ComNets-Bremen/MoleNet/experiments/2026-power-consumption-and-voltage-measurement/data-sources/CNMoleNET-Data - data.csv

date and time (zulu, UTC) | device id | BME 280 |  |  | DS18B20 | TEROS 11/12 |  | TEROS 11/12 | TEROS 12 | Battery | raw data
 |  | humidity (%) | air pressure (hPa) | temp (°C) | temp (°C) | vwc (m^3/m^3) | temp (°C) | perm (raw) | econ (µS/cm) | U (V)
2026-05-27T22:04:44.877791803Z | igc-2025-06-19-otaa | 44.3 | 1,027 | 24.2 | 23.3 | 0.5% | 23.4 | 1806.16 | 0 | 4.8 | {"bme_hum":44.25,"bme_pres":1027.02001953125,"bme_temp":24.15999984741211,"ds_temp":23.3125,"soil_econ":0,"soil_perm":1806.1600341796875,"soil_temp":23.399999618530273,"vr_voltage":4.772337913513184}
2026-05-27T22:05:53.288547001Z | igc-2025-06-19-otaa | 44.7 | 1,027 | 24.2 | 23.3 | 0.5% | 23.5 | 1806.46 | 0 | 4.8 | {"bme_hum":44.720001220703125,"bme_pres":1027.02001953125,"bme_temp":24.15999984741211,"ds_temp":23.3125,"soil_econ":0,"soil_perm":1806.4599609375,"soil_temp":23.5,"vr_voltage":4.771189212799072}
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
