ComNets-Bremen/MoleNet/experiments/2024-LoRa_Gateway_for_WUSN/Field_Experiment/Field_experiment_2020_06_16.ods

jsonData.app_id | jsonData.dev_id | jsonData.hardware_serial | jsonData.port | jsonData.counter | jsonData.payload_raw | jsonData.payload_decoded | jsonData.metadata.time | jsonData.metadata.frequency | jsonData.metadata.modulation | jsonData.metadata.data_rate | jsonData.metadata.coding_rate | jsonData.metadata.downlink_url | gateway.gtw_id | gateway.timestamp | gateway.channel | gateway.rssi | gateway.snr | gateway.latitude | gateway.longitude | gateway.altitude | gateway.gtw_id | gateway.timestamp | gateway.channel | gateway.rssi | gateway.snr | gateway.latitude | gateway.longitude | gateway.altitude | gateway.gtw_id | gateway.timestamp | gateway.channel | gateway.rssi | gateway.snr | gateway.latitude | gateway.longitude | gateway.altitude
test_04_02_19 | pycomarduino | 0058924AB98D5AD4 | 1 | 0 | TW9pbgAAAAAAAAAAAAAAAAAAAAAAAAAAAAAAAAAAAAAAAAAAAAAAAA== | Moin | 2020-06-16T14:53:31.599425092Z | 867,1 | LORA | SF7BW125 | 4/5 | undefined | eui-fcc23dfffe0b696a | 3328727571 | 3 | -118 | -3,5 | undefined | undefined | undefined | eui-b827ebfffef74e1a | 2419173723 | 3 | -87 | 9,8 | undefined | undefined | undefined
test_04_02_19 | pycomarduino | 0058924AB98D5AD4 | 1 | 1 | WzJdIEQyMC8wNS8xOCB0MTI6MDAgVzAwMDAgVDAwMDAgPyAxICAgAA== | [2] D20/05/18 t12:00 W0000 T0000 ? 1 | 2020-06-16T14:54:06.672221982Z | 868,5 | LORA | SF7BW125 | 4/5 | undefined | eui-fcc23dfffe0b696a | 3363804923 | 2 | -111 | -0,5 | undefined | undefined | undefined | eui-b827ebfffef74e1a | 2454251091 | 2 | -81 | 6,8 | undefined | undefined | undefined
test_04_02_19 | pycomarduino | 0058924AB98D5AD4 | 1 | 2 | WzNdIEQyMC8wNS8xOCB0MTI6MDAgVzAwMDAgVDAwMDAgPyAxICAgAA== | [3] D20/05/18 t12:00 W0000 T0000 ? 1 | 2020-06-16T14:55:11.681204958Z | 868,1 | LORA | SF7BW125 | 4/5 | undefined | eui-b827ebfffef74e1a | 2519256003 | 0 | -84 | 9 | undefined | undefined | undefined
test_04_02_19 | pycomarduino | 0058924AB98D5AD4 | 1 | 3 | WzRdIEQyMC8wNS8xOCB0MTI6MDAgVzAwMDAgVDAwMDAgPyAxICAgAA== | [4] D20/05/18 t12:00 W0000 T0000 ? 1 | 2020-06-16T14:56:08.033887854Z | 867,3 | LORA | SF7BW125 | 4/5 | undefined | eui-fcc23dfffe0b696a | 3485164443 | 4 | -113 | -1 | undefined | undefined | undefined | eui-b827ebfffef74e1a | 2575610667 | 4 | -89 | 9,8 | undefined | undefined | undefined
test_04_02_19 | pycomarduino | 0058924AB98D5AD4 | 1 | 4 | WzVdIEQyMC8wNS8xOCB0MTI6MDAgVzAwMDAgVDAwMDAgPyAxICAgAA== | [5] D20/05/18 t12:00 W0000 T0000 ? 1 | 2020-06-16T14:57:21.798522547Z | 868,3 | LORA | SF7BW125 | 4/5 | undefined | eui-b827ebfffef74e1a | 2649370019 | 1 | -84 | 9,5 | undefined | undefined | undefined
test_04_02_19 | pycomarduino | 0058924AB98D5AD4 | 1 | 5 | WzJdIEQyMC8wNS8xOCB0MTI6MDAgVzAwMDAgVDAwMDAgPyAxICAgAA== | [2] D20/05/18 t12:00 W0000 T0000 ? 1 | 2020-06-16T15:14:06.673642956Z | 868,5 | LORA | SF7BW125 | 4/5 | undefined | eui-fcc23dfffe0b696a | 268839363 | 2 | -110 | -5 | undefined | undefined | undefined | eui-b827ebfffef74e1a | 3654253363 | 2 | -79 | 8,2 | undefined | undefined | undefined
test_04_02_19 | pycomarduino | 0058924AB98D5AD4 | 1 | 6 | WzNdIEQyMC8wNS8xOCB0MTI6MDAgVzAwMDAgVDAwMDAgPyAxICAgAA== | [3] D20/05/18 t12:00 W0000 T0000 ? 1 | 2020-06-16T15:15:11.674569835Z | 867,5 | LORA | SF7BW125 | 4/5 | undefined | eui-fcc23dfffe0b696a | 333838172 | 5 | -113 | -2,5 | undefined | undefined | undefined | eui-b827ebfffef74e1a | 3719252204 | 5 | -82 | 8,2 | undefined | undefined | undefined
test_04_02_19 | pycomarduino | 0058924AB98D5AD4 | 1 | 7 | WzRdIEQyMC8wNS8xOCB0MTI6MDAgVzAwMDAgVDAwMDAgPyAxICAgAA== | [4] D20/05/18 t12:00 W0000 T0000 ? 1 | 2020-06-16T15:16:08.037091434Z | 868,1 | LORA | SF7BW125 | 4/5 | undefined | eui-b827ebfffef74e1a | 3775609667 | 0 | -83 | 10,5 | undefined | undefined | undefined
test_04_02_19 | pycomarduino | 0058924AB98D5AD4 | 1 | 8 | WzVdIEQyMC8wNS8xOCB0MTI6MDAgVzAwMDAgVDAwMDAgPyAxICAgAA== | [5] D20/05/18 t12:00 W0000 T0000 ? 1 | 2020-06-16T15:17:21.792934437Z | 868,3 | LORA | SF7BW125 | 4/5 | undefined | eui-b827ebfffef74e1a | 3849370235 | 1 | -79 | 9 | undefined | undefined | undefined
test_04_02_19 | pycomarduino | 0058924AB98D5AD4 | 1 | 9 | WzJdIEQyMC8wNS8xOCB0MTI6MDAgVzAwMDAgVDAwMDAgPyAxICAgAA== | [2] D20/05/18 t12:00 W0000 T0000 ? 1 | 2020-06-16T15:34:06.673976816Z | 867,7 | LORA | SF7BW125 | 4/5 | undefined | eui-b827ebfffef74e1a | 559288812 | 6 | -81 | 9,5 | undefined | undefined | undefined
test_04_02_19 | pycomarduino | 0058924AB98D5AD4 | 1 | 10 | WzNdIEQyMC8wNS8xOCB0MTI6MDAgVzAwMDAgVDAwMDAgPyAxICAgAA== | [3] D20/05/18 t12:00 W0000 T0000 ? 1 | 2020-06-16T15:35:11.670229955Z | 868,5 | LORA | SF7BW125 | 4/5 | undefined | eui-fcc23dfffe0b696a | 1533834427 | 2 | -113 | -0,2 | undefined | undefined | undefined | eui-b827ebfffef74e1a | 624281723 | 2 | -78 | 7,8 | undefined | undefined | undefined
test_04_02_19 | pycomarduino | 0058924AB98D5AD4 | 1 | 11 | WzRdIEQyMC8wNS8xOCB0MTI6MDAgVzAwMDAgVDAwMDAgPyAxICAgAA== | [4] D20/05/18 t12:00 W0000 T0000 ? 1 | 2020-06-16T15:36:08.033661887Z | 868,1 | LORA | SF7BW125 | 4/5 | undefined | eui-fcc23dfffe0b696a | 1590194867 | 0 | -116 | -0,8 | undefined | undefined | undefined | eui-b827ebfffef74e1a | 680642187 | 0 | -80 | 9,2 | undefined | undefined | undefined
test_04_02_19 | pycomarduino | 0058924AB98D5AD4 | 1 | 12 | WzVdIEQyMC8wNS8xOCB0MTI6MDAgVzAwMDAgVDAwMDAgPyAxICAgAA== | [5] D20/05/18 t12:00 W0000 T0000 ? 1 | 2020-06-16T15:37:21.792145476Z | 867,9 | LORA | SF7BW125 | 4/5 | undefined | eui-fcc23dfffe0b696a | 1663957532 | 7 | -114 | -3,8 | undefined | undefined | undefined | eui-b827ebfffef74e1a | 754404892 | 7 | -81 | 8,8 | undefined | undefined | undefined
test_04_02_19 | pycomarduino | 0058924AB98D5AD4 | 1 | 13 | WzJdIEQyMC8wNS8xOCB0MTI6MDAgVzAwMDAgVDAwMDAgPyAxICAgAA== | [2] D20/05/18 t12:00 W0000 T0000 ? 1 | 2020-06-16T15:54:06.68129469Z | 868,3 | LORA | SF7BW125 | 4/5 | undefined | eui-fcc23dfffe0b696a | 2668845763 | 1 | -109 | -2 | undefined | undefined | undefined | eui-b827ebfffef74e1a | 1759293595 | 1 | -78 | 9,2 | undefined | undefined | undefined
test_04_02_19 | pycomarduino | 0058924AB98D5AD4 | 1 | 14 | WzNdIEQyMC8wNS8xOCB0MTI6MDAgVzAwMDAgVDAwMDAgPyAxICAgAA== | [3] D20/05/18 t12:00 W0000 T0000 ? 1 | 2020-06-16T15:55:12.092174171Z | 867,1 | LORA | SF7BW125 | 4/5 | undefined | eui-fcc23dfffe0a9698 | 2735896363 | 3 | -117 | -6,5 | undefined | undefined | undefined | eui-fcc23dfffe0b696a | 2733832667 | 3 | -113 | 0,5 | undefined | undefined | undefined
test_04_02_19 | pycomarduino | 0058924AB98D5AD4 | 1 | 15 | WzRdIEQyMC8wNS8xOCB0MTI6MDAgVzAwMDAgVDAwMDAgPyAxICAgAA== | [4] D20/05/18 t12:00 W0000 T0000 ? 1 | 2020-06-16T15:56:08.032269197Z | 868,5 | LORA | SF7BW125 | 4/5 | undefined | eui-fcc23dfffe0b696a | 2790196011 | 2 | -112 | 2 | undefined | undefined | undefined | eui-b827ebfffef74e1a | 1880643899 | 2 | -81 | 8,2 | undefined | undefined | undefined
test_04_02_19 | pycomarduino | 0058924AB98D5AD4 | 1 | 16 | WzVdIEQyMC8wNS8xOCB0MTI6MDAgVzAwMDAgVDAwMDAgPyAxICAgAA== | [5] D20/05/18 t12:00 W0000 T0000 ? 1 | 2020-06-16T15:57:21.802305841Z | 868,1 | LORA | SF7BW125 | 4/5 | undefined | eui-fcc23dfffe0b696a | 2863960219 | 0 | -114 | 0 | undefined | undefined | undefined | eui-b827ebfffef74e1a | 1954408147 | 0 | -81 | 9,2 | undefined | undefined | undefined
test_04_02_19 | pycomarduino | 0058924AB98D5AD4 | 1 | 17 | WzJdIEQyMC8wNS8xOCB0MTI6MDAgVzAwMDAgVDAwMDAgPyAxICAgAA== | [2] D20/05/18 t12:00 W0000 T0000 ? 1 | 2020-06-16T16:14:06.683690365Z | 867,3 | LORA | SF7BW125 | 4/5 | undefined | eui-fcc23dfffe0a9698 | 3870911195 | 4 | -114 | -7 | undefined | undefined | undefined | eui-fcc23dfffe0b696a | 3868847787 | 4 | -116 | -0,5 | undefined | undefined | undefined | eui-b827ebfffef74e1a | 2959296179 | 4 | -83 | 9,5 | undefined | undefined | undefined
test_04_02_19 | pycomarduino | 0058924AB98D5AD4 | 1 | 18 | WzNdIEQyMC8wNS8xOCB0MTI6MDAgVzAwMDAgVDAwMDAgPyAxICAgAA== | [3] D20/05/18 t12:00 W0000 T0000 ? 1 | 2020-06-16T16:15:11.673342268Z | 868,3 | LORA | SF7BW125 | 4/5 | undefined | eui-b827ebfffef74e1a | 3024277347 | 1 | -81 | 9,2 | undefined | undefined | undefined
test_04_02_19 | pycomarduino | 0058924AB98D5AD4 | 1 | 19 | WzRdIEQyMC8wNS8xOCB0MTI6MDAgVzAwMDAgVDAwMDAgPyAxICAgAA== | [4] D20/05/18 t12:00 W0000 T0000 ? 1 | 2020-06-16T16:16:08.036932471Z | 868,5 | LORA | SF7BW125 | 4/5 | undefined | eui-b827ebfffef74e1a | 3080643547 | 2 | -81 | 8 | undefined | undefined | undefined
test_04_02_19 | pycomarduino | 0058924AB98D5AD4 | 1 | 20 | WzVdIEQyMC8wNS8xOCB0MTI6MDAgVzAwMDAgVDAwMDAgPyAxICAgAA== | [5] D20/05/18 t12:00 W0000 T0000 ? 1 | 2020-06-16T16:17:21.795494424Z | 867,5 | LORA | SF7BW125 | 4/5 | undefined | eui-fcc23dfffe0b696a | 4063960396 | 5 | -110 | 1 | undefined | undefined | undefined | eui-b827ebfffef74e1a | 3154408876 | 5 | -82 | 6,5 | undefined | undefined | undefined
test_04_02_19 | pycomarduino | 0058924AB98D5AD4 | 1 | 21 | WzJdIEQyMC8wNS8xOCB0MTI6MDAgVzAwMDAgVDAwMDAgPyAxICAgAA== | [2] D20/05/18 t12:00 W0000 T0000 ? 1 | 2020-06-16T16:34:06.686978924Z | 868,1 | LORA | SF7BW125 | 4/5 | undefined | eui-fcc23dfffe0b696a | 773884587 | 0 | -115 | -5,2 | undefined | undefined | undefined | eui-b827ebfffef74e1a | 4159300827 | 0 | -81 | 9,2 | undefined | undefined | undefined
test_04_02_19 | pycomarduino | 0058924AB98D5AD4 | 1 | 22 | WzNdIEQyMC8wNS8xOCB0MTI6MDAgVzAwMDAgVDAwMDAgPyAxICAgAA== | [3] D20/05/18 t12:00 W0000 T0000 ? 1 | 2020-06-16T16:35:11.668860894Z | 867,7 | LORA | SF7BW125 | 4/5 | undefined | eui-fcc23dfffe0b696a | 838859828 | 6 | -116 | -4,8 | undefined | undefined | undefined | eui-b827ebfffef74e1a | 4224276100 | 6 | -82 | 9,2 | undefined | undefined | undefined
test_04_02_19 | pycomarduino | 0058924AB98D5AD4 | 1 | 23 | WzRdIEQyMC8wNS8xOCB0MTI6MDAgVzAwMDAgVDAwMDAgPyAxICAgAA== | [4] D20/05/18 t12:00 W0000 T0000 ? 1 | 2020-06-16T16:36:08.064774084Z | 868,3 | LORA | SF7BW125 | 4/5 | undefined | eui-b827ebfffef74e1a | 4280645107 | 1 | -81 | 10,8 | undefined | undefined | undefined
test_04_02_19 | pycomarduino | 0058924AB98D5AD4 | 1 | 24 | WzVdIEQyMC8wNS8xOCB0MTI6MDAgVzAwMDAgVDAwMDAgPyAxICAgAA== | [5] D20/05/18 t12:00 W0000 T0000 ? 1 | 2020-06-16T16:37:21.796384426Z | 868,5 | LORA | SF7BW125 | 4/5 | undefined | eui-fcc23dfffe0b696a | 968995283 | 2 | -111 | 0,8 | undefined | undefined | undefined | eui-b827ebfffef74e1a | 59444323 | 2 | -81 | 7,5 | undefined | undefined | undefined
test_04_02_19 | pycomarduino | 0058924AB98D5AD4 | 1 | 25 | WzJdIEQyMC8wNS8xOCB0MTI6MDAgVzAwMDAgVDAwMDAgPyAxICAgAA== | [2] D20/05/18 t12:00 W0000 T0000 ? 1 | 2020-06-16T16:54:06.693254479Z | 867,9 | LORA | SF7BW125 | 4/5 | undefined | eui-fcc23dfffe0b696a | 1973886556 | 7 | -116 | -1 | undefined | undefined | undefined | eui-b827ebfffef74e1a | 1064336052 | 7 | -84 | 10,8 | undefined | undefined | undefined
test_04_02_19 | pycomarduino | 0058924AB98D5AD4 | 1 | 26 | WzNdIEQyMC8wNS8xOCB0MTI6MDAgVzAwMDAgVDAwMDAgPyAxICAgAA== | [3] D20/05/18 t12:00 W0000 T0000 ? 1 | 2020-06-16T16:55:11.660936483Z | 868,1 | LORA | SF7BW125 | 4/5 | undefined | eui-fcc23dfffe0b696a | 2038855931 | 0 | -116 | -2 | undefined | undefined | undefined | eui-b827ebfffef74e1a | 1129305459 | 0 | -82 | 9 | undefined | undefined | undefined
test_04_02_19 | pycomarduino | 0058924AB98D5AD4 | 1 | 27 | WzRdIEQyMC8wNS8xOCB0MTI6MDAgVzAwMDAgVDAwMDAgPyAxICAgAA== | [4] D20/05/18 t12:00 W0000 T0000 ? 1 | 2020-06-16T16:56:08.03732124Z | 868,3 | LORA | SF7BW125 | 4/5 | undefined | eui-b827ebfffef74e1a | 1185677387 | 1 | -83 | 10,5 | undefined | undefined | undefined
test_04_02_19 | pycomarduino | 0058924AB98D5AD4 | 1 | 28 | WzVdIEQyMC8wNS8xOCB0MTI6MDAgVzAwMDAgVDAwMDAgPyAxICAgAA== | [5] D20/05/18 t12:00 W0000 T0000 ? 1 | 2020-06-16T16:57:21.795728348Z | 867,1 | LORA | SF7BW125 | 4/5 | undefined | eui-fcc23dfffe0a9698 | 2171058003 | 3 | -117 | -6,2 | undefined | undefined | undefined | eui-fcc23dfffe0b696a | 2168995275 | 3 | -117 | 0,2 | undefined | undefined | undefined | eui-b827ebfffef74e1a | 1259444867 | 3 | -89 | 10 | undefined | undefined | undefined
test_04_02_19 | pycomarduino | 0058924AB98D5AD4 | 1 | 29 | WzJdIEQyMC8wNS8xOCB0MTI6MDAgVzAwMDAgVDAwMDAgPyAxICAgAA== | [2] D20/05/18 t12:00 W0000 T0000 ? 1 | 2020-06-16T17:14:06.811791944Z | 868,5 | LORA | SF7BW125 | 4/5 | undefined | eui-fcc23dfffe0b696a | 3173890507 | 2 | -112 | -1 | undefined | undefined | undefined | eui-b827ebfffef74e1a | 2264340579 | 2 | -78 | 7,2 | undefined | undefined | undefined
test_04_02_19 | pycomarduino | 0058924AB98D5AD4 | 1 | 30 | WzNdIEQyMC8wNS8xOCB0MTI6MDAgVzAwMDAgVDAwMDAgPyAxICAgAA== | [3] D20/05/18 t12:00 W0000 T0000 ? 1 | 2020-06-16T17:15:11.66316184Z | 867,3 | LORA | SF7BW125 | 4/5 | undefined | eui-fcc23dfffe0b696a | 3238853939 | 4 | -112 | -0,2 | undefined | undefined | undefined | eui-b827ebfffef74e1a | 2329304043 | 4 | -84 | 8,8 | undefined | undefined | undefined
test_04_02_19 | pycomarduino | 0058924AB98D5AD4 | 1 | 31 | WzRdIEQyMC8wNS8xOCB0MTI6MDAgVzAwMDAgVDAwMDAgPyAxICAgAA== | [4] D20/05/18 t12:00 W0000 T0000 ? 1 | 2020-06-16T17:16:08.035037617Z | 868,1 | LORA | SF7BW125 | 4/5 | undefined | eui-fcc23dfffe0b696a | 3295228675 | 0 | -117 | -2,8 | undefined | undefined | undefined | eui-b827ebfffef74e1a | 2385678795 | 0 | -80 | 9,5 | undefined | undefined | undefined
test_04_02_19 | pycomarduino | 0058924AB98D5AD4 | 1 | 32 | WzVdIEQyMC8wNS8xOCB0MTI6MDAgVzAwMDAgVDAwMDAgPyAxICAgAA== | [5] D20/05/18 t12:00 W0000 T0000 ? 1 | 2020-06-16T17:17:21.858784072Z | 868,3 | LORA | SF7BW125 | 4/5 | undefined | eui-b827ebfffef74e1a | 2459447443 | 1 | -83 | 10,5 | undefined | undefined | undefined
test_04_02_19 | pycomarduino | 0058924AB98D5AD4 | 1 | 33 | WzJdIEQyMC8wNS8xOCB0MTI6MDAgVzAwMDAgVDAwMDAgPyAxICAgAA== | [2] D20/05/18 t12:00 W0000 T0000 ? 1 | 2020-06-16T17:34:06.705127726Z | 867,5 | LORA | SF7BW125 | 4/5 | undefined | eui-fcc23dfffe0b696a | 78925188 | 5 | -113 | -0,8 | undefined | undefined | undefined | eui-b827ebfffef74e1a | 3464343124 | 5 | -83 | 7,5 | undefined | undefined | undefined
test_04_02_19 | pycomarduino | 0058924AB98D5AD4 | 1 | 34 | WzNdIEQyMC8wNS8xOCB0MTI6MDAgVzAwMDAgVDAwMDAgPyAxICAgAA== | [3] D20/05/18 t12:00 W0000 T0000 ? 1 | 2020-06-16T17:35:11.658218556Z | 868,5 | LORA | SF7BW125 | 4/5 | undefined | eui-fcc23dfffe0b696a | 143882587 | 2 | -112 | 0,5 | undefined | undefined | undefined | eui-b827ebfffef74e1a | 3529300563 | 2 | -78 | 6,2 | undefined | undefined | undefined
test_04_02_19 | pycomarduino | 0058924AB98D5AD4 | 1 | 35 | WzRdIEQyMC8wNS8xOCB0MTI6MDAgVzAwMDAgVDAwMDAgPyAxICAgAA== | [4] D20/05/18 t12:00 W0000 T0000 ? 1 | 2020-06-16T17:36:08.030161564Z | 868,1 | LORA | SF7BW125 | 4/5 | undefined | eui-fcc23dfffe0b696a | 200260139 | 0 | -115 | -0,5 | undefined | undefined | undefined | eui-b827ebfffef74e1a | 3585678139 | 0 | -84 | 10,5 | undefined | undefined | undefined
test_04_02_19 | pycomarduino | 0058924AB98D5AD4 | 1 | 36 | WzVdIEQyMC8wNS8xOCB0MTI6MDAgVzAwMDAgVDAwMDAgPyAxICAgAA== | [5] D20/05/18 t12:00 W0000 T0000 ? 1 | 2020-06-16T17:37:21.808602749Z | 867,7 | LORA | SF7BW125 | 4/5 | undefined | eui-fcc23dfffe0b696a | 274029788 | 6 | -116 | -6,2 | undefined | undefined | undefined | eui-b827ebfffef74e1a | 3659447820 | 6 | -83 | 10 | undefined | undefined | undefined
test_04_02_19 | pycomarduino | 0058924AB98D5AD4 | 1 | 37 | WzJdIEQyMC8wNS8xOCB0MTI6MDAgVzAwMDAgVDAwMDAgPyAxICAgAA== | [2] D20/05/18 t12:00 W0000 T0000 ? 1 | 2020-06-16T17:54:06.856794594Z | 868,3 | LORA | SF7BW125 | 4/5 | undefined | eui-b827ebfffef74e1a | 369534723 | 1 | -81 | 9,2 | undefined | undefined | undefined
test_04_02_19 | pycomarduino | 0058924AB98D5AD4 | 1 | 38 | WzNdIEQyMC8wNS8xOCB0MTI6MDAgVzAwMDAgVDAwMDAgPyAxICAgAA== | [3] D20/05/18 t12:00 W0000 T0000 ? 1 | 2020-06-16T17:55:11.65666038Z | 867,9 | LORA | SF7BW125 | 4/5 | undefined | eui-fcc23dfffe0b696a | 1343880468 | 7 | -117 | -2,2 | undefined | undefined | undefined | eui-b827ebfffef74e1a | 434331716 | 7 | -84 | 9,5 | undefined | undefined | undefined
test_04_02_19 | pycomarduino | 0058924AB98D5AD4 | 1 | 39 | WzRdIEQyMC8wNS8xOCB0MTI6MDAgVzAwMDAgVDAwMDAgPyAxICAgAA== | [4] D20/05/18 t12:00 W0000 T0000 ? 1 | 2020-06-16T17:56:08.186396041Z | 868,5 | LORA | SF7BW125 | 4/5 | undefined | eui-fcc23dfffe0b696a | 1400409291 | 2 | -111 | -1,5 | undefined | undefined | undefined | eui-b827ebfffef74e1a | 490860571 | 2 | -81 | 7,2 | undefined | undefined | undefined
test_04_02_19 | pycomarduino | 0058924AB98D5AD4 | 1 | 40 | WzVdIEQyMC8wNS8xOCB0MTI6MDAgVzAwMDAgVDAwMDAgPyAxICAgAA== | [5] D20/05/18 t12:00 W0000 T0000 ? 1 | 2020-06-16T17:57:21.805076581Z | 868,1 | LORA | SF7BW125 | 4/5 | undefined | eui-fcc23dfffe0b696a | 1474031643 | 0 | -117 | -1,8 | undefined | undefined | undefined | eui-b827ebfffef74e1a | 564482955 | 0 | -83 | 10 | undefined | undefined | undefined
test_04_02_19 | pycomarduino | 0058924AB98D5AD4 | 1 | 41 | WzJdIEQyMC8wNS8xOCB0MTI6MDAgVzAwMDAgVDAwMDAgPyAxICAgAA== | [2] D20/05/18 t12:00 W0000 T0000 ? 1 | 2020-06-16T18:14:06.707336104Z | 867,1 | LORA | SF7BW125 | 4/5 | undefined | eui-fcc23dfffe0b696a | 2478931003 | 3 | -113 | 0,5 | undefined | undefined | undefined | eui-b827ebfffef74e1a | 1569382803 | 3 | -88 | 8,8 | undefined | undefined | undefined
test_04_02_19 | pycomarduino | 0058924AB98D5AD4 | 1 | 42 | WzNdIEQyMC8wNS8xOCB0MTI6MDAgVzAwMDAgVDAwMDAgPyAxICAgAA== | [3] D20/05/18 t12:00 W0000 T0000 ? 1 | 2020-06-16T18:15:11.651606129Z | 868,3 | LORA | SF7BW125 | 4/5 | undefined | eui-b827ebfffef74e1a | 1634328195 | 1 | -81 | 10,5 | undefined | undefined | undefined
test_04_02_19 | pycomarduino | 0058924AB98D5AD4 | 1 | 43 | WzRdIEQyMC8wNS8xOCB0MTI6MDAgVzAwMDAgVDAwMDAgPyAxICAgAA== | [4] D20/05/18 t12:00 W0000 T0000 ? 1 | 2020-06-16T18:16:08.030428368Z | 868,5 | LORA | SF7BW125 | 4/5 | undefined | eui-b827ebfffef74e1a | 1690711299 | 2 | -79 | 7,2 | undefined | undefined | undefined
test_04_02_19 | pycomarduino | 0058924AB98D5AD4 | 1 | 44 | WzVdIEQyMC8wNS8xOCB0MTI6MDAgVzAwMDAgVDAwMDAgPyAxICAgAA== | [5] D20/05/18 t12:00 W0000 T0000 ? 1 | 2020-06-16T18:17:21.845341058Z | 867,3 | LORA | SF7BW125 | 4/5 | undefined | eui-fcc23dfffe0b696a | 2674031459 | 4 | -116 | -1,2 | undefined | undefined | undefined
test_04_02_19 | pycomarduino | 0058924AB98D5AD4 | 1 | 45 | WzJdIEQyMC8wNS8xOCB0MTI6MDAgVzAwMDAgVDAwMDAgPyAxICAgAA== | [2] D20/05/18 t12:00 W0000 T0000 ? 1 | 2020-06-16T18:34:06.705918387Z | 868,1 | LORA | SF7BW125 | 4/5 | undefined | eui-fcc23dfffe0b696a | 3678934891 | 0 | -116 | -3,2 | undefined | undefined | undefined | eui-b827ebfffef74e1a | 2769387267 | 0 | -83 | 8,8 | undefined | undefined | undefined
test_04_02_19 | pycomarduino | 0058924AB98D5AD4 | 1 | 46 | WzNdIEQyMC8wNS8xOCB0MTI6MDAgVzAwMDAgVDAwMDAgPyAxICAgAA== | [3] D20/05/18 t12:00 W0000 T0000 ? 1 | 2020-06-16T18:35:11.647147708Z | 867,5 | LORA | SF7BW125 | 4/5 | undefined | eui-fcc23dfffe0b696a | 3743874124 | 5 | -113 | -1 | undefined | undefined | undefined | eui-b827ebfffef74e1a | 2834326524 | 5 | -85 | 7,5 | undefined | undefined | undefined
test_04_02_19 | pycomarduino | 0058924AB98D5AD4 | 1 | 47 | WzRdIEQyMC8wNS8xOCB0MTI6MDAgVzAwMDAgVDAwMDAgPyAxICAgAA== | [4] D20/05/18 t12:00 W0000 T0000 ? 1 | 2020-06-16T18:36:08.03216962Z | 868,3 | LORA | SF7BW125 | 4/5 | undefined | eui-b827ebfffef74e1a | 2890712443 | 1 | -79 | 9,8 | undefined | undefined | undefined
test_04_02_19 | pycomarduino | 0058924AB98D5AD4 | 1 | 48 | WzVdIEQyMC8wNS8xOCB0MTI6MDAgVzAwMDAgVDAwMDAgPyAxICAgAA== | [5] D20/05/18 t12:00 W0000 T0000 ? 1 | 2020-06-16T18:37:21.806620651Z | 868,5 | LORA | SF7BW125 | 4/5 | undefined | eui-fcc23dfffe0b696a | 3874033171 | 2 | -115 | -0,8 | undefined | undefined | undefined | eui-b827ebfffef74e1a | 2964485635 | 2 | -81 | 7,2 | undefined | undefined | undefined
test_04_02_19 | pycomarduino | 0058924AB98D5AD4 | 1 | 49 | WzJdIEQyMC8wNS8xOCB0MTI6MDAgVzAwMDAgVDAwMDAgPyAxICAgAA== | [2] D20/05/18 t12:00 W0000 T0000 ? 1 | 2020-06-16T18:54:06.713331254Z | 867,7 | LORA | SF7BW125 | 4/5 | undefined | eui-fcc23dfffe0b696a | 583969412 | 6 | -115 | -4,2 | undefined | undefined | undefined | eui-b827ebfffef74e1a | 3969389652 | 6 | -83 | 10,5 | undefined | undefined | undefined
test_04_02_19 | pycomarduino | 0058924AB98D5AD4 | 1 | 50 | WzNdIEQyMC8wNS8xOCB0MTI6MDAgVzAwMDAgVDAwMDAgPyAxICAgAA== | [3] D20/05/18 t12:00 W0000 T0000 ? 1 | 2020-06-16T18:55:11.648111888Z | 868,1 | LORA | SF7BW125 | 4/5 | undefined | eui-b827ebfffef74e1a | 4034322795 | 0 | -82 | 9,2 | undefined | undefined | undefined
test_04_02_19 | pycomarduino | 0058924AB98D5AD4 | 1 | 51 | WzRdIEQyMC8wNS8xOCB0MTI6MDAgVzAwMDAgVDAwMDAgPyAxICAgAA== | [4] D20/05/18 t12:00 W0000 T0000 ? 1 | 2020-06-16T18:56:08.035486607Z | 868,3 | LORA | SF7BW125 | 4/5 | undefined | eui-b827ebfffef74e1a | 4090711435 | 1 | -81 | 11 | undefined | undefined | undefined
test_04_02_19 | pycomarduino | 0058924AB98D5AD4 | 1 | 52 | WzVdIEQyMC8wNS8xOCB0MTI6MDAgVzAwMDAgVDAwMDAgPyAxICAgAA== | [5] D20/05/18 t12:00 W0000 T0000 ? 1 | 2020-06-16T18:57:21.807250315Z | 867,9 | LORA | SF7BW125 | 4/5 | undefined | eui-fcc23dfffe0b696a | 779065564 | 7 | -117 | -0,2 | undefined | undefined | undefined | eui-b827ebfffef74e1a | 4164485900 | 7 | -83 | 9,2 | undefined | undefined | undefined
test_04_02_19 | pycomarduino | 0058924AB98D5AD4 | 1 | 53 | WzJdIEQyMC8wNS8xOCB0MTI6MDAgVzAwMDAgVDAwMDAgPyAxICAgAA== | [2] D20/05/18 t12:00 W0000 T0000 ? 1 | 2020-06-16T19:14:06.73096524Z | 868,5 | LORA | SF7BW125 | 4/5 | undefined | eui-b827ebfffef74e1a | 874426843 | 2 | -81 | 8 | undefined | undefined | undefined
test_04_02_19 | pycomarduino | 0058924AB98D5AD4 | 1 | 54 | WzNdIEQyMC8wNS8xOCB0MTI6MDAgVzAwMDAgVDAwMDAgPyAxICAgAA== | [3] D20/05/18 t12:00 W0000 T0000 ? 1 | 2020-06-16T19:15:11.646600965Z | 867,1 | LORA | SF7BW125 | 4/5 | undefined | eui-fcc23dfffe0a9698 | 1850960923 | 3 | -117 | -9 | undefined | undefined | undefined | eui-fcc23dfffe0b696a | 1848900203 | 3 | -113 | -2,8 | undefined | undefined | undefined | eui-b827ebfffef74e1a | 939353747 | 3 | -86 | 10,2 | undefined | undefined | undefined
test_04_02_19 | pycomarduino | 0058924AB98D5AD4 | 1 | 55 | WzRdIEQyMC8wNS8xOCB0MTI6MDAgVzAwMDAgVDAwMDAgPyAxICAgAA== | [4] D20/05/18 t12:00 W0000 T0000 ? 1 | 2020-06-16T19:16:08.037142403Z | 868,1 | LORA | SF7BW125 | 4/5 | undefined | eui-b827ebfffef74e1a | 995745203 | 0 | -81 | 9 | undefined | undefined | undefined
test_04_02_19 | pycomarduino | 0058924AB98D5AD4 | 1 | 56 | WzVdIEQyMC8wNS8xOCB0MTI6MDAgVzAwMDAgVDAwMDAgPyAxICAgAA== | [5] D20/05/18 t12:00 W0000 T0000 ? 1 | 2020-06-16T19:17:21.812371625Z | 868,3 | LORA | SF7BW125 | 4/5 | undefined | eui-fcc23dfffe0b696a | 1979067235 | 1 | -112 | -4 | undefined | undefined | undefined | eui-b827ebfffef74e1a | 1069520843 | 1 | -81 | 9,2 | undefined | undefined | undefined
test_04_02_19 | pycomarduino | 0058924AB98D5AD4 | 1 | 57 | WzJdIEQyMC8wNS8xOCB0MTI6MDAgVzAwMDAgVDAwMDAgPyAxICAgAA== | [2] D20/05/18 t12:00 W0000 T0000 ? 1 | 2020-06-16T19:34:06.721668491Z | 867,3 | LORA | SF7BW125 | 4/5 | undefined | eui-fcc23dfffe0b696a | 2983975147 | 4 | -115 | -5 | undefined | undefined | undefined | eui-b827ebfffef74e1a | 2074429219 | 4 | -84 | 9,8 | undefined | undefined | undefined
test_04_02_19 | pycomarduino | 0058924AB98D5AD4 | 1 | 58 | WzNdIEQyMC8wNS8xOCB0MTI6MDAgVzAwMDAgVDAwMDAgPyAxICAgAA== | [3] D20/05/18 t12:00 W0000 T0000 ? 1 | 2020-06-16T19:35:11.638425649Z | 868,5 | LORA | SF7BW125 | 4/5 | undefined | eui-fcc23dfffe0b696a | 3048895835 | 2 | -112 | -2,8 | undefined | undefined | undefined | eui-b827ebfffef74e1a | 2139349939 | 2 | -79 | 6,8 | undefined | undefined | undefined
test_04_02_19 | pycomarduino | 0058924AB98D5AD4 | 1 | 59 | WzRdIEQyMC8wNS8xOCB0MTI6MDAgVzAwMDAgVDAwMDAgPyAxICAgAA== | [4] D20/05/18 t12:00 W0000 T0000 ? 1 | 2020-06-16T19:36:08.035496285Z | 868,1 | LORA | SF7BW125 | 4/5 | undefined | eui-b827ebfffef74e1a | 2195744275 | 0 | -83 | 9,8 | undefined | undefined | undefined
test_04_02_19 | pycomarduino | 0058924AB98D5AD4 | 1 | 60 | WzVdIEQyMC8wNS8xOCB0MTI6MDAgVzAwMDAgVDAwMDAgPyAxICAgAA== | [5] D20/05/18 t12:00 W0000 T0000 ? 1 | 2020-06-16T19:37:21.811940195Z | 867,5 | LORA | SF7BW125 | 4/5 | undefined | eui-fcc23dfffe0b696a | 3179066860 | 5 | -113 | -3 | undefined | undefined | undefined | eui-b827ebfffef74e1a | 2269521028 | 5 | -83 | 7,8 | undefined | undefined | undefined
test_04_02_19 | pycomarduino | 0058924AB98D5AD4 | 1 | 61 | WzJdIEQyMC8wNS8xOCB0MTI6MDAgVzAwMDAgVDAwMDAgPyAxICAgAA== | [2] D20/05/18 t12:00 W0000 T0000 ? 1 | 2020-06-16T19:54:06.719805023Z | 868,3 | LORA | SF7BW125 | 4/5 | undefined | eui-b827ebfffef74e1a | 3274433683 | 1 | -81 | 9,5 | undefined | undefined | undefined
test_04_02_19 | pycomarduino | 0058924AB98D5AD4 | 1 | 62 | WzNdIEQyMC8wNS8xOCB0MTI6MDAgVzAwMDAgVDAwMDAgPyAxICAgAA== | [3] D20/05/18 t12:00 W0000 T0000 ? 1 | 2020-06-16T19:55:11.636192026Z | 867,7 | LORA | SF7BW125 | 4/5 | undefined | eui-fcc23dfffe0b696a | 4248893444 | 6 | -113 | -4,8 | undefined | undefined | undefined | eui-b827ebfffef74e1a | 3339348116 | 6 | -84 | 9,8 | undefined | undefined | undefined
test_04_02_19 | pycomarduino | 0058924AB98D5AD4 | 1 | 63 | WzRdIEQyMC8wNS8xOCB0MTI6MDAgVzAwMDAgVDAwMDAgPyAxICAgAA== | [4] D20/05/18 t12:00 W0000 T0000 ? 1 | 2020-06-16T19:56:08.035966461Z | 868,5 | LORA | SF7BW125 | 4/5 | undefined | eui-fcc23dfffe0b696a | 10323171 | 2 | -113 | -1,8 | undefined | undefined | undefined | eui-b827ebfffef74e1a | 3395745155 | 2 | -78 | 8 | undefined | undefined | undefined
test_04_02_19 | pycomarduino | 0058924AB98D5AD4 | 1 | 64 | WzVdIEQyMC8wNS8xOCB0MTI6MDAgVzAwMDAgVDAwMDAgPyAxICAgAA== | [5] D20/05/18 t12:00 W0000 T0000 ? 1 | 2020-06-16T19:57:21.816812731Z | 868,1 | LORA | SF7BW125 | 4/5 | undefined | eui-fcc23dfffe0b696a | 84101179 | 0 | -115 | -2,2 | undefined | undefined | undefined | eui-b827ebfffef74e1a | 3469523203 | 0 | -82 | 10,2 | undefined | undefined | undefined
test_04_02_19 | pycomarduino | 0058924AB98D5AD4 | 1 | 65 | WzJdIEQyMC8wNS8xOCB0MTI6MDAgVzAwMDAgVDAwMDAgPyAxICAgAA== | [2] D20/05/18 t12:00 W0000 T0000 ? 1 | 2020-06-16T20:14:06.722455355Z | 867,9 | LORA | SF7BW125 | 4/5 | undefined | eui-fcc23dfffe0b696a | 1089013436 | 7 | -117 | -3,2 | undefined | undefined | undefined | eui-b827ebfffef74e1a | 179468636 | 7 | -84 | 11 | undefined | undefined | undefined
test_04_02_19 | pycomarduino | 0058924AB98D5AD4 | 1 | 66 | WzNdIEQyMC8wNS8xOCB0MTI6MDAgVzAwMDAgVDAwMDAgPyAxICAgAA== | [3] D20/05/18 t12:00 W0000 T0000 ? 1 | 2020-06-16T20:15:11.652432523Z | 868,3 | LORA | SF7BW125 | 4/5 | undefined | eui-b827ebfffef74e1a | 244376931 | 1 | -81 | 9,8 | undefined | undefined | undefined
test_04_02_19 | pycomarduino | 0058924AB98D5AD4 | 1 | 67 | WzRdIEQyMC8wNS8xOCB0MTI6MDAgVzAwMDAgVDAwMDAgPyAxICAgAA== | [4] D20/05/18 t12:00 W0000 T0000 ? 1 | 2020-06-16T20:16:08.029278671Z | 868,5 | LORA | SF7BW125 | 4/5 | undefined | eui-fcc23dfffe0b696a | 1210321363 | 2 | -112 | 0 | undefined | undefined | undefined | eui-b827ebfffef74e1a | 300776627 | 2 | -79 | 7,5 | undefined | undefined | undefined
test_04_02_19 | pycomarduino | 0058924AB98D5AD4 | 1 | 68 | WzVdIEQyMC8wNS8xOCB0MTI6MDAgVzAwMDAgVDAwMDAgPyAxICAgAA== | [5] D20/05/18 t12:00 W0000 T0000 ? 1 | 2020-06-16T20:17:21.806154259Z | 867,1 | LORA | SF7BW125 | 4/5 | undefined | eui-fcc23dfffe0a9698 | 1286160547 | 3 | -116 | -8,2 | undefined | undefined | undefined | eui-fcc23dfffe0b696a | 1284100699 | 3 | -115 | -1 | undefined | undefined | undefined | eui-b827ebfffef74e1a | 374555987 | 3 | -85 | 10 | undefined | undefined | undefined
test_04_02_19 | pycomarduino | 0058924AB98D5AD4 | 1 | 69 | WzJdIEQyMC8wNS8xOCB0MTI6MDAgVzAwMDAgVDAwMDAgPyAxICAgAA== | [2] D20/05/18 t12:00 W0000 T0000 ? 1 | 2020-06-16T20:34:06.73326024Z | 868,1 | LORA | SF7BW125 | 4/5 | undefined | eui-fcc23dfffe0b696a | 2289017235 | 0 | -117 | -2,8 | undefined | undefined | undefined | eui-b827ebfffef74e1a | 1379473003 | 0 | -83 | 9,8 | undefined | undefined | undefined
test_04_02_19 | pycomarduino | 0058924AB98D5AD4 | 1 | 70 | WzNdIEQyMC8wNS8xOCB0MTI6MDAgVzAwMDAgVDAwMDAgPyAxICAgAA== | [3] D20/05/18 t12:00 W0000 T0000 ? 1 | 2020-06-16T20:35:11.632397635Z | 867,3 | LORA | SF7BW125 | 4/5 | undefined | eui-fcc23dfffe0b696a | 2353919235 | 4 | -112 | -1,5 | undefined | undefined | undefined | eui-b827ebfffef74e1a | 1444375035 | 4 | -85 | 10,8 | undefined | undefined | undefined
test_04_02_19 | pycomarduino | 0058924AB98D5AD4 | 1 | 71 | WzRdIEQyMC8wNS8xOCB0MTI6MDAgVzAwMDAgVDAwMDAgPyAxICAgAA== | [4] D20/05/18 t12:00 W0000 T0000 ? 1 | 2020-06-16T20:36:08.040241104Z | 868,3 | LORA | SF7BW125 | 4/5 | undefined | eui-fcc23dfffe0b696a | 2410321715 | 1 | -109 | -3,8 | undefined | undefined | undefined | eui-b827ebfffef74e1a | 1500777539 | 1 | -81 | 9 | undefined | undefined | undefined
test_04_02_19 | pycomarduino | 0058924AB98D5AD4 | 1 | 72 | WzVdIEQyMC8wNS8xOCB0MTI6MDAgVzAwMDAgVDAwMDAgPyAxICAgAA== | [5] D20/05/18 t12:00 W0000 T0000 ? 1 | 2020-06-16T20:37:21.819127054Z | 868,5 | LORA | SF7BW125 | 4/5 | undefined | eui-fcc23dfffe0b696a | 2484102251 | 2 | -113 | -0,5 | undefined | undefined | undefined | eui-b827ebfffef74e1a | 1574558107 | 2 | -81 | 7,8 | undefined | undefined | undefined
test_04_02_19 | pycomarduino | 0058924AB98D5AD4 | 1 | 73 | WzJdIEQyMC8wNS8xOCB0MTI6MDAgVzAwMDAgVDAwMDAgPyAxICAgAA== | [2] D20/05/18 t12:00 W0000 T0000 ? 1 | 2020-06-16T20:54:06.732563215Z | 867,5 | LORA | SF7BW125 | 4/5 | undefined | eui-fcc23dfffe0b696a | 3489019028 | 5 | -111 | -8 | undefined | undefined | undefined | eui-b827ebfffef74e1a | 2579475356 | 5 | -85 | 7,5 | undefined | undefined | undefined
test_04_02_19 | pycomarduino | 0058924AB98D5AD4 | 1 | 74 | WzNdIEQyMC8wNS8xOCB0MTI6MDAgVzAwMDAgVDAwMDAgPyAxICAgAA== | [3] D20/05/18 t12:00 W0000 T0000 ? 1 | 2020-06-16T20:55:11.626774127Z | 868,1 | LORA | SF7BW125 | 4/5 | undefined | eui-fcc23dfffe0b696a | 3553914683 | 0 | -116 | -0,5 | undefined | undefined | undefined | eui-b827ebfffef74e1a | 2644371043 | 0 | -83 | 10,5 | undefined | undefined | undefined
test_04_02_19 | pycomarduino | 0058924AB98D5AD4 | 1 | 75 | WzRdIEQyMC8wNS8xOCB0MTI6MDAgVzAwMDAgVDAwMDAgPyAxICAgAA== | [4] D20/05/18 t12:00 W0000 T0000 ? 1 | 2020-06-16T20:56:08.036184739Z | 868,3 | LORA | SF7BW125 | 4/5 | undefined | eui-b827ebfffef74e1a | 2700776331 | 1 | -83 | 10,8 | undefined | undefined | undefined
test_04_02_19 | pycomarduino | 0058924AB98D5AD4 | 1 | 76 | WzVdIEQyMC8wNS8xOCB0MTI6MDAgVzAwMDAgVDAwMDAgPyAxICAgAA== | [5] D20/05/18 t12:00 W0000 T0000 ? 1 | 2020-06-16T20:57:21.813268035Z | 867,7 | LORA | SF7BW125 | 4/5 | undefined | eui-fcc23dfffe0b696a | 3684101708 | 6 | -116 | -4,2 | undefined | undefined | undefined | eui-b827ebfffef74e1a | 2774558132 | 6 | -81 | 8 | undefined | undefined | undefined
test_04_02_19 | pycomarduino | 0058924AB98D5AD4 | 1 | 77 | WzJdIEQyMC8wNS8xOCB0MTI6MDAgVzAwMDAgVDAwMDAgPyAxICAgAA== | [2] D20/05/18 t12:00 W0000 T0000 ? 1 | 2020-06-16T21:14:06.734615488Z | 868,5 | LORA | SF7BW125 | 4/5 | undefined | eui-fcc23dfffe0b696a | 394055443 | 2 | -113 | -0,2 | undefined | undefined | undefined | eui-b827ebfffef74e1a | 3779479635 | 2 | -81 | 7,8 | undefined | undefined | undefined
test_04_02_19 | pycomarduino | 0058924AB98D5AD4 | 1 | 78 | WzNdIEQyMC8wNS8xOCB0MTI6MDAgVzAwMDAgVDAwMDAgPyAxICAgAA== | [3] D20/05/18 t12:00 W0000 T0000 ? 1 | 2020-06-16T21:15:11.626330959Z | 867,9 | LORA | SF7BW125 | 4/5 | undefined | eui-fcc23dfffe0b696a | 458944828 | 7 | -116 | -1,2 | undefined | undefined | undefined | eui-b827ebfffef74e1a | 3844369052 | 7 | -84 | 9,2 | undefined | undefined | undefined
test_04_02_19 | pycomarduino | 0058924AB98D5AD4 | 1 | 79 | WzRdIEQyMC8wNS8xOCB0MTI6MDAgVzAwMDAgVDAwMDAgPyAxICAgAA== | [4] D20/05/18 t12:00 W0000 T0000 ? 1 | 2020-06-16T21:16:08.039496924Z | 868,1 | LORA | SF7BW125 | 4/5 | undefined | eui-fcc23dfffe0b696a | 515352899 | 0 | -117 | -1 | undefined | undefined | undefined | eui-b827ebfffef74e1a | 3900777147 | 0 | -82 | 10,5 | undefined | undefined | undefined
test_04_02_19 | pycomarduino | 0058924AB98D5AD4 | 1 | 80 | WzVdIEQyMC8wNS8xOCB0MTI6MDAgVzAwMDAgVDAwMDAgPyAxICAgAA== | [5] D20/05/18 t12:00 W0000 T0000 ? 1 | 2020-06-16T21:17:21.813609748Z | 868,3 | LORA | SF7BW125 | 4/5 | undefined | eui-b827ebfffef74e1a | 3974560139 | 1 | -81 | 9,8 | undefined | undefined | undefined
test_04_02_19 | pycomarduino | 0058924AB98D5AD4 | 1 | 81 | WzJdIEQyMC8wNS8xOCB0MTI6MDAgVzAwMDAgVDAwMDAgPyAxICAgAA== | [2] D20/05/18 t12:00 W0000 T0000 ? 1 | 2020-06-16T21:34:06.733804887Z | 867,1 | LORA | SF7BW125 | 4/5 | undefined | eui-fcc23dfffe0b696a | 1594057115 | 3 | -112 | -1 | undefined | undefined | undefined | eui-b827ebfffef74e1a | 684514571 | 3 | -86 | 9,8 | undefined | undefined | undefined
test_04_02_19 | pycomarduino | 0058924AB98D5AD4 | 1 | 82 | WzNdIEQyMC8wNS8xOCB0MTI6MDAgVzAwMDAgVDAwMDAgPyAxICAgAA== | [3] D20/05/18 t12:00 W0000 T0000 ? 1 | 2020-06-16T21:35:11.620924954Z | 868,5 | LORA | SF7BW125 | 4/5 | undefined | eui-fcc23dfffe0b696a | 1658940235 | 2 | -113 | -0,2 | undefined | undefined | undefined | eui-b827ebfffef74e1a | 749397731 | 2 | -78 | 8 | undefined | undefined | undefined
test_04_02_19 | pycomarduino | 0058924AB98D5AD4 | 1 | 83 | WzRdIEQyMC8wNS8xOCB0MTI6MDAgVzAwMDAgVDAwMDAgPyAxICAgAA== | [4] D20/05/18 t12:00 W0000 T0000 ? 1 | 2020-06-16T21:36:08.034187581Z | 868,1 | LORA | SF7BW125 | 4/5 | undefined | eui-fcc23dfffe0b696a | 1715351019 | 0 | -116 | -1,5 | undefined | undefined | undefined | eui-b827ebfffef74e1a | 805808539 | 0 | -84 | 10,5 | undefined | undefined | undefined
test_04_02_19 | pycomarduino | 0058924AB98D5AD4 | 1 | 84 | WzVdIEQyMC8wNS8xOCB0MTI6MDAgVzAwMDAgVDAwMDAgPyAxICAgAA== | [5] D20/05/18 t12:00 W0000 T0000 ? 1 | 2020-06-16T21:37:21.816195152Z | 867,3 | LORA | SF7BW125 | 4/5 | undefined | eui-fcc23dfffe0b696a | 1789135283 | 4 | -116 | -2,2 | undefined | undefined | undefined | eui-b827ebfffef74e1a | 879592835 | 4 | -84 | 9,8 | undefined | undefined | undefined
test_04_02_19 | pycomarduino | 0058924AB98D5AD4 | 1 | 85 | WzJdIEQyMC8wNS8xOCB0MTI6MDAgVzAwMDAgVDAwMDAgPyAxICAgAA== | [2] D20/05/18 t12:00 W0000 T0000 ? 1 | 2020-06-16T21:54:06.742663415Z | 868,3 | LORA | SF7BW125 | 4/5 | undefined | eui-b827ebfffef74e1a | 1884518827 | 1 | -79 | 9,5 | undefined | undefined | undefined
test_04_02_19 | pycomarduino | 0058924AB98D5AD4 | 1 | 86 | WzNdIEQyMC8wNS8xOCB0MTI6MDAgVzAwMDAgVDAwMDAgPyAxICAgAA== | [3] D20/05/18 t12:00 W0000 T0000 ? 1 | 2020-06-16T21:55:11.621438455Z | 867,5 | LORA | SF7BW125 | 4/5 | undefined | eui-fcc23dfffe0b696a | 2858937636 | 5 | -115 | -3 | undefined | undefined | undefined | eui-b827ebfffef74e1a | 1949395692 | 5 | -84 | 8 | undefined | undefined | undefined
test_04_02_19 | pycomarduino | 0058924AB98D5AD4 | 1 | 87 | WzRdIEQyMC8wNS8xOCB0MTI6MDAgVzAwMDAgVDAwMDAgPyAxICAgAA== | [4] D20/05/18 t12:00 W0000 T0000 ? 1 | 2020-06-16T21:56:08.032192457Z | 868,5 | LORA | SF7BW125 | 4/5 | undefined | eui-fcc23dfffe0b696a | 2915351219 | 2 | -113 | -0,5 | undefined | undefined | undefined | eui-b827ebfffef74e1a | 2005809307 | 2 | -79 | 7,5 | undefined | undefined | undefined
test_04_02_19 | pycomarduino | 0058924AB98D5AD4 | 1 | 88 | WzVdIEQyMC8wNS8xOCB0MTI6MDAgVzAwMDAgVDAwMDAgPyAxICAgAA== | [5] D20/05/18 t12:00 W0000 T0000 ? 1 | 2020-06-16T21:57:21.816546013Z | 868,1 | LORA | SF7BW125 | 4/5 | undefined | eui-fcc23dfffe0b696a | 2989136715 | 0 | -117 | -1,8 | undefined | undefined | undefined | eui-b827ebfffef74e1a | 2079594835 | 0 | -83 | 10,5 | undefined | undefined | undefined
test_04_02_19 | pycomarduino | 0058924AB98D5AD4 | 1 | 89 | WzJdIEQyMC8wNS8xOCB0MTI6MDAgVzAwMDAgVDAwMDAgPyAxICAgAA== | [2] D20/05/18 t12:00 W0000 T0000 ? 1 | 2020-06-16T22:14:06.74109892Z | 867,7 | LORA | SF7BW125 | 4/5 | undefined | eui-fcc23dfffe0b696a | 3994062500 | 6 | -115 | -4 | undefined | undefined | undefined | eui-b827ebfffef74e1a | 3084521092 | 6 | -81 | 10,2 | undefined | undefined | undefined
test_04_02_19 | pycomarduino | 0058924AB98D5AD4 | 1 | 90 | WzNdIEQyMC8wNS8xOCB0MTI6MDAgVzAwMDAgVDAwMDAgPyAxICAgAA== | [3] D20/05/18 t12:00 W0000 T0000 ? 1 | 2020-06-16T22:15:11.625047325Z | 868,3 | LORA | SF7BW125 | 4/5 | undefined | eui-b827ebfffef74e1a | 3149391603 | 1 | -81 | 9,5 | undefined | undefined | undefined
test_04_02_19 | pycomarduino | 0058924AB98D5AD4 | 1 | 91 | WzRdIEQyMC8wNS8xOCB0MTI6MDAgVzAwMDAgVDAwMDAgPyAxICAgAA== | [4] D20/05/18 t12:00 W0000 T0000 ? 1 | 2020-06-16T22:16:08.033577439Z | 868,5 | LORA | SF7BW125 | 4/5 | undefined | eui-fcc23dfffe0b696a | 4115349283 | 2 | -113 | -0,2 | undefined | undefined | undefined | eui-b827ebfffef74e1a | 3205807931 | 2 | -81 | 7,2 | undefined | undefined | undefined
test_04_02_19 | pycomarduino | 0058924AB98D5AD4 | 1 | 92 | WzVdIEQyMC8wNS8xOCB0MTI6MDAgVzAwMDAgVDAwMDAgPyAxICAgAA== | [5] D20/05/18 t12:00 W0000 T0000 ? 1 | 2020-06-16T22:17:21.827616506Z | 867,9 | LORA | SF7BW125 | 4/5 | undefined | eui-fcc23dfffe0b696a | 4189136076 | 7 | -116 | -0,5 | undefined | undefined | undefined | eui-b827ebfffef74e1a | 3279594764 | 7 | -83 | 10 | undefined | undefined | undefined
test_04_02_19 | pycomarduino | 0058924AB98D5AD4 | 1 | 93 | WzJdIEQyMC8wNS8xOCB0MTI6MDAgVzAwMDAgVDAwMDAgPyAxICAgAA== | [2] D20/05/18 t12:00 W0000 T0000 ? 1 | 2020-06-16T22:34:06.748323538Z | 868,1 | LORA | SF7BW125 | 4/5 | undefined | eui-fcc23dfffe0b696a | 899098883 | 0 | -116 | 0 | undefined | undefined | undefined | eui-b827ebfffef74e1a | 4284525331 | 0 | -84 | 9,8 | undefined | undefined | undefined
test_04_02_19 | pycomarduino | 0058924AB98D5AD4 | 1 | 94 | WzNdIEQyMC8wNS8xOCB0MTI6MDAgVzAwMDAgVDAwMDAgPyAxICAgAA== | [3] D20/05/18 t12:00 W0000 T0000 ? 1 | 2020-06-16T22:35:11.616285255Z | 867,1 | LORA | SF7BW125 | 4/5 | undefined | eui-fcc23dfffe0b696a | 963963035 | 3 | -115 | -0,5 | undefined | undefined | undefined | eui-b827ebfffef74e1a | 54422219 | 3 | -88 | 9 | undefined | undefined | undefined
test_04_02_19 | pycomarduino | 0058924AB98D5AD4 | 1 | 95 | WzRdIEQyMC8wNS8xOCB0MTI6MDAgVzAwMDAgVDAwMDAgPyAxICAgAA== | [4] D20/05/18 t12:00 W0000 T0000 ? 1 | 2020-06-16T22:36:08.031181326Z | 868,3 | LORA | SF7BW125 | 4/5 | undefined | eui-fcc23dfffe0b696a | 1020382123 | 1 | -112 | -6 | undefined | undefined | undefined | eui-b827ebfffef74e1a | 110841339 | 1 | -81 | 9,5 | undefined | undefined | undefined
test_04_02_19 | pycomarduino | 0058924AB98D5AD4 | 1 | 96 | WzVdIEQyMC8wNS8xOCB0MTI6MDAgVzAwMDAgVDAwMDAgPyAxICAgAA== | [5] D20/05/18 t12:00 W0000 T0000 ? 1 | 2020-06-16T22:37:21.817230969Z | 868,5 | LORA | SF7BW125 | 4/5 | undefined | eui-fcc23dfffe0b696a | 1094170195 | 2 | -113 | -2 | undefined | undefined | undefined | eui-b827ebfffef74e1a | 184629443 | 2 | -79 | 7,2 | undefined | undefined | undefined
test_04_02_19 | pycomarduino | 0058924AB98D5AD4 | 1 | 97 | WzJdIEQyMC8wNS8xOCB0MTI6MDAgVzAwMDAgVDAwMDAgPyAxICAgAA== | [2] D20/05/18 t12:00 W0000 T0000 ? 1 | 2020-06-16T22:54:06.756546206Z | 867,3 | LORA | SF7BW125 | 4/5 | undefined | eui-fcc23dfffe0b696a | 2099100531 | 4 | -112 | -0,8 | undefined | undefined | undefined | eui-b827ebfffef74e1a | 1189560251 | 4 | -84 | 9 | undefined | undefined | undefined
test_04_02_19 | pycomarduino | 0058924AB98D5AD4 | 1 | 98 | WzNdIEQyMC8wNS8xOCB0MTI6MDAgVzAwMDAgVDAwMDAgPyAxICAgAA== | [3] D20/05/18 t12:00 W0000 T0000 ? 1 | 2020-06-16T22:55:11.608860329Z | 868,1 | LORA | SF7BW125 | 4/5 | undefined | eui-fcc23dfffe0b696a | 2163958371 | 0 | -116 | -6,2 | undefined | undefined | undefined | eui-b827ebfffef74e1a | 1254418115 | 0 | -81 | 9,5 | undefined | undefined | undefined
test_04_02_19 | pycomarduino | 0058924AB98D5AD4 | 1 | 99 | WzRdIEQyMC8wNS8xOCB0MTI6MDAgVzAwMDAgVDAwMDAgPyAxICAgAA== | [4] D20/05/18 t12:00 W0000 T0000 ? 1 | 2020-06-16T22:56:08.034853209Z | 868,3 | LORA | SF7BW125 | 4/5 | undefined | eui-b827ebfffef74e1a | 1310839883 | 1 | -81 | 9,8 | undefined | undefined | undefined
test_04_02_19 | pycomarduino | 0058924AB98D5AD4 | 1 | 100 | WzVdIEQyMC8wNS8xOCB0MTI6MDAgVzAwMDAgVDAwMDAgPyAxICAgAA== | [5] D20/05/18 t12:00 W0000 T0000 ? 1 | 2020-06-16T22:57:21.817975693Z | 867,5 | LORA | SF7BW125 | 4/5 | undefined | eui-fcc23dfffe0b696a | 2294169556 | 5 | -114 | -4 | undefined | undefined | undefined | eui-b827ebfffef74e1a | 1384629356 | 5 | -85 | 7,2 | undefined | undefined | undefined
test_04_02_19 | pycomarduino | 0058924AB98D5AD4 | 1 | 101 | WzJdIEQyMC8wNS8xOCB0MTI6MDAgVzAwMDAgVDAwMDAgPyAxICAgAA== | [2] D20/05/18 t12:00 W0000 T0000 ? 1 | 2020-06-16T23:14:06.752865781Z | 868,5 | LORA | SF7BW125 | 4/5 | undefined | eui-fcc23dfffe0b696a | 3299104171 | 2 | -111 | -8,2 | undefined | undefined | undefined | eui-b827ebfffef74e1a | 2389564435 | 2 | -81 | 7,5 | undefined | undefined | undefined
test_04_02_19 | pycomarduino | 0058924AB98D5AD4 | 1 | 102 | WzNdIEQyMC8wNS8xOCB0MTI6MDAgVzAwMDAgVDAwMDAgPyAxICAgAA== | [3] D20/05/18 t12:00 W0000 T0000 ? 1 | 2020-06-16T23:15:11.611315751Z | 867,7 | LORA | SF7BW125 | 4/5 | undefined | eui-b827ebfffef74e1a | 2454415972 | 6 | -84 | 10 | undefined | undefined | undefined
test_04_02_19 | pycomarduino | 0058924AB98D5AD4 | 1 | 103 | WzRdIEQyMC8wNS8xOCB0MTI6MDAgVzAwMDAgVDAwMDAgPyAxICAgAA== | [4] D20/05/18 t12:00 W0000 T0000 ? 1 | 2020-06-16T23:16:08.034663327Z | 868,1 | LORA | SF7BW125 | 4/5 | undefined | eui-b827ebfffef74e1a | 2510840659 | 0 | -81 | 9,2 | undefined | undefined | undefined
test_04_02_19 | pycomarduino | 0058924AB98D5AD4 | 1 | 104 | WzVdIEQyMC8wNS8xOCB0MTI6MDAgVzAwMDAgVDAwMDAgPyAxICAgAA== | [5] D20/05/18 t12:00 W0000 T0000 ? 1 | 2020-06-16T23:17:22.066135398Z | 868,3 | LORA | SF7BW125 | 4/5 | undefined | eui-b827ebfffef74e1a | 2584631267 | 1 | -81 | 11 | undefined | undefined | undefined
test_04_02_19 | pycomarduino | 0058924AB98D5AD4 | 1 | 105 | WzJdIEQyMC8wNS8xOCB0MTI6MDAgVzAwMDAgVDAwMDAgPyAxICAgAA== | [2] D20/05/18 t12:00 W0000 T0000 ? 1 | 2020-06-16T23:34:06.754952448Z | 867,9 | LORA | SF7BW125 | 4/5 | undefined | eui-fcc23dfffe0b696a | 204138460 | 7 | -115 | 0,2 | undefined | undefined | undefined | eui-b827ebfffef74e1a | 3589566580 | 7 | -83 | 9,2 | undefined | undefined | undefined
test_04_02_19 | pycomarduino | 0058924AB98D5AD4 | 1 | 107 | WzRdIEQyMC8wNS8xOCB0MTI6MDAgVzAwMDAgVDAwMDAgPyAxICAgAA== | [4] D20/05/18 t12:00 W0000 T0000 ? 1 | 2020-06-16T23:36:08.036959535Z | 868,1 | LORA | SF7BW125 | 4/5 | undefined | eui-fcc23dfffe0b696a | 325411035 | 0 | -116 | -3,5 | undefined | undefined | undefined | eui-b827ebfffef74e1a | 3710839211 | 0 | -84 | 10,2 | undefined | undefined | undefined
test_04_02_19 | pycomarduino | 0058924AB98D5AD4 | 1 | 108 | WzVdIEQyMC8wNS8xOCB0MTI6MDAgVzAwMDAgVDAwMDAgPyAxICAgAA== | [5] D20/05/18 t12:00 W0000 T0000 ? 1 | 2020-06-16T23:37:21.815969636Z | 867,1 | LORA | SF7BW125 | 4/5 | undefined | eui-fcc23dfffe0a9698 | 401260027 | 3 | -115 | -9 | undefined | undefined | undefined | eui-fcc23dfffe0b696a | 399202891 | 3 | -114 | 0,2 | undefined | undefined | undefined | eui-b827ebfffef74e1a | 3784631099 | 3 | -90 | 10,2 | undefined | undefined | undefined
test_04_02_19 | pycomarduino | 0058924AB98D5AD4 | 1 | 109 | WzJdIEQyMC8wNS8xOCB0MTI6MDAgVzAwMDAgVDAwMDAgPyAxICAgAA== | [2] D20/05/18 t12:00 W0000 T0000 ? 1 | 2020-06-16T23:54:06.781352918Z | 868,3 | LORA | SF7BW125 | 4/5 | undefined | eui-fcc23dfffe0b696a | 1404142107 | 1 | -115 | -3,2 | undefined | undefined | undefined | eui-b827ebfffef74e1a | 494603483 | 1 | -83 | 10,5 | undefined | undefined | undefined
test_04_02_19 | pycomarduino | 0058924AB98D5AD4 | 1 | 110 | WzNdIEQyMC8wNS8xOCB0MTI6MDAgVzAwMDAgVDAwMDAgPyAxICAgAA== | [3] D20/05/18 t12:00 W0000 T0000 ? 1 | 2020-06-16T23:55:11.604012085Z | 867,3 | LORA | SF7BW125 | 4/5 | undefined | eui-fcc23dfffe0b696a | 1468980907 | 4 | -112 | -0,5 | undefined | undefined | undefined | eui-b827ebfffef74e1a | 559442315 | 4 | -87 | 10,2 | undefined | undefined | undefined
test_04_02_19 | pycomarduino | 0058924AB98D5AD4 | 1 | 111 | WzRdIEQyMC8wNS8xOCB0MTI6MDAgVzAwMDAgVDAwMDAgPyAxICAgAA== | [4] D20/05/18 t12:00 W0000 T0000 ? 1 | 2020-06-16T23:56:08.138328219Z | 868,5 | LORA | SF7BW125 | 4/5 | undefined | eui-fcc23dfffe0b696a | 1525411147 | 2 | -111 | 1 | undefined | undefined | undefined | eui-b827ebfffef74e1a | 615872579 | 2 | -79 | 8 | undefined | undefined | undefined
test_04_02_19 | pycomarduino | 0058924AB98D5AD4 | 1 | 112 | WzVdIEQyMC8wNS8xOCB0MTI6MDAgVzAwMDAgVDAwMDAgPyAxICAgAA== | [5] D20/05/18 t12:00 W0000 T0000 ? 1 | 2020-06-16T23:57:21.832711354Z | 868,1 | LORA | SF7BW125 | 4/5 | undefined | eui-fcc23dfffe0b696a | 1599204235 | 0 | -116 | -1,5 | undefined | undefined | undefined | eui-b827ebfffef74e1a | 689665707 | 0 | -81 | 9,2 | undefined | undefined | undefined
test_04_02_19 | pycomarduino | 0058924AB98D5AD4 | 1 | 113 | WzJdIEQyMC8wNS8xOCB0MTI6MDAgVzAwMDAgVDAwMDAgPyAxICAgAA== | [2] D20/05/18 t12:00 W0000 T0000 ? 1 | 2020-06-17T00:14:06.775603923Z | 867,5 | LORA | SF7BW125 | 4/5 | undefined | eui-fcc23dfffe0b696a | 2604143700 | 5 | -113 | -5 | undefined | undefined | undefined | eui-b827ebfffef74e1a | 1694605628 | 5 | -83 | 7,8 | undefined | undefined | undefined
test_04_02_19 | pycomarduino | 0058924AB98D5AD4 | 1 | 114 | WzNdIEQyMC8wNS8xOCB0MTI6MDAgVzAwMDAgVDAwMDAgPyAxICAgAA== | [3] D20/05/18 t12:00 W0000 T0000 ? 1 | 2020-06-17T00:15:12.057655506Z | 868,3 | LORA | SF7BW125 | 4/5 | undefined | eui-b827ebfffef74e1a | 1759437995 | 1 | -79 | 9,2 | undefined | undefined | undefined
test_04_02_19 | pycomarduino | 0058924AB98D5AD4 | 1 | 115 | WzRdIEQyMC8wNS8xOCB0MTI6MDAgVzAwMDAgVDAwMDAgPyAxICAgAA== | [4] D20/05/18 t12:00 W0000 T0000 ? 1 | 2020-06-17T00:16:08.023360723Z | 868,5 | LORA | SF7BW125 | 4/5 | undefined | eui-fcc23dfffe0b696a | 2725409155 | 2 | -112 | -0,2 | undefined | undefined | undefined | eui-b827ebfffef74e1a | 1815871131 | 2 | -81 | 7 | undefined | undefined | undefined
test_04_02_19 | pycomarduino | 0058924AB98D5AD4 | 1 | 116 | WzVdIEQyMC8wNS8xOCB0MTI6MDAgVzAwMDAgVDAwMDAgPyAxICAgAA== | [5] D20/05/18 t12:00 W0000 T0000 ? 1 | 2020-06-17T00:17:21.819436854Z | 867,7 | LORA | SF7BW125 | 4/5 | undefined | eui-fcc23dfffe0b696a | 2799203524 | 6 | -115 | -5,5 | undefined | undefined | undefined | eui-b827ebfffef74e1a | 1889665532 | 6 | -84 | 9 | undefined | undefined | undefined
test_04_02_19 | pycomarduino | 0058924AB98D5AD4 | 1 | 117 | WzJdIEQyMC8wNS8xOCB0MTI6MDAgVzAwMDAgVDAwMDAgPyAxICAgAA== | [2] D20/05/18 t12:00 W0000 T0000 ? 1 | 2020-06-17T00:34:06.764558831Z | 868,1 | LORA | SF7BW125 | 4/5 | undefined | eui-b827ebfffef74e1a | 2894609795 | 0 | -82 | 8,8 | undefined | undefined | undefined
test_04_02_19 | pycomarduino | 0058924AB98D5AD4 | 1 | 118 | WzNdIEQyMC8wNS8xOCB0MTI6MDAgVzAwMDAgVDAwMDAgPyAxICAgAA== | [3] D20/05/18 t12:00 W0000 T0000 ? 1 | 2020-06-17T00:35:11.589543509Z | 867,9 | LORA | SF7BW125 | 4/5 | undefined | eui-fcc23dfffe0b696a | 3868973276 | 7 | -116 | -2 | undefined | undefined | undefined | eui-b827ebfffef74e1a | 2959435772 | 7 | -85 | 10,8 | undefined | undefined | undefined
test_04_02_19 | pycomarduino | 0058924AB98D5AD4 | 1 | 119 | WzRdIEQyMC8wNS8xOCB0MTI6MDAgVzAwMDAgVDAwMDAgPyAxICAgAA== | [4] D20/05/18 t12:00 W0000 T0000 ? 1 | 2020-06-17T00:36:08.032409821Z | 868,3 | LORA | SF7BW125 | 4/5 | undefined | eui-b827ebfffef74e1a | 3015871611 | 1 | -83 | 10,5 | undefined | undefined | undefined
test_04_02_19 | pycomarduino | 0058924AB98D5AD4 | 1 | 120 | WzVdIEQyMC8wNS8xOCB0MTI6MDAgVzAwMDAgVDAwMDAgPyAxICAgAA== | [5] D20/05/18 t12:00 W0000 T0000 ? 1 | 2020-06-17T00:37:21.822032184Z | 868,5 | LORA | SF7BW125 | 4/5 | undefined | eui-fcc23dfffe0b696a | 3999204803 | 2 | -111 | 1 | undefined | undefined | undefined | eui-b827ebfffef74e1a | 3089667355 | 2 | -78 | 8 | undefined | undefined | undefined
test_04_02_19 | pycomarduino | 0058924AB98D5AD4 | 1 | 121 | WzJdIEQyMC8wNS8xOCB0MTI6MDAgVzAwMDAgVDAwMDAgPyAxICAgAA== | [2] D20/05/18 t12:00 W0000 T0000 ? 1 | 2020-06-17T00:54:06.764437978Z | 867,1 | LORA | SF7BW125 | 4/5 | undefined | eui-fcc23dfffe0b696a | 709181579 | 3 | -115 | -1,8 | undefined | undefined | undefined | eui-b827ebfffef74e1a | 4094611883 | 3 | -86 | 8,8 | undefined | undefined | undefined
test_04_02_19 | pycomarduino | 0058924AB98D5AD4 | 1 | 122 | WzNdIEQyMC8wNS8xOCB0MTI6MDAgVzAwMDAgVDAwMDAgPyAxICAgAA== | [3] D20/05/18 t12:00 W0000 T0000 ? 1 | 2020-06-17T00:55:11.588919606Z | 868,1 | LORA | SF7BW125 | 4/5 | undefined | eui-b827ebfffef74e1a | 4159431523 | 0 | -83 | 11 | undefined | undefined | undefined
test_04_02_19 | pycomarduino | 0058924AB98D5AD4 | 1 | 123 | WzRdIEQyMC8wNS8xOCB0MTI6MDAgVzAwMDAgVDAwMDAgPyAxICAgAA== | [4] D20/05/18 t12:00 W0000 T0000 ? 1 | 2020-06-17T00:56:08.027231162Z | 868,3 | LORA | SF7BW125 | 4/5 | undefined | eui-fcc23dfffe0b696a | 830439843 | 1 | -110 | -3,8 | undefined | undefined | undefined | eui-b827ebfffef74e1a | 4215870203 | 1 | -79 | 9,8 | undefined | undefined | undefined
test_04_02_19 | pycomarduino | 0058924AB98D5AD4 | 1 | 124 | WzVdIEQyMC8wNS8xOCB0MTI6MDAgVzAwMDAgVDAwMDAgPyAxICAgAA== | [5] D20/05/18 t12:00 W0000 T0000 ? 1 | 2020-06-17T00:57:21.825706736Z | 867,3 | LORA | SF7BW125 | 4/5 | undefined | eui-fcc23dfffe0b696a | 904236675 | 4 | -116 | -1,5 | undefined | undefined | undefined | eui-b827ebfffef74e1a | 4289667067 | 4 | -87 | 9,5 | undefined | undefined | undefined
test_04_02_19 | pycomarduino | 0058924AB98D5AD4 | 1 | 125 | WzJdIEQyMC8wNS8xOCB0MTI6MDAgVzAwMDAgVDAwMDAgPyAxICAgAA== | [2] D20/05/18 t12:00 W0000 T0000 ? 1 | 2020-06-17T01:14:06.774745644Z | 868,5 | LORA | SF7BW125 | 4/5 | undefined | eui-fcc23dfffe0b696a | 1909185219 | 2 | -113 | 1 | undefined | undefined | undefined | eui-b827ebfffef74e1a | 999648771 | 2 | -81 | 7,5 | undefined | undefined | undefined
test_04_02_19 | pycomarduino | 0058924AB98D5AD4 | 1 | 126 | WzNdIEQyMC8wNS8xOCB0MTI6MDAgVzAwMDAgVDAwMDAgPyAxICAgAA== | [3] D20/05/18 t12:00 W0000 T0000 ? 1 | 2020-06-17T01:15:11.651911702Z | 867,5 | LORA | SF7BW125 | 4/5 | undefined | eui-fcc23dfffe0b696a | 1973998340 | 5 | -113 | -4,5 | undefined | undefined | undefined | eui-b827ebfffef74e1a | 1064461916 | 5 | -84 | 7,8 | undefined | undefined | undefined
test_04_02_19 | pycomarduino | 0058924AB98D5AD4 | 1 | 127 | WzRdIEQyMC8wNS8xOCB0MTI6MDAgVzAwMDAgVDAwMDAgPyAxICAgAA== | [4] D20/05/18 t12:00 W0000 T0000 ? 1 | 2020-06-17T01:16:08.027306645Z | 868,1 | LORA | SF7BW125 | 4/5 | undefined | eui-fcc23dfffe0b696a | 2030439779 | 0 | -115 | -2 | undefined | undefined | undefined | eui-b827ebfffef74e1a | 1120903379 | 0 | -81 | 9,5 | undefined | undefined | undefined
test_04_02_19 | pycomarduino | 0058924AB98D5AD4 | 1 | 128 | WzVdIEQyMC8wNS8xOCB0MTI6MDAgVzAwMDAgVDAwMDAgPyAxICAgAA== | [5] D20/05/18 t12:00 W0000 T0000 ? 1 | 2020-06-17T01:17:21.828865326Z | 868,3 | LORA | SF7BW125 | 4/5 | undefined | eui-b827ebfffef74e1a | 1194701619 | 1 | -81 | 9,2 | undefined | undefined | undefined
test_04_02_19 | pycomarduino | 0058924AB98D5AD4 | 1 | 129 | WzJdIEQyMC8wNS8xOCB0MTI6MDAgVzAwMDAgVDAwMDAgPyAxICAgAA== | [2] D20/05/18 t12:00 W0000 T0000 ? 1 | 2020-06-17T01:34:06.774873292Z | 867,7 | LORA | SF7BW125 | 4/5 | undefined | eui-fcc23dfffe0b696a | 3109186764 | 6 | -117 | -6,5 | undefined | undefined | undefined | eui-b827ebfffef74e1a | 2199650860 | 6 | -82 | 9,8 | undefined | undefined | undefined
test_04_02_19 | pycomarduino | 0058924AB98D5AD4 | 1 | 130 | WzNdIEQyMC8wNS8xOCB0MTI6MDAgVzAwMDAgVDAwMDAgPyAxICAgAA== | [3] D20/05/18 t12:00 W0000 T0000 ? 1 | 2020-06-17T01:35:11.584802198Z | 868,5 | LORA | SF7BW125 | 4/5 | undefined | eui-b827ebfffef74e1a | 2264457547 | 2 | -79 | 8,2 | undefined | undefined | undefined
test_04_02_19 | pycomarduino | 0058924AB98D5AD4 | 1 | 131 | WzRdIEQyMC8wNS8xOCB0MTI6MDAgVzAwMDAgVDAwMDAgPyAxICAgAA== | [4] D20/05/18 t12:00 W0000 T0000 ? 1 | 2020-06-17T01:36:08.025936881Z | 868,1 | LORA | SF7BW125 | 4/5 | undefined | eui-fcc23dfffe0b696a | 3230437763 | 0 | -117 | -3,8 | undefined | undefined | undefined | eui-b827ebfffef74e1a | 2320901907 | 0 | -81 | 7,8 | undefined | undefined | undefined
test_04_02_19 | pycomarduino | 0058924AB98D5AD4 | 1 | 132 | WzVdIEQyMC8wNS8xOCB0MTI6MDAgVzAwMDAgVDAwMDAgPyAxICAgAA== | [5] D20/05/18 t12:00 W0000 T0000 ? 1 | 2020-06-17T01:37:21.828050365Z | 867,9 | LORA | SF7BW125 | 4/5 | undefined | eui-fcc23dfffe0b696a | 3304237164 | 7 | -116 | -1 | undefined | undefined | undefined | eui-b827ebfffef74e1a | 2394701348 | 7 | -85 | 9,2 | undefined | undefined | undefined
test_04_02_19 | pycomarduino | 0058924AB98D5AD4 | 1 | 133 | WzJdIEQyMC8wNS8xOCB0MTI6MDAgVzAwMDAgVDAwMDAgPyAxICAgAA== | [2] D20/05/18 t12:00 W0000 T0000 ? 1 | 2020-06-17T01:54:06.777864239Z | 868,3 | LORA | SF7BW125 | 4/5 | undefined | eui-fcc23dfffe0b696a | 14222987 | 1 | -113 | -8,2 | undefined | undefined | undefined | eui-b827ebfffef74e1a | 3399654915 | 1 | -79 | 9 | undefined | undefined | undefined
test_04_02_19 | pycomarduino | 0058924AB98D5AD4 | 1 | 134 | WzNdIEQyMC8wNS8xOCB0MTI6MDAgVzAwMDAgVDAwMDAgPyAxICAgAA== | [3] D20/05/18 t12:00 W0000 T0000 ? 1 | 2020-06-17T01:55:11.575439925Z | 867,1 | LORA | SF7BW125 | 4/5 | undefined | eui-fcc23dfffe0b696a | 79023315 | 3 | -117 | -3,8 | undefined | undefined | undefined | eui-b827ebfffef74e1a | 3464455275 | 3 | -87 | 10,2 | undefined | undefined | undefined
test_04_02_19 | pycomarduino | 0058924AB98D5AD4 | 1 | 135 | WzRdIEQyMC8wNS8xOCB0MTI6MDAgVzAwMDAgVDAwMDAgPyAxICAgAA== | [4] D20/05/18 t12:00 W0000 T0000 ? 1 | 2020-06-17T01:56:08.028893771Z | 868,5 | LORA | SF7BW125 | 4/5 | undefined | eui-fcc23dfffe0b696a | 135470435 | 2 | -111 | -0,8 | undefined | undefined | undefined | eui-b827ebfffef74e1a | 3520902411 | 2 | -81 | 7,5 | undefined | undefined | undefined
test_04_02_19 | pycomarduino | 0058924AB98D5AD4 | 1 | 136 | WzVdIEQyMC8wNS8xOCB0MTI6MDAgVzAwMDAgVDAwMDAgPyAxICAgAA== | [5] D20/05/18 t12:00 W0000 T0000 ? 1 | 2020-06-17T01:57:21.832646716Z | 868,1 | LORA | SF7BW125 | 4/5 | undefined | eui-b827ebfffef74e1a | 3594703107 | 0 | -83 | 9,8 | undefined | undefined | undefined
test_04_02_19 | pycomarduino | 0058924AB98D5AD4 | 1 | 137 | WzJdIEQyMC8wNS8xOCB0MTI6MDAgVzAwMDAgVDAwMDAgPyAxICAgAA== | [2] D20/05/18 t12:00 W0000 T0000 ? 1 | 2020-06-17T02:14:06.779817366Z | 867,3 | LORA | SF7BW125 | 4/5 | undefined | eui-fcc23dfffe0b696a | 1214224563 | 4 | -112 | -4,2 | undefined | undefined | undefined | eui-b827ebfffef74e1a | 304689723 | 4 | -87 | 11 | undefined | undefined | undefined
test_04_02_19 | pycomarduino | 0058924AB98D5AD4 | 1 | 138 | WzNdIEQyMC8wNS8xOCB0MTI6MDAgVzAwMDAgVDAwMDAgPyAxICAgAA== | [3] D20/05/18 t12:00 W0000 T0000 ? 1 | 2020-06-17T02:15:11.581599788Z | 868,3 | LORA | SF7BW125 | 4/5 | undefined | eui-b827ebfffef74e1a | 369483571 | 1 | -79 | 9,5 | undefined | undefined | undefined
test_04_02_19 | pycomarduino | 0058924AB98D5AD4 | 1 | 139 | WzRdIEQyMC8wNS8xOCB0MTI6MDAgVzAwMDAgVDAwMDAgPyAxICAgAA== | [4] D20/05/18 t12:00 W0000 T0000 ? 1 | 2020-06-17T02:16:08.028785388Z | 868,5 | LORA | SF7BW125 | 4/5 | undefined | eui-fcc23dfffe0b696a | 1335468371 | 2 | -111 | -3 | undefined | undefined | undefined | eui-b827ebfffef74e1a | 425933579 | 2 | -79 | 8 | undefined | undefined | undefined
test_04_02_19 | pycomarduino | 0058924AB98D5AD4 | 1 | 140 | WzVdIEQyMC8wNS8xOCB0MTI6MDAgVzAwMDAgVDAwMDAgPyAxICAgAA== | [5] D20/05/18 t12:00 W0000 T0000 ? 1 | 2020-06-17T02:17:21.827863874Z | 867,5 | LORA | SF7BW125 | 4/5 | undefined | eui-fcc23dfffe0b696a | 1409270300 | 5 | -111 | -6,8 | undefined | undefined | undefined | eui-b827ebfffef74e1a | 499735540 | 5 | -84 | 7,5 | undefined | undefined | undefined
test_04_02_19 | pycomarduino | 0058924AB98D5AD4 | 1 | 141 | WzJdIEQyMC8wNS8xOCB0MTI6MDAgVzAwMDAgVDAwMDAgPyAxICAgAA== | [2] D20/05/18 t12:00 W0000 T0000 ? 1 | 2020-06-17T02:34:06.781686439Z | 868,1 | LORA | SF7BW125 | 4/5 | undefined | eui-fcc23dfffe0b696a | 2414228307 | 0 | -113 | -5,8 | undefined | undefined | undefined | eui-b827ebfffef74e1a | 1504693987 | 0 | -83 | 9,5 | undefined | undefined | undefined
test_04_02_19 | pycomarduino | 0058924AB98D5AD4 | 1 | 142 | WzNdIEQyMC8wNS8xOCB0MTI6MDAgVzAwMDAgVDAwMDAgPyAxICAgAA== | [3] D20/05/18 t12:00 W0000 T0000 ? 1 | 2020-06-17T02:35:12.153085933Z | 867,7 | LORA | SF7BW125 | 4/5 | undefined | eui-b827ebfffef74e1a | 1569481260 | 6 | -85 | 9,5 | undefined | undefined | undefined
test_04_02_19 | pycomarduino | 0058924AB98D5AD4 | 1 | 143 | WzRdIEQyMC8wNS8xOCB0MTI6MDAgVzAwMDAgVDAwMDAgPyAxICAgAA== | [4] D20/05/18 t12:00 W0000 T0000 ? 1 | 2020-06-17T02:36:08.019980207Z | 868,3 | LORA | SF7BW125 | 4/5 | undefined | eui-b827ebfffef74e1a | 1625934411 | 1 | -83 | 9,8 | undefined | undefined | undefined
test_04_02_19 | pycomarduino | 0058924AB98D5AD4 | 1 | 144 | WzVdIEQyMC8wNS8xOCB0MTI6MDAgVzAwMDAgVDAwMDAgPyAxICAgAA== | [5] D20/05/18 t12:00 W0000 T0000 ? 1 | 2020-06-17T02:37:21.831745106Z | 868,5 | LORA | SF7BW125 | 4/5 | undefined | eui-b827ebfffef74e1a | 1699737435 | 2 | -81 | 7,8 | undefined | undefined | undefined
test_04_02_19 | pycomarduino | 0058924AB98D5AD4 | 1 | 145 | WzJdIEQyMC8wNS8xOCB0MTI6MDAgVzAwMDAgVDAwMDAgPyAxICAgAA== | [2] D20/05/18 t12:00 W0000 T0000 ? 1 | 2020-06-17T02:54:06.787883607Z | 867,9 | LORA | SF7BW125 | 4/5 | undefined | eui-fcc23dfffe0b696a | 3614229788 | 7 | -113 | -1,2 | undefined | undefined | undefined | eui-b827ebfffef74e1a | 2704696004 | 7 | -84 | 10,5 | undefined | undefined | undefined
test_04_02_19 | pycomarduino | 0058924AB98D5AD4 | 1 | 146 | WzNdIEQyMC8wNS8xOCB0MTI6MDAgVzAwMDAgVDAwMDAgPyAxICAgAA== | [3] D20/05/18 t12:00 W0000 T0000 ? 1 | 2020-06-17T02:55:11.570917717Z | 868,1 | LORA | SF7BW125 | 4/5 | undefined | eui-b827ebfffef74e1a | 2769476827 | 0 | -81 | 9,2 | undefined | undefined | undefined
test_04_02_19 | pycomarduino | 0058924AB98D5AD4 | 1 | 147 | WzRdIEQyMC8wNS8xOCB0MTI6MDAgVzAwMDAgVDAwMDAgPyAxICAgAA== | [4] D20/05/18 t12:00 W0000 T0000 ? 1 | 2020-06-17T02:56:08.029859188Z | 868,3 | LORA | SF7BW125 | 4/5 | undefined | eui-b827ebfffef74e1a | 2825932419 | 1 | -81 | 9,2 | undefined | undefined | undefined
test_04_02_19 | pycomarduino | 0058924AB98D5AD4 | 1 | 148 | WzVdIEQyMC8wNS8xOCB0MTI6MDAgVzAwMDAgVDAwMDAgPyAxICAgAA== | [5] D20/05/18 t12:00 W0000 T0000 ? 1 | 2020-06-17T02:57:21.822981151Z | 867,1 | LORA | SF7BW125 | 4/5 | undefined | eui-fcc23dfffe0b696a | 3809270475 | 3 | -113 | -7,2 | undefined | undefined | undefined | eui-b827ebfffef74e1a | 2899736771 | 3 | -87 | 9,8 | undefined | undefined | undefined
test_04_02_19 | pycomarduino | 0058924AB98D5AD4 | 1 | 149 | WzJdIEQyMC8wNS8xOCB0MTI6MDAgVzAwMDAgVDAwMDAgPyAxICAgAA== | [2] D20/05/18 t12:00 W0000 T0000 ? 1 | 2020-06-17T03:14:06.791507516Z | 868,5 | LORA | SF7BW125 | 4/5 | undefined | eui-fcc23dfffe0b696a | 519265787 | 2 | -112 | -1,5 | undefined | undefined | undefined | eui-b827ebfffef74e1a | 3904699835 | 2 | -78 | 8,2 | undefined | undefined | undefined
test_04_02_19 | pycomarduino | 0058924AB98D5AD4 | 1 | 150 | WzNdIEQyMC8wNS8xOCB0MTI6MDAgVzAwMDAgVDAwMDAgPyAxICAgAA== | [3] D20/05/18 t12:00 W0000 T0000 ? 1 | 2020-06-17T03:15:11.580455104Z | 867,3 | LORA | SF7BW125 | 4/5 | undefined | eui-fcc23dfffe0a9698 | 586094451 | 4 | -115 | -8 | undefined | undefined | undefined | eui-fcc23dfffe0b696a | 584040347 | 4 | -113 | -3 | undefined | undefined | undefined | eui-b827ebfffef74e1a | 3969474419 | 4 | -85 | 9,8 | undefined | undefined | undefined
test_04_02_19 | pycomarduino | 0058924AB98D5AD4 | 1 | 151 | WzRdIEQyMC8wNS8xOCB0MTI6MDAgVzAwMDAgVDAwMDAgPyAxICAgAA== | [4] D20/05/18 t12:00 W0000 T0000 ? 1 | 2020-06-17T03:16:08.017790335Z | 868,1 | LORA | SF7BW125 | 4/5 | undefined | eui-fcc23dfffe0b696a | 640498835 | 0 | -116 | -5,2 | undefined | undefined | undefined | eui-b827ebfffef74e1a | 4025932931 | 0 | -83 | 10 | undefined | undefined | undefined
test_04_02_19 | pycomarduino | 0058924AB98D5AD4 | 1 | 152 | WzVdIEQyMC8wNS8xOCB0MTI6MDAgVzAwMDAgVDAwMDAgPyAxICAgAA== | [5] D20/05/18 t12:00 W0000 T0000 ? 1 | 2020-06-17T03:17:21.824658316Z | 868,3 | LORA | SF7BW125 | 4/5 | undefined | eui-b827ebfffef74e1a | 4099738435 | 1 | -81 | 9,5 | undefined | undefined | undefined
test_04_02_19 | pycomarduino | 0058924AB98D5AD4 | 1 | 153 | WzJdIEQyMC8wNS8xOCB0MTI6MDAgVzAwMDAgVDAwMDAgPyAxICAgAA== | [2] D20/05/18 t12:00 W0000 T0000 ? 1 | 2020-06-17T03:34:06.78972141Z | 867,5 | LORA | SF7BW125 | 4/5 | undefined | eui-fcc23dfffe0b696a | 1719267308 | 5 | -111 | -5 | undefined | undefined | undefined | eui-b827ebfffef74e1a | 809734588 | 5 | -84 | 7,2 | undefined | undefined | undefined
test_04_02_19 | pycomarduino | 0058924AB98D5AD4 | 1 | 154 | WzNdIEQyMC8wNS8xOCB0MTI6MDAgVzAwMDAgVDAwMDAgPyAxICAgAA== | [3] D20/05/18 t12:00 W0000 T0000 ? 1 | 2020-06-17T03:35:11.561953585Z | 868,5 | LORA | SF7BW125 | 4/5 | undefined | eui-fcc23dfffe0b696a | 1784035355 | 2 | -112 | -2,5 | undefined | undefined | undefined | eui-b827ebfffef74e1a | 874502667 | 2 | -78 | 7,5 | undefined | undefined | undefined
test_04_02_19 | pycomarduino | 0058924AB98D5AD4 | 1 | 155 | WzRdIEQyMC8wNS8xOCB0MTI6MDAgVzAwMDAgVDAwMDAgPyAxICAgAA== | [4] D20/05/18 t12:00 W0000 T0000 ? 1 | 2020-06-17T03:36:08.025970418Z | 868,1 | LORA | SF7BW125 | 4/5 | undefined | eui-fcc23dfffe0b696a | 1840496699 | 0 | -116 | -5,2 | undefined | undefined | undefined | eui-b827ebfffef74e1a | 930964035 | 0 | -80 | 9,8 | undefined | undefined | undefined
test_04_02_19 | pycomarduino | 0058924AB98D5AD4 | 1 | 156 | WzVdIEQyMC8wNS8xOCB0MTI6MDAgVzAwMDAgVDAwMDAgPyAxICAgAA== | [5] D20/05/18 t12:00 W0000 T0000 ? 1 | 2020-06-17T03:37:21.827931416Z | 867,7 | LORA | SF7BW125 | 4/5 | undefined | eui-fcc23dfffe0b696a | 1914303404 | 6 | -113 | -6,8 | undefined | undefined | undefined | eui-b827ebfffef74e1a | 1004770764 | 6 | -82 | 9,8 | undefined | undefined | undefined
test_04_02_19 | pycomarduino | 0058924AB98D5AD4 | 1 | 157 | WzJdIEQyMC8wNS8xOCB0MTI6MDAgVzAwMDAgVDAwMDAgPyAxICAgAA== | [2] D20/05/18 t12:00 W0000 T0000 ? 1 | 2020-06-17T03:54:06.798352314Z | 868,3 | LORA | SF7BW125 | 4/5 | undefined | eui-b827ebfffef74e1a | 2009738635 | 1 | -83 | 9,8 | undefined | undefined | undefined
test_04_02_19 | pycomarduino | 0058924AB98D5AD4 | 1 | 158 | WzNdIEQyMC8wNS8xOCB0MTI6MDAgVzAwMDAgVDAwMDAgPyAxICAgAA== | [3] D20/05/18 t12:00 W0000 T0000 ? 1 | 2020-06-17T03:55:11.55629703Z | 867,9 | LORA | SF7BW125 | 4/5 | undefined | eui-fcc23dfffe0b696a | 2984032420 | 7 | -113 | -0,2 | undefined | undefined | undefined | eui-b827ebfffef74e1a | 2074500268 | 7 | -84 | 9 | undefined | undefined | undefined
test_04_02_19 | pycomarduino | 0058924AB98D5AD4 | 1 | 159 | WzRdIEQyMC8wNS8xOCB0MTI6MDAgVzAwMDAgVDAwMDAgPyAxICAgAA== | [4] D20/05/18 t12:00 W0000 T0000 ? 1 | 2020-06-17T03:56:08.017872452Z | 868,5 | LORA | SF7BW125 | 4/5 | undefined | eui-fcc23dfffe0b696a | 3040496571 | 2 | -111 | -0,5 | undefined | undefined | undefined | eui-b827ebfffef74e1a | 2130964451 | 2 | -81 | 8 | undefined | undefined | undefined
test_04_02_19 | pycomarduino | 0058924AB98D5AD4 | 1 | 160 | WzVdIEQyMC8wNS8xOCB0MTI6MDAgVzAwMDAgVDAwMDAgPyAxICAgAA== | [5] D20/05/18 t12:00 W0000 T0000 ? 1 | 2020-06-17T03:57:21.834653765Z | 868,1 | LORA | SF7BW125 | 4/5 | undefined | eui-fcc23dfffe0b696a | 3114304555 | 0 | -116 | -6,5 | undefined | undefined | undefined | eui-b827ebfffef74e1a | 2204772467 | 0 | -83 | 9 | undefined | undefined | undefined
test_04_02_19 | pycomarduino | 0058924AB98D5AD4 | 1 | 161 | WzJdIEQyMC8wNS8xOCB0MTI6MDAgVzAwMDAgVDAwMDAgPyAxICAgAA== | [2] D20/05/18 t12:00 W0000 T0000 ? 1 | 2020-06-17T04:14:06.80348017Z | 867,1 | LORA | SF7BW125 | 4/5 | undefined | eui-fcc23dfffe0b696a | 4119272203 | 3 | -117 | -2 | undefined | undefined | undefined | eui-b827ebfffef74e1a | 3209740579 | 3 | -87 | 10 | undefined | undefined | undefined
test_04_02_19 | pycomarduino | 0058924AB98D5AD4 | 1 | 162 | WzNdIEQyMC8wNS8xOCB0MTI6MDAgVzAwMDAgVDAwMDAgPyAxICAgAA== | [3] D20/05/18 t12:00 W0000 T0000 ? 1 | 2020-06-17T04:15:11.549992945Z | 868,3 | LORA | SF7BW125 | 4/5 | undefined | eui-b827ebfffef74e1a | 3274495851 | 1 | -81 | 10 | undefined | undefined | undefined
test_04_02_19 | pycomarduino | 0058924AB98D5AD4 | 1 | 163 | WzRdIEQyMC8wNS8xOCB0MTI6MDAgVzAwMDAgVDAwMDAgPyAxICAgAA== | [4] D20/05/18 t12:00 W0000 T0000 ? 1 | 2020-06-17T04:16:08.021349801Z | 868,5 | LORA | SF7BW125 | 4/5 | undefined | eui-fcc23dfffe0b696a | 4240494427 | 2 | -110 | -0,5 | undefined | undefined | undefined | eui-b827ebfffef74e1a | 3330962851 | 2 | -81 | 7 | undefined | undefined | undefined
test_04_02_19 | pycomarduino | 0058924AB98D5AD4 | 1 | 164 | WzVdIEQyMC8wNS8xOCB0MTI6MDAgVzAwMDAgVDAwMDAgPyAxICAgAA== | [5] D20/05/18 t12:00 W0000 T0000 ? 1 | 2020-06-17T04:17:21.82541511Z | 867,3 | LORA | SF7BW125 | 4/5 | undefined | eui-fcc23dfffe0a9698 | 21389603 | 4 | -113 | -7 | undefined | undefined | undefined | eui-fcc23dfffe0b696a | 19336363 | 4 | -113 | -0,8 | undefined | undefined | undefined | eui-b827ebfffef74e1a | 3404772123 | 4 | -87 | 10 | undefined | undefined | undefined
test_04_02_19 | pycomarduino | 0058924AB98D5AD4 | 1 | 165 | WzJdIEQyMC8wNS8xOCB0MTI6MDAgVzAwMDAgVDAwMDAgPyAxICAgAA== | [2] D20/05/18 t12:00 W0000 T0000 ? 1 | 2020-06-17T04:34:06.808084364Z | 868,1 | LORA | SF7BW125 | 4/5 | undefined | eui-fcc23dfffe0b696a | 1024308459 | 0 | -117 | -3 | undefined | undefined | undefined | eui-b827ebfffef74e1a | 114777387 | 0 | -82 | 9,8 | undefined | undefined | undefined
test_04_02_19 | pycomarduino | 0058924AB98D5AD4 | 1 | 166 | WzNdIEQyMC8wNS8xOCB0MTI6MDAgVzAwMDAgVDAwMDAgPyAxICAgAA== | [3] D20/05/18 t12:00 W0000 T0000 ? 1 | 2020-06-17T04:35:11.552938836Z | 867,5 | LORA | SF7BW125 | 4/5 | undefined | eui-fcc23dfffe0b696a | 1089057108 | 5 | -113 | -5,2 | undefined | undefined | undefined | eui-b827ebfffef74e1a | 179526060 | 5 | -84 | 7,8 | undefined | undefined | undefined
test_04_02_19 | pycomarduino | 0058924AB98D5AD4 | 1 | 167 | WzRdIEQyMC8wNS8xOCB0MTI6MDAgVzAwMDAgVDAwMDAgPyAxICAgAA== | [4] D20/05/18 t12:00 W0000 T0000 ? 1 | 2020-06-17T04:36:08.058544017Z | 868,3 | LORA | SF7BW125 | 4/5 | undefined | eui-b827ebfffef74e1a | 235995955 | 1 | -79 | 8,8 | undefined | undefined | undefined
test_04_02_19 | pycomarduino | 0058924AB98D5AD4 | 1 | 168 | WzVdIEQyMC8wNS8xOCB0MTI6MDAgVzAwMDAgVDAwMDAgPyAxICAgAA== | [5] D20/05/18 t12:00 W0000 T0000 ? 1 | 2020-06-17T04:37:21.8371386Z | 868,5 | LORA | SF7BW125 | 4/5 | undefined | eui-fcc23dfffe0b696a | 1219337468 | 2 | -111 | 0 | undefined | undefined | undefined | eui-b827ebfffef74e1a | 309806475 | 2 | -79 | 8 | undefined | undefined | undefined
test_04_02_19 | pycomarduino | 0058924AB98D5AD4 | 1 | 169 | WzJdIEQyMC8wNS8xOCB0MTI6MDAgVzAwMDAgVDAwMDAgPyAxICAgAA== | [2] D20/05/18 t12:00 W0000 T0000 ? 1 | 2020-06-17T04:54:06.805056461Z | 867,7 | LORA | SF7BW125 | 4/5 | undefined | eui-fcc23dfffe0b696a | 2224309780 | 6 | -114 | -5,2 | undefined | undefined | undefined | eui-b827ebfffef74e1a | 1314779260 | 6 | -82 | 10,2 | undefined | undefined | undefined
test_04_02_19 | pycomarduino | 0058924AB98D5AD4 | 1 | 170 | WzNdIEQyMC8wNS8xOCB0MTI6MDAgVzAwMDAgVDAwMDAgPyAxICAgAA== | [3] D20/05/18 t12:00 W0000 T0000 ? 1 | 2020-06-17T04:55:11.542087371Z | 868,1 | LORA | SF7BW125 | 4/5 | undefined | eui-fcc23dfffe0b696a | 2289052203 | 0 | -115 | -3,8 | undefined | undefined | undefined | eui-b827ebfffef74e1a | 1379521715 | 0 | -83 | 9,5 | undefined | undefined | undefined
test_04_02_19 | pycomarduino | 0058924AB98D5AD4 | 1 | 171 | WzRdIEQyMC8wNS8xOCB0MTI6MDAgVzAwMDAgVDAwMDAgPyAxICAgAA== | [4] D20/05/18 t12:00 W0000 T0000 ? 1 | 2020-06-17T04:56:08.02310545Z | 868,3 | LORA | SF7BW125 | 4/5 | undefined | eui-b827ebfffef74e1a | 1435994331 | 1 | -79 | 9,5 | undefined | undefined | undefined
test_04_02_19 | pycomarduino | 0058924AB98D5AD4 | 1 | 172 | WzVdIEQyMC8wNS8xOCB0MTI6MDAgVzAwMDAgVDAwMDAgPyAxICAgAA== | [5] D20/05/18 t12:00 W0000 T0000 ? 1 | 2020-06-17T04:57:21.82653823Z | 867,9 | LORA | SF7BW125 | 4/5 | undefined | eui-fcc23dfffe0b696a | 2419336572 | 7 | -114 | 0 | undefined | undefined | undefined | eui-b827ebfffef74e1a | 1509806140 | 7 | -84 | 10,2 | undefined | undefined | undefined
test_04_02_19 | pycomarduino | 0058924AB98D5AD4 | 1 | 173 | WzJdIEQyMC8wNS8xOCB0MTI6MDAgVzAwMDAgVDAwMDAgPyAxICAgAA== | [2] D20/05/18 t12:00 W0000 T0000 ? 1 | 2020-06-17T05:14:06.805897537Z | 868,5 | LORA | SF7BW125 | 4/5 | undefined | eui-fcc23dfffe0b696a | 3424313339 | 2 | -113 | -0,2 | undefined | undefined | undefined | eui-b827ebfffef74e1a | 2514783379 | 2 | -78 | 7,5 | undefined | undefined | undefined
test_04_02_19 | pycomarduino | 0058924AB98D5AD4 | 1 | 174 | WzNdIEQyMC8wNS8xOCB0MTI6MDAgVzAwMDAgVDAwMDAgPyAxICAgAA== | [3] D20/05/18 t12:00 W0000 T0000 ? 1 | 2020-06-17T05:15:11.539573481Z | 867,1 | LORA | SF7BW125 | 4/5 | undefined | eui-fcc23dfffe0b696a | 3489049259 | 3 | -114 | -1 | undefined | undefined | undefined | eui-b827ebfffef74e1a | 2579519323 | 3 | -89 | 11,8 | undefined | undefined | undefined
test_04_02_19 | pycomarduino | 0058924AB98D5AD4 | 1 | 175 | WzRdIEQyMC8wNS8xOCB0MTI6MDAgVzAwMDAgVDAwMDAgPyAxICAgAA== | [4] D20/05/18 t12:00 W0000 T0000 ? 1 | 2020-06-17T05:16:08.022942789Z | 868,1 | LORA | SF7BW125 | 4/5 | undefined | eui-fcc23dfffe0b696a | 3545524763 | 0 | -116 | -3 | undefined | undefined | undefined | eui-b827ebfffef74e1a | 2635994851 | 0 | -81 | 10,2 | undefined | undefined | undefined
test_04_02_19 | pycomarduino | 0058924AB98D5AD4 | 1 | 176 | WzVdIEQyMC8wNS8xOCB0MTI6MDAgVzAwMDAgVDAwMDAgPyAxICAgAA== | [5] D20/05/18 t12:00 W0000 T0000 ? 1 | 2020-06-17T05:17:21.829926565Z | 868,3 | LORA | SF7BW125 | 4/5 | undefined | eui-fcc23dfffe0b696a | 3619337715 | 1 | -109 | -0,2 | undefined | undefined | undefined | eui-b827ebfffef74e1a | 2709807843 | 1 | -81 | 9,2 | undefined | undefined | undefined
test_04_02_19 | pycomarduino | 0058924AB98D5AD4 | 1 | 177 | WzJdIEQyMC8wNS8xOCB0MTI6MDAgVzAwMDAgVDAwMDAgPyAxICAgAA== | [2] D20/05/18 t12:00 W0000 T0000 ? 1 | 2020-06-17T05:34:06.811736526Z | 867,3 | LORA | SF7BW125 | 4/5 | undefined | eui-fcc23dfffe0b696a | 329347499 | 4 | -113 | -1 | undefined | undefined | undefined | eui-b827ebfffef74e1a | 3714785387 | 4 | -83 | 9,5 | undefined | undefined | undefined
test_04_02_19 | pycomarduino | 0058924AB98D5AD4 | 1 | 178 | WzNdIEQyMC8wNS8xOCB0MTI6MDAgVzAwMDAgVDAwMDAgPyAxICAgAA== | [3] D20/05/18 t12:00 W0000 T0000 ? 1 | 2020-06-17T05:35:11.541517766Z | 868,5 | LORA | SF7BW125 | 4/5 | undefined | eui-b827ebfffef74e1a | 3779514955 | 2 | -79 | 7 | undefined | undefined | undefined
test_04_02_19 | pycomarduino | 0058924AB98D5AD4 | 1 | 179 | WzRdIEQyMC8wNS8xOCB0MTI6MDAgVzAwMDAgVDAwMDAgPyAxICAgAA== | [4] D20/05/18 t12:00 W0000 T0000 ? 1 | 2020-06-17T05:36:08.015349449Z | 868,1 | LORA | SF7BW125 | 4/5 | undefined | eui-fcc23dfffe0b696a | 450555427 | 0 | -113 | -6 | undefined | undefined | undefined | eui-b827ebfffef74e1a | 3835993379 | 0 | -81 | 9 | undefined | undefined | undefined
test_04_02_19 | pycomarduino | 0058924AB98D5AD4 | 1 | 180 | WzVdIEQyMC8wNS8xOCB0MTI6MDAgVzAwMDAgVDAwMDAgPyAxICAgAA== | [5] D20/05/18 t12:00 W0000 T0000 ? 1 | 2020-06-17T05:37:21.835326096Z | 867,5 | LORA | SF7BW125 | 4/5 | undefined | eui-fcc23dfffe0b696a | 524369612 | 5 | -115 | -2,8 | undefined | undefined | undefined | eui-b827ebfffef74e1a | 3909807596 | 5 | -88 | 7,2 | undefined | undefined | undefined
test_04_02_19 | pycomarduino | 0058924AB98D5AD4 | 1 | 181 | WzJdIEQyMC8wNS8xOCB0MTI6MDAgVzAwMDAgVDAwMDAgPyAxICAgAA== | [2] D20/05/18 t12:00 W0000 T0000 ? 1 | 2020-06-17T05:54:06.813453153Z | 868,3 | LORA | SF7BW125 | 4/5 | undefined | eui-b827ebfffef74e1a | 619822163 | 1 | -78 | 9,5 | undefined | undefined | undefined
test_04_02_19 | pycomarduino | 0058924AB98D5AD4 | 1 | 182 | WzNdIEQyMC8wNS8xOCB0MTI6MDAgVzAwMDAgVDAwMDAgPyAxICAgAA== | [3] D20/05/18 t12:00 W0000 T0000 ? 1 | 2020-06-17T05:55:11.536850709Z | 867,7 | LORA | SF7BW125 | 4/5 | undefined | eui-b827ebfffef74e1a | 684545380 | 6 | -84 | 10,2 | undefined | undefined | undefined
test_04_02_19 | pycomarduino | 0058924AB98D5AD4 | 1 | 183 | WzRdIEQyMC8wNS8xOCB0MTI6MDAgVzAwMDAgVDAwMDAgPyAxICAgAA== | [4] D20/05/18 t12:00 W0000 T0000 ? 1 | 2020-06-17T05:56:08.018298315Z | 868,5 | LORA | SF7BW125 | 4/5 | undefined | eui-fcc23dfffe0b696a | 1650555523 | 2 | -111 | -0,8 | undefined | undefined | undefined | eui-b827ebfffef74e1a | 741026731 | 2 | -81 | 7,8 | undefined | undefined | undefined
test_04_02_19 | pycomarduino | 0058924AB98D5AD4 | 1 | 184 | WzVdIEQyMC8wNS8xOCB0MTI6MDAgVzAwMDAgVDAwMDAgPyAxICAgAA== | [5] D20/05/18 t12:00 W0000 T0000 ? 1 | 2020-06-17T05:57:21.828222993Z | 868,1 | LORA | SF7BW125 | 4/5 | undefined | eui-fcc23dfffe0b696a | 1724370819 | 0 | -117 | -1,5 | undefined | undefined | undefined | eui-b827ebfffef74e1a | 814842067 | 0 | -81 | 9,8 | undefined | undefined | undefined
test_04_02_19 | pycomarduino | 0058924AB98D5AD4 | 1 | 185 | WzJdIEQyMC8wNS8xOCB0MTI6MDAgVzAwMDAgVDAwMDAgPyAxICAgAA== | [2] D20/05/18 t12:00 W0000 T0000 ? 1 | 2020-06-17T06:14:06.818833645Z | 867,9 | LORA | SF7BW125 | 4/5 | undefined | eui-fcc23dfffe0b696a | 2729352460 | 7 | -115 | 0,2 | undefined | undefined | undefined | eui-b827ebfffef74e1a | 1819824180 | 7 | -81 | 10,2 | undefined | undefined | undefined
test_04_02_19 | pycomarduino | 0058924AB98D5AD4 | 1 | 186 | WzNdIEQyMC8wNS8xOCB0MTI6MDAgVzAwMDAgVDAwMDAgPyAxICAgAA== | [3] D20/05/18 t12:00 W0000 T0000 ? 1 | 2020-06-17T06:15:11.530634637Z | 868,3 | LORA | SF7BW125 | 4/5 | undefined | eui-b827ebfffef74e1a | 1884541019 | 1 | -81 | 10 | undefined | undefined | undefined
test_04_02_19 | pycomarduino | 0058924AB98D5AD4 | 1 | 187 | WzRdIEQyMC8wNS8xOCB0MTI6MDAgVzAwMDAgVDAwMDAgPyAxICAgAA== | [4] D20/05/18 t12:00 W0000 T0000 ? 1 | 2020-06-17T06:16:08.021273059Z | 868,5 | LORA | SF7BW125 | 4/5 | undefined | eui-b827ebfffef74e1a | 1941025315 | 2 | -79 | 8 | undefined | undefined | undefined
test_04_02_19 | pycomarduino | 0058924AB98D5AD4 | 1 | 188 | WzVdIEQyMC8wNS8xOCB0MTI6MDAgVzAwMDAgVDAwMDAgPyAxICAgAA== | [5] D20/05/18 t12:00 W0000 T0000 ? 1 | 2020-06-17T06:17:21.831994113Z | 867,1 | LORA | SF7BW125 | 4/5 | undefined | eui-fcc23dfffe0a9698 | 2926421611 | 3 | -117 | -7,2 | undefined | undefined | undefined | eui-fcc23dfffe0b696a | 2924370019 | 3 | -116 | -0,5 | undefined | undefined | undefined | eui-b827ebfffef74e1a | 2014841819 | 3 | -87 | 10,2 | undefined | undefined | undefined
test_04_02_19 | pycomarduino | 0058924AB98D5AD4 | 1 | 189 | WzJdIEQyMC8wNS8xOCB0MTI6MDAgVzAwMDAgVDAwMDAgPyAxICAgAA== | [2] D20/05/18 t12:00 W0000 T0000 ? 1 | 2020-06-17T06:34:06.825630837Z | 868,1 | LORA | SF7BW125 | 4/5 | undefined | eui-fcc23dfffe0b696a | 3929356035 | 0 | -116 | -1,2 | undefined | undefined | undefined | eui-b827ebfffef74e1a | 3019828307 | 0 | -83 | 9,8 | undefined | undefined | undefined
test_04_02_19 | pycomarduino | 0058924AB98D5AD4 | 1 | 190 | WzNdIEQyMC8wNS8xOCB0MTI6MDAgVzAwMDAgVDAwMDAgPyAxICAgAA== | [3] D20/05/18 t12:00 W0000 T0000 ? 1 | 2020-06-17T06:35:11.529849409Z | 867,3 | LORA | SF7BW125 | 4/5 | undefined | eui-fcc23dfffe0a9698 | 3996117899 | 4 | -117 | -8 | undefined | undefined | undefined | eui-fcc23dfffe0b696a | 3994066555 | 4 | -111 | 1,5 | undefined | undefined | undefined | eui-b827ebfffef74e1a | 3084538851 | 4 | -84 | 9,2 | undefined | undefined | undefined
test_04_02_19 | pycomarduino | 0058924AB98D5AD4 | 1 | 191 | WzRdIEQyMC8wNS8xOCB0MTI6MDAgVzAwMDAgVDAwMDAgPyAxICAgAA== | [4] D20/05/18 t12:00 W0000 T0000 ? 1 | 2020-06-17T06:36:08.013758852Z | 868,3 | LORA | SF7BW125 | 4/5 | undefined | eui-b827ebfffef74e1a | 3141025995 | 1 | -79 | 9,5 | undefined | undefined | undefined
test_04_02_19 | pycomarduino | 0058924AB98D5AD4 | 1 | 192 | WzVdIEQyMC8wNS8xOCB0MTI6MDAgVzAwMDAgVDAwMDAgPyAxICAgAA== | [5] D20/05/18 t12:00 W0000 T0000 ? 1 | 2020-06-17T06:37:21.841231054Z | 868,5 | LORA | SF7BW125 | 4/5 | undefined | eui-fcc23dfffe0b696a | 4124371251 | 2 | -113 | -0,8 | undefined | undefined | undefined | eui-b827ebfffef74e1a | 3214843611 | 2 | -78 | 7,8 | undefined | undefined | undefined
test_04_02_19 | pycomarduino | 0058924AB98D5AD4 | 1 | 193 | WzJdIEQyMC8wNS8xOCB0MTI6MDAgVzAwMDAgVDAwMDAgPyAxICAgAA== | [2] D20/05/18 t12:00 W0000 T0000 ? 1 | 2020-06-17T06:54:06.818292356Z | 867,5 | LORA | SF7BW125 | 4/5 | undefined | eui-fcc23dfffe0b696a | 834390180 | 5 | -114 | -4,8 | undefined | undefined | undefined | eui-b827ebfffef74e1a | 4219830308 | 5 | -83 | 7,2 | undefined | undefined | undefined
test_04_02_19 | pycomarduino | 0058924AB98D5AD4 | 1 | 194 | WzNdIEQyMC8wNS8xOCB0MTI6MDAgVzAwMDAgVDAwMDAgPyAxICAgAA== | [3] D20/05/18 t12:00 W0000 T0000 ? 1 | 2020-06-17T06:55:11.525087782Z | 868,1 | LORA | SF7BW125 | 4/5 | undefined | eui-fcc23dfffe0b696a | 899094627 | 0 | -117 | -1 | undefined | undefined | undefined | eui-b827ebfffef74e1a | 4284534779 | 0 | -81 | 9,2 | undefined | undefined | undefined
test_04_02_19 | pycomarduino | 0058924AB98D5AD4 | 1 | 195 | WzRdIEQyMC8wNS8xOCB0MTI6MDAgVzAwMDAgVDAwMDAgPyAxICAgAA== | [4] D20/05/18 t12:00 W0000 T0000 ? 1 | 2020-06-17T06:56:08.01286467Z | 868,3 | LORA | SF7BW125 | 4/5 | undefined | eui-b827ebfffef74e1a | 46057331 | 1 | -83 | 10,5 | undefined | undefined | undefined
test_04_02_19 | pycomarduino | 0058924AB98D5AD4 | 1 | 196 | WzVdIEQyMC8wNS8xOCB0MTI6MDAgVzAwMDAgVDAwMDAgPyAxICAgAA== | [5] D20/05/18 t12:00 W0000 T0000 ? 1 | 2020-06-17T06:57:21.842486444Z | 867,7 | LORA | SF7BW125 | 4/5 | undefined | eui-fcc23dfffe0b696a | 1029403236 | 6 | -117 | -5,2 | undefined | undefined | undefined | eui-b827ebfffef74e1a | 119876156 | 6 | -84 | 10 | undefined | undefined | undefined
test_04_02_19 | pycomarduino | 0058924AB98D5AD4 | 1 | 197 | WzJdIEQyMC8wNS8xOCB0MTI6MDAgVzAwMDAgVDAwMDAgPyAxICAgAA== | [2] D20/05/18 t12:00 W0000 T0000 ? 1 | 2020-06-17T07:14:06.826778657Z | 868,5 | LORA | SF7BW125 | 4/5 | undefined | eui-fcc23dfffe0b696a | 2034393731 | 2 | -112 | -0,5 | undefined | undefined | undefined | eui-b827ebfffef74e1a | 1124867115 | 2 | -79 | 7,8 | undefined | undefined | undefined
test_04_02_19 | pycomarduino | 0058924AB98D5AD4 | 1 | 198 | WzNdIEQyMC8wNS8xOCB0MTI6MDAgVzAwMDAgVDAwMDAgPyAxICAgAA== | [3] D20/05/18 t12:00 W0000 T0000 ? 1 | 2020-06-17T07:15:11.52120727Z | 867,9 | LORA | SF7BW125 | 4/5 | undefined | eui-fcc23dfffe0b696a | 2099092116 | 7 | -116 | -2 | undefined | undefined | undefined | eui-b827ebfffef74e1a | 1189565524 | 7 | -85 | 10 | undefined | undefined | undefined
test_04_02_19 | pycomarduino | 0058924AB98D5AD4 | 1 | 199 | WzRdIEQyMC8wNS8xOCB0MTI6MDAgVzAwMDAgVDAwMDAgPyAxICAgAA== | [4] D20/05/18 t12:00 W0000 T0000 ? 1 | 2020-06-17T07:16:08.015167836Z | 868,1 | LORA | SF7BW125 | 4/5 | undefined | eui-fcc23dfffe0b696a | 2155584731 | 0 | -117 | -1,2 | undefined | undefined | undefined | eui-b827ebfffef74e1a | 1246058163 | 0 | -84 | 10,5 | undefined | undefined | undefined
test_04_02_19 | pycomarduino | 0058924AB98D5AD4 | 1 | 200 | WzVdIEQyMC8wNS8xOCB0MTI6MDAgVzAwMDAgVDAwMDAgPyAxICAgAA== | [5] D20/05/18 t12:00 W0000 T0000 ? 1 | 2020-06-17T07:17:21.836778471Z | 868,3 | LORA | SF7BW125 | 4/5 | undefined | eui-b827ebfffef74e1a | 1319878211 | 1 | -81 | 9 | undefined | undefined | undefined
test_04_02_19 | pycomarduino | 0058924AB98D5AD4 | 1 | 201 | WzJdIEQyMC8wNS8xOCB0MTI6MDAgVzAwMDAgVDAwMDAgPyAxICAgAA== | [2] D20/05/18 t12:00 W0000 T0000 ? 1 | 2020-06-17T07:34:06.826464906Z | 867,1 | LORA | SF7BW125 | 4/5 | undefined | eui-fcc23dfffe0b696a | 3234395299 | 3 | -115 | -0,5 | undefined | undefined | undefined | eui-b827ebfffef74e1a | 2324869211 | 3 | -87 | 11,2 | undefined | undefined | undefined
test_04_02_19 | pycomarduino | 0058924AB98D5AD4 | 1 | 202 | WzNdIEQyMC8wNS8xOCB0MTI6MDAgVzAwMDAgVDAwMDAgPyAxICAgAA== | [3] D20/05/18 t12:00 W0000 T0000 ? 1 | 2020-06-17T07:35:11.516921819Z | 868,5 | LORA | SF7BW125 | 4/5 | undefined | eui-fcc23dfffe0b696a | 3299087587 | 2 | -112 | 0,2 | undefined | undefined | undefined | eui-b827ebfffef74e1a | 2389561523 | 2 | -81 | 8 | undefined | undefined | undefined
test_04_02_19 | pycomarduino | 0058924AB98D5AD4 | 1 | 203 | WzRdIEQyMC8wNS8xOCB0MTI6MDAgVzAwMDAgVDAwMDAgPyAxICAgAA== | [4] D20/05/18 t12:00 W0000 T0000 ? 1 | 2020-06-17T07:36:08.012997594Z | 868,1 | LORA | SF7BW125 | 4/5 | undefined | eui-b827ebfffef74e1a | 2446056971 | 0 | -83 | 9,8 | undefined | undefined | undefined
test_04_02_19 | pycomarduino | 0058924AB98D5AD4 | 1 | 204 | WzVdIEQyMC8wNS8xOCB0MTI6MDAgVzAwMDAgVDAwMDAgPyAxICAgAA== | [5] D20/05/18 t12:00 W0000 T0000 ? 1 | 2020-06-17T07:37:21.839071462Z | 867,3 | LORA | SF7BW125 | 4/5 | undefined | eui-fcc23dfffe0b696a | 3429404195 | 4 | -112 | 0 | undefined | undefined | undefined | eui-b827ebfffef74e1a | 2519878187 | 4 | -83 | 9 | undefined | undefined | undefined
test_04_02_19 | pycomarduino | 0058924AB98D5AD4 | 1 | 205 | WzJdIEQyMC8wNS8xOCB0MTI6MDAgVzAwMDAgVDAwMDAgPyAxICAgAA== | [2] D20/05/18 t12:00 W0000 T0000 ? 1 | 2020-06-17T07:54:06.837735886Z | 868,3 | LORA | SF7BW125 | 4/5 | undefined | eui-b827ebfffef74e1a | 3524873483 | 1 | -81 | 10,8 | undefined | undefined | undefined
test_04_02_19 | pycomarduino | 0058924AB98D5AD4 | 1 | 206 | WzNdIEQyMC8wNS8xOCB0MTI6MDAgVzAwMDAgVDAwMDAgPyAxICAgAA== | [3] D20/05/18 t12:00 W0000 T0000 ? 1 | 2020-06-17T07:55:11.517671456Z | 867,5 | LORA | SF7BW125 | 4/5 | undefined | eui-fcc23dfffe0b696a | 204117876 | 5 | -116 | -5 | undefined | undefined | undefined | eui-b827ebfffef74e1a | 3589559644 | 5 | -84 | 7,8 | undefined | undefined | undefined
test_04_02_19 | pycomarduino | 0058924AB98D5AD4 | 1 | 207 | WzRdIEQyMC8wNS8xOCB0MTI6MDAgVzAwMDAgVDAwMDAgPyAxICAgAA== | [4] D20/05/18 t12:00 W0000 T0000 ? 1 | 2020-06-17T07:56:08.01168041Z | 868,5 | LORA | SF7BW125 | 4/5 | undefined | eui-fcc23dfffe0b696a | 260616355 | 2 | -113 | -2 | undefined | undefined | undefined | eui-b827ebfffef74e1a | 3646058147 | 2 | -81 | 7,8 | undefined | undefined | undefined
test_04_02_19 | pycomarduino | 0058924AB98D5AD4 | 1 | 208 | WzVdIEQyMC8wNS8xOCB0MTI6MDAgVzAwMDAgVDAwMDAgPyAxICAgAA== | [5] D20/05/18 t12:00 W0000 T0000 ? 1 | 2020-06-17T07:57:21.836613919Z | 868,1 | LORA | SF7BW125 | 4/5 | undefined | eui-b827ebfffef74e1a | 3719880315 | 0 | -83 | 10,2 | undefined | undefined | undefined
test_04_02_19 | pycomarduino | 0058924AB98D5AD4 | 1 | 209 | WzJdIEQyMC8wNS8xOCB0MTI6MDAgVzAwMDAgVDAwMDAgPyAxICAgAA== | [2] D20/05/18 t12:00 W0000 T0000 ? 1 | 2020-06-17T08:14:06.856215641Z | 867,7 | LORA | SF7BW125 | 4/5 | undefined | eui-fcc23dfffe0b696a | 1339433316 | 6 | -117 | -8,2 | undefined | undefined | undefined | eui-b827ebfffef74e1a | 429908308 | 6 | -82 | 10 | undefined | undefined | undefined
test_04_02_19 | pycomarduino | 0058924AB98D5AD4 | 1 | 210 | WzNdIEQyMC8wNS8xOCB0MTI6MDAgVzAwMDAgVDAwMDAgPyAxICAgAA== | [3] D20/05/18 t12:00 W0000 T0000 ? 1 | 2020-06-17T08:15:11.50932079Z | 868,3 | LORA | SF7BW125 | 4/5 | undefined | eui-b827ebfffef74e1a | 494588475 | 1 | -78 | 10,8 | undefined | undefined | undefined
test_04_02_19 | pycomarduino | 0058924AB98D5AD4 | 1 | 211 | WzRdIEQyMC8wNS8xOCB0MTI6MDAgVzAwMDAgVDAwMDAgPyAxICAgAA== | [4] D20/05/18 t12:00 W0000 T0000 ? 1 | 2020-06-17T08:16:08.018684656Z | 868,5 | LORA | SF7BW125 | 4/5 | undefined | eui-b827ebfffef74e1a | 551089963 | 2 | -83 | 7,5 | undefined | undefined | undefined
test_04_02_19 | pycomarduino | 0058924AB98D5AD4 | 1 | 212 | WzVdIEQyMC8wNS8xOCB0MTI6MDAgVzAwMDAgVDAwMDAgPyAxICAgAA== | [5] D20/05/18 t12:00 W0000 T0000 ? 1 | 2020-06-17T08:17:21.835622438Z | 867,9 | LORA | SF7BW125 | 4/5 | undefined | eui-fcc23dfffe0b696a | 1534437988 | 7 | -118 | -4,5 | undefined | undefined | undefined | eui-b827ebfffef74e1a | 624913060 | 7 | -82 | 9 | undefined | undefined | undefined
test_04_02_19 | pycomarduino | 0058924AB98D5AD4 | 1 | 213 | WzJdIEQyMC8wNS8xOCB0MTI6MDAgVzAwMDAgVDAwMDAgPyAxICAgAA== | [2] D20/05/18 t12:00 W0000 T0000 ? 1 | 2020-06-17T08:34:06.837860848Z | 868,1 | LORA | SF7BW125 | 4/5 | undefined | eui-fcc23dfffe0b696a | 2539437083 | 0 | -115 | -2 | undefined | undefined | undefined | eui-b827ebfffef74e1a | 1629912603 | 0 | -85 | 9,2 | undefined | undefined | undefined
test_04_02_19 | pycomarduino | 0058924AB98D5AD4 | 1 | 214 | WzNdIEQyMC8wNS8xOCB0MTI6MDAgVzAwMDAgVDAwMDAgPyAxICAgAA== | [3] D20/05/18 t12:00 W0000 T0000 ? 1 | 2020-06-17T08:35:11.514092159Z | 867,1 | LORA | SF7BW125 | 4/5 | undefined | eui-fcc23dfffe0b696a | 2604111043 | 3 | -117 | -3 | undefined | undefined | undefined | eui-b827ebfffef74e1a | 1694586587 | 3 | -90 | 9,8 | undefined | undefined | undefined
test_04_02_19 | pycomarduino | 0058924AB98D5AD4 | 1 | 215 | WzRdIEQyMC8wNS8xOCB0MTI6MDAgVzAwMDAgVDAwMDAgPyAxICAgAA== | [4] D20/05/18 t12:00 W0000 T0000 ? 1 | 2020-06-17T08:36:08.020832118Z | 868,3 | LORA | SF7BW125 | 4/5 | undefined | eui-b827ebfffef74e1a | 1751091051 | 1 | -83 | 10,5 | undefined | undefined | undefined
test_04_02_19 | pycomarduino | 0058924AB98D5AD4 | 1 | 216 | WzVdIEQyMC8wNS8xOCB0MTI6MDAgVzAwMDAgVDAwMDAgPyAxICAgAA== | [5] D20/05/18 t12:00 W0000 T0000 ? 1 | 2020-06-17T08:37:21.840190702Z | 868,5 | LORA | SF7BW125 | 4/5 | undefined | eui-fcc23dfffe0b696a | 2734439675 | 2 | -113 | -0,8 | undefined | undefined | undefined | eui-b827ebfffef74e1a | 1824915275 | 2 | -82 | 7,8 | undefined | undefined | undefined
test_04_02_19 | pycomarduino | 0058924AB98D5AD4 | 1 | 217 | WzJdIEQyMC8wNS8xOCB0MTI6MDAgVzAwMDAgVDAwMDAgPyAxICAgAA== | [2] D20/05/18 t12:00 W0000 T0000 ? 1 | 2020-06-17T08:54:06.836060315Z | 867,3 | LORA | SF7BW125 | 4/5 | undefined | eui-fcc23dfffe0b696a | 3739438899 | 4 | -112 | 0 | undefined | undefined | undefined | eui-b827ebfffef74e1a | 2829914907 | 4 | -85 | 9,2 | undefined | undefined | undefined
test_04_02_19 | pycomarduino | 0058924AB98D5AD4 | 1 | 218 | WzNdIEQyMC8wNS8xOCB0MTI6MDAgVzAwMDAgVDAwMDAgPyAxICAgAA== | [3] D20/05/18 t12:00 W0000 T0000 ? 1 | 2020-06-17T08:55:11.514391218Z | 868,1 | LORA | SF7BW125 | 4/5 | undefined | eui-b827ebfffef74e1a | 2894582779 | 0 | -81 | 9,2 | undefined | undefined | undefined
test_04_02_19 | pycomarduino | 0058924AB98D5AD4 | 1 | 219 | WzRdIEQyMC8wNS8xOCB0MTI6MDAgVzAwMDAgVDAwMDAgPyAxICAgAA== | [4] D20/05/18 t12:00 W0000 T0000 ? 1 | 2020-06-17T08:56:08.028957274Z | 868,3 | LORA | SF7BW125 | 4/5 | undefined | eui-b827ebfffef74e1a | 2951090147 | 1 | -83 | 10 | undefined | undefined | undefined
test_04_02_19 | pycomarduino | 0058924AB98D5AD4 | 1 | 220 | WzVdIEQyMC8wNS8xOCB0MTI6MDAgVzAwMDAgVDAwMDAgPyAxICAgAA== | [5] D20/05/18 t12:00 W0000 T0000 ? 1 | 2020-06-17T08:57:21.837903645Z | 867,5 | LORA | SF7BW125 | 4/5 | undefined | eui-fcc23dfffe0b696a | 3934439420 | 5 | -116 | -6,2 | undefined | undefined | undefined | eui-b827ebfffef74e1a | 3024915516 | 5 | -85 | 8 | undefined | undefined | undefined
test_04_02_19 | pycomarduino | 0058924AB98D5AD4 | 1 | 221 | WzJdIEQyMC8wNS8xOCB0MTI6MDAgVzAwMDAgVDAwMDAgPyAxICAgAA== | [2] D20/05/18 t12:00 W0000 T0000 ? 1 | 2020-06-17T09:14:06.843025595Z | 868,5 | LORA | SF7BW125 | 4/5 | undefined | eui-fcc23dfffe0b696a | 644475371 | 2 | -112 | -2 | undefined | undefined | undefined | eui-b827ebfffef74e1a | 4029919195 | 2 | -83 | 7,8 | undefined | undefined | undefined
test_04_02_19 | pycomarduino | 0058924AB98D5AD4 | 1 | 222 | WzNdIEQyMC8wNS8xOCB0MTI6MDAgVzAwMDAgVDAwMDAgPyAxICAgAA== | [3] D20/05/18 t12:00 W0000 T0000 ? 1 | 2020-06-17T09:15:11.51726071Z | 867,7 | LORA | SF7BW125 | 4/5 | undefined | eui-b827ebfffef74e1a | 4094581108 | 6 | -85 | 9,8 | undefined | undefined | undefined
test_04_02_19 | pycomarduino | 0058924AB98D5AD4 | 1 | 223 | WzRdIEQyMC8wNS8xOCB0MTI6MDAgVzAwMDAgVDAwMDAgPyAxICAgAA== | [4] D20/05/18 t12:00 W0000 T0000 ? 1 | 2020-06-17T09:16:08.013216744Z | 868,1 | LORA | SF7BW125 | 4/5 | undefined | eui-b827ebfffef74e1a | 4151091323 | 0 | -83 | 9,2 | undefined | undefined | undefined
test_04_02_19 | pycomarduino | 0058924AB98D5AD4 | 1 | 224 | WzVdIEQyMC8wNS8xOCB0MTI6MDAgVzAwMDAgVDAwMDAgPyAxICAgAA== | [5] D20/05/18 t12:00 W0000 T0000 ? 1 | 2020-06-17T09:17:21.842962959Z | 868,3 | LORA | SF7BW125 | 4/5 | undefined | eui-fcc23dfffe0b696a | 839473851 | 1 | -111 | -2,5 | undefined | undefined | undefined | eui-b827ebfffef74e1a | 4224917747 | 1 | -81 | 9,8 | undefined | undefined | undefined
test_04_02_19 | pycomarduino | 0058924AB98D5AD4 | 1 | 225 | WzJdIEQyMC8wNS8xOCB0MTI6MDAgVzAwMDAgVDAwMDAgPyAxICAgAA== | [2] D20/05/18 t12:00 W0000 T0000 ? 1 | 2020-06-17T09:34:06.863770384Z | 867,9 | LORA | SF7BW125 | 4/5 | undefined | eui-fcc23dfffe0b696a | 1844477260 | 7 | -117 | -8 | undefined | undefined | undefined | eui-b827ebfffef74e1a | 934954292 | 7 | -81 | 9,5 | undefined | undefined | undefined
test_04_02_19 | pycomarduino | 0058924AB98D5AD4 | 1 | 226 | WzNdIEQyMC8wNS8xOCB0MTI6MDAgVzAwMDAgVDAwMDAgPyAxICAgAA== | [3] D20/05/18 t12:00 W0000 T0000 ? 1 | 2020-06-17T09:35:11.499913133Z | 868,5 | LORA | SF7BW125 | 4/5 | undefined | eui-fcc23dfffe0b696a | 1909133035 | 2 | -116 | -2 | undefined | undefined | undefined | eui-b827ebfffef74e1a | 999610099 | 2 | -81 | 7,8 | undefined | undefined | undefined
test_04_02_19 | pycomarduino | 0058924AB98D5AD4 | 1 | 227 | WzRdIEQyMC8wNS8xOCB0MTI6MDAgVzAwMDAgVDAwMDAgPyAxICAgAA== | [4] D20/05/18 t12:00 W0000 T0000 ? 1 | 2020-06-17T09:36:08.017250072Z | 868,1 | LORA | SF7BW125 | 4/5 | undefined | eui-fcc23dfffe0b696a | 1965646059 | 0 | -117 | -2,8 | undefined | undefined | undefined | eui-b827ebfffef74e1a | 1056123147 | 0 | -82 | 10 | undefined | undefined | undefined
test_04_02_19 | pycomarduino | 0058924AB98D5AD4 | 1 | 228 | WzVdIEQyMC8wNS8xOCB0MTI6MDAgVzAwMDAgVDAwMDAgPyAxICAgAA== | [5] D20/05/18 t12:00 W0000 T0000 ? 1 | 2020-06-17T09:37:21.841236793Z | 867,1 | LORA | SF7BW125 | 4/5 | undefined | eui-fcc23dfffe0a9698 | 2041521915 | 3 | -117 | -8,5 | undefined | undefined | undefined | eui-fcc23dfffe0b696a | 2039473603 | 3 | -117 | -1,2 | undefined | undefined | undefined | eui-b827ebfffef74e1a | 1129950723 | 3 | -87 | 9,8 | undefined | undefined | undefined
test_04_02_19 | pycomarduino | 0058924AB98D5AD4 | 1 | 229 | WzJdIEQyMC8wNS8xOCB0MTI6MDAgVzAwMDAgVDAwMDAgPyAxICAgAA== | [2] D20/05/18 t12:00 W0000 T0000 ? 1 | 2020-06-17T09:54:06.848501469Z | 868,3 | LORA | SF7BW125 | 4/5 | undefined | eui-b827ebfffef74e1a | 2134958403 | 1 | -81 | 10,5 | undefined | undefined | undefined
test_04_02_19 | pycomarduino | 0058924AB98D5AD4 | 1 | 230 | WzNdIEQyMC8wNS8xOCB0MTI6MDAgVzAwMDAgVDAwMDAgPyAxICAgAA== | [3] D20/05/18 t12:00 W0000 T0000 ? 1 | 2020-06-17T09:55:11.502939868Z | 867,3 | LORA | SF7BW125 | 4/5 | undefined | eui-fcc23dfffe0b696a | 3109130459 | 4 | -115 | -0,8 | undefined | undefined | undefined | eui-b827ebfffef74e1a | 2199608043 | 4 | -84 | 9,5 | undefined | undefined | undefined
test_04_02_19 | pycomarduino | 0058924AB98D5AD4 | 1 | 231 | WzRdIEQyMC8wNS8xOCB0MTI6MDAgVzAwMDAgVDAwMDAgPyAxICAgAA== | [4] D20/05/18 t12:00 W0000 T0000 ? 1 | 2020-06-17T09:56:08.019503118Z | 868,5 | LORA | SF7BW125 | 4/5 | undefined | eui-fcc23dfffe0b696a | 3165646475 | 2 | -112 | -0,8 | undefined | undefined | undefined | eui-b827ebfffef74e1a | 2256124075 | 2 | -78 | 7,8 | undefined | undefined | undefined
test_04_02_19 | pycomarduino | 0058924AB98D5AD4 | 1 | 232 | WzVdIEQyMC8wNS8xOCB0MTI6MDAgVzAwMDAgVDAwMDAgPyAxICAgAA== | [5] D20/05/18 t12:00 W0000 T0000 ? 1 | 2020-06-17T09:57:21.848128319Z | 868,1 | LORA | SF7BW125 | 4/5 | undefined | eui-fcc23dfffe0b696a | 3239475171 | 0 | -110 | -2,5 | undefined | undefined | undefined | eui-b827ebfffef74e1a | 2329952811 | 0 | -83 | 10,2 | undefined | undefined | undefined
test_04_02_19 | pycomarduino | 0058924AB98D5AD4 | 1 | 233 | WzJdIEQyMC8wNS8xOCB0MTI6MDAgVzAwMDAgVDAwMDAgPyAxICAgAA== | [2] D20/05/18 t12:00 W0000 T0000 ? 1 | 2020-06-17T10:14:06.853992262Z | 867,5 | LORA | SF7BW125 | 4/5 | undefined | eui-b827ebfffef74e1a | 3334960756 | 5 | -84 | 7,5 | undefined | undefined | undefined
test_04_02_19 | pycomarduino | 0058924AB98D5AD4 | 1 | 234 | WzNdIEQyMC8wNS8xOCB0MTI6MDAgVzAwMDAgVDAwMDAgPyAxICAgAA== | [3] D20/05/18 t12:00 W0000 T0000 ? 1 | 2020-06-17T10:15:11.499941927Z | 868,3 | LORA | SF7BW125 | 4/5 | undefined | eui-b827ebfffef74e1a | 3399604467 | 1 | -83 | 10 | undefined | undefined | undefined
test_04_02_19 | pycomarduino | 0058924AB98D5AD4 | 1 | 235 | WzRdIEQyMC8wNS8xOCB0MTI6MDAgVzAwMDAgVDAwMDAgPyAxICAgAA== | [4] D20/05/18 t12:00 W0000 T0000 ? 1 | 2020-06-17T10:16:08.009838186Z | 868,5 | LORA | SF7BW125 | 4/5 | undefined | eui-fcc23dfffe0b696a | 70677835 | 2 | -116 | -3,5 | undefined | undefined | undefined | eui-b827ebfffef74e1a | 3456123227 | 2 | -83 | 8,5 | undefined | undefined | undefined
test_04_02_19 | pycomarduino | 0058924AB98D5AD4 | 1 | 236 | WzVdIEQyMC8wNS8xOCB0MTI6MDAgVzAwMDAgVDAwMDAgPyAxICAgAA== | [5] D20/05/18 t12:00 W0000 T0000 ? 1 | 2020-06-17T10:17:21.842125111Z | 867,7 | LORA | SF7BW125 | 4/5 | undefined | eui-fcc23dfffe0b696a | 144507700 | 6 | -116 | -8 | undefined | undefined | undefined | eui-b827ebfffef74e1a | 3529953116 | 6 | -83 | 9 | undefined | undefined | undefined
test_04_02_19 | pycomarduino | 0058924AB98D5AD4 | 1 | 237 | WzJdIEQyMC8wNS8xOCB0MTI6MDAgVzAwMDAgVDAwMDAgPyAxICAgAA== | [2] D20/05/18 t12:00 W0000 T0000 ? 1 | 2020-06-17T10:34:06.856464776Z | 868,1 | LORA | SF7BW125 | 4/5 | undefined | eui-fcc23dfffe0b696a | 1149519459 | 0 | -115 | 0 | undefined | undefined | undefined | eui-b827ebfffef74e1a | 239997979 | 0 | -84 | 10,8 | undefined | undefined | undefined
test_04_02_19 | pycomarduino | 0058924AB98D5AD4 | 1 | 238 | WzNdIEQyMC8wNS8xOCB0MTI6MDAgVzAwMDAgVDAwMDAgPyAxICAgAA== | [3] D20/05/18 t12:00 W0000 T0000 ? 1 | 2020-06-17T10:35:11.4977009Z | 867,9 | LORA | SF7BW125 | 4/5 | undefined | eui-b827ebfffef74e1a | 304635756 | 7 | -84 | 10 | undefined | undefined | undefined
test_04_02_19 | pycomarduino | 0058924AB98D5AD4 | 1 | 239 | WzRdIEQyMC8wNS8xOCB0MTI6MDAgVzAwMDAgVDAwMDAgPyAxICAgAA== | [4] D20/05/18 t12:00 W0000 T0000 ? 1 | 2020-06-17T10:36:08.012828726Z | 868,3 | LORA | SF7BW125 | 4/5 | undefined | eui-fcc23dfffe0b696a | 1270678755 | 1 | -108 | -6,8 | undefined | undefined | undefined | eui-b827ebfffef74e1a | 361157323 | 1 | -79 | 9,5 | undefined | undefined | undefined
test_04_02_19 | pycomarduino | 0058924AB98D5AD4 | 1 | 240 | WzVdIEQyMC8wNS8xOCB0MTI6MDAgVzAwMDAgVDAwMDAgPyAxICAgAA== | [5] D20/05/18 t12:00 W0000 T0000 ? 1 | 2020-06-17T10:37:21.956338454Z | 868,5 | LORA | SF7BW125 | 4/5 | undefined | eui-b827ebfffef74e1a | 434988283 | 2 | -81 | 7,5 | undefined | undefined | undefined
test_04_02_19 | pycomarduino | 0058924AB98D5AD4 | 1 | 241 | WzJdIEQyMC8wNS8xOCB0MTI6MDAgVzAwMDAgVDAwMDAgPyAxICAgAA== | [2] D20/05/18 t12:00 W0000 T0000 ? 1 | 2020-06-17T10:54:06.86015397Z | 867,1 | LORA | SF7BW125 | 4/5 | undefined | eui-fcc23dfffe0a9698 | 2351568187 | 3 | -115 | -6,8 | undefined | undefined | undefined | eui-fcc23dfffe0b696a | 2349521259 | 3 | -114 | 0,8 | undefined | undefined | undefined | eui-b827ebfffef74e1a | 1440000299 | 3 | -85 | 9 | undefined | undefined | undefined
test_04_02_19 | pycomarduino | 0058924AB98D5AD4 | 1 | 242 | WzNdIEQyMC8wNS8xOCB0MTI6MDAgVzAwMDAgVDAwMDAgPyAxICAgAA== | [3] D20/05/18 t12:00 W0000 T0000 ? 1 | 2020-06-17T10:55:11.491457321Z | 868,1 | LORA | SF7BW125 | 4/5 | undefined | eui-b827ebfffef74e1a | 1504632067 | 0 | -83 | 10 | undefined | undefined | undefined
test_04_02_19 | pycomarduino | 0058924AB98D5AD4 | 1 | 243 | WzRdIEQyMC8wNS8xOCB0MTI6MDAgVzAwMDAgVDAwMDAgPyAxICAgAA== | [4] D20/05/18 t12:00 W0000 T0000 ? 1 | 2020-06-17T10:56:08.015823478Z | 868,3 | LORA | SF7BW125 | 4/5 | undefined | eui-b827ebfffef74e1a | 1561156435 | 1 | -79 | 9,2 | undefined | undefined | undefined
test_04_02_19 | pycomarduino | 0058924AB98D5AD4 | 1 | 244 | WzVdIEQyMC8wNS8xOCB0MTI6MDAgVzAwMDAgVDAwMDAgPyAxICAgAA== | [5] D20/05/18 t12:00 W0000 T0000 ? 1 | 2020-06-17T10:57:21.84913128Z | 867,3 | LORA | SF7BW125 | 4/5 | undefined | eui-fcc23dfffe0b696a | 2544509443 | 4 | -113 | 1 | undefined | undefined | undefined | eui-b827ebfffef74e1a | 1634988571 | 4 | -85 | 9,8 | undefined | undefined | undefined
test_04_02_19 | pycomarduino | 0058924AB98D5AD4 | 1 | 245 | WzJdIEQyMC8wNS8xOCB0MTI6MDAgVzAwMDAgVDAwMDAgPyAxICAgAA== | [2] D20/05/18 t12:00 W0000 T0000 ? 1 | 2020-06-17T11:14:06.865631789Z | 868,5 | LORA | SF7BW125 | 4/5 | undefined | eui-fcc23dfffe0b696a | 3549525307 | 2 | -112 | -0,2 | undefined | undefined | undefined | eui-b827ebfffef74e1a | 2640004851 | 2 | -81 | 8,2 | undefined | undefined | undefined
test_04_02_19 | pycomarduino | 0058924AB98D5AD4 | 1 | 246 | WzNdIEQyMC8wNS8xOCB0MTI6MDAgVzAwMDAgVDAwMDAgPyAxICAgAA== | [3] D20/05/18 t12:00 W0000 T0000 ? 1 | 2020-06-17T11:15:11.486448712Z | 867,5 | LORA | SF7BW125 | 4/5 | undefined | eui-fcc23dfffe0b696a | 3614150860 | 5 | -114 | -6 | undefined | undefined | undefined | eui-b827ebfffef74e1a | 2704630428 | 5 | -84 | 7,5 | undefined | undefined | undefined
test_04_02_19 | pycomarduino | 0058924AB98D5AD4 | 1 | 247 | WzRdIEQyMC8wNS8xOCB0MTI6MDAgVzAwMDAgVDAwMDAgPyAxICAgAA== | [4] D20/05/18 t12:00 W0000 T0000 ? 1 | 2020-06-17T11:16:08.017679951Z | 868,1 | LORA | SF7BW125 | 4/5 | undefined | eui-fcc23dfffe0b696a | 3670678067 | 0 | -116 | -2 | undefined | undefined | undefined | eui-b827ebfffef74e1a | 2761157659 | 0 | -83 | 9,2 | undefined | undefined | undefined
test_04_02_19 | pycomarduino | 0058924AB98D5AD4 | 1 | 248 | WzVdIEQyMC8wNS8xOCB0MTI6MDAgVzAwMDAgVDAwMDAgPyAxICAgAA== | [5] D20/05/18 t12:00 W0000 T0000 ? 1 | 2020-06-17T11:17:22.157333124Z | 868,3 | LORA | SF7BW125 | 4/5 | undefined | eui-b827ebfffef74e1a | 2834990995 | 1 | -81 | 10,2 | undefined | undefined | undefined
test_04_02_19 | pycomarduino | 0058924AB98D5AD4 | 1 | 249 | WzJdIEQyMC8wNS8xOCB0MTI6MDAgVzAwMDAgVDAwMDAgPyAxICAgAA== | [2] D20/05/18 t12:00 W0000 T0000 ? 1 | 2020-06-17T11:34:06.863296441Z | 867,7 | LORA | SF7BW125 | 4/5 | undefined | eui-fcc23dfffe0b696a | 454559828 | 6 | -115 | -4 | undefined | undefined | undefined | eui-b827ebfffef74e1a | 3840007196 | 6 | -83 | 10 | undefined | undefined | undefined
test_04_02_19 | pycomarduino | 0058924AB98D5AD4 | 1 | 250 | WzNdIEQyMC8wNS8xOCB0MTI6MDAgVzAwMDAgVDAwMDAgPyAxICAgAA== | [3] D20/05/18 t12:00 W0000 T0000 ? 1 | 2020-06-17T11:35:11.483238839Z | 868,5 | LORA | SF7BW125 | 4/5 | undefined | eui-b827ebfffef74e1a | 3904626851 | 2 | -79 | 8,2 | undefined | undefined | undefined
test_04_02_19 | pycomarduino | 0058924AB98D5AD4 | 1 | 251 | WzRdIEQyMC8wNS8xOCB0MTI6MDAgVzAwMDAgVDAwMDAgPyAxICAgAA== | [4] D20/05/18 t12:00 W0000 T0000 ? 1 | 2020-06-17T11:36:08.011692543Z | 868,1 | LORA | SF7BW125 | 4/5 | undefined | eui-fcc23dfffe0b696a | 575709379 | 0 | -112 | 1,8 | undefined | undefined | undefined | eui-b827ebfffef74e1a | 3961156795 | 0 | -84 | 10 | undefined | undefined | undefined
test_04_02_19 | pycomarduino | 0058924AB98D5AD4 | 1 | 252 | WzVdIEQyMC8wNS8xOCB0MTI6MDAgVzAwMDAgVDAwMDAgPyAxICAgAA== | [5] D20/05/18 t12:00 W0000 T0000 ? 1 | 2020-06-17T11:37:21.861671996Z | 867,9 | LORA | SF7BW125 | 4/5 | undefined | eui-fcc23dfffe0b696a | 649543916 | 7 | -116 | -1,8 | undefined | undefined | undefined | eui-b827ebfffef74e1a | 4034991364 | 7 | -84 | 9,8 | undefined | undefined | undefined
test_04_02_19 | pycomarduino | 0058924AB98D5AD4 | 1 | 253 | WzJdIEQyMC8wNS8xOCB0MTI6MDAgVzAwMDAgVDAwMDAgPyAxICAgAA== | [2] D20/05/18 t12:00 W0000 T0000 ? 1 | 2020-06-17T11:54:06.888525379Z | 868,3 | LORA | SF7BW125 | 4/5 | undefined | eui-b827ebfffef74e1a | 745044363 | 1 | -81 | 9 | undefined | undefined | undefined
test_04_02_19 | pycomarduino | 0058924AB98D5AD4 | 1 | 254 | WzNdIEQyMC8wNS8xOCB0MTI6MDAgVzAwMDAgVDAwMDAgPyAxICAgAA== | [3] D20/05/18 t12:00 W0000 T0000 ? 1 | 2020-06-17T11:55:11.480741636Z | 867,1 | LORA | SF7BW125 | 4/5 | undefined | eui-fcc23dfffe0b696a | 1719177371 | 3 | -115 | 2,5 | undefined | undefined | undefined | eui-b827ebfffef74e1a | 809657987 | 3 | -87 | 10,8 | undefined | undefined | undefined
test_04_02_19 | pycomarduino | 0058924AB98D5AD4 | 1 | 255 | WzRdIEQyMC8wNS8xOCB0MTI6MDAgVzAwMDAgVDAwMDAgPyAxICAgAA== | [4] D20/05/18 t12:00 W0000 T0000 ? 1 | 2020-06-17T11:56:08.017076331Z | 868,5 | LORA | SF7BW125 | 4/5 | undefined | eui-fcc23dfffe0b696a | 1775710187 | 2 | -112 | -0,5 | undefined | undefined | undefined | eui-b827ebfffef74e1a | 866190827 | 2 | -83 | 7,5 | undefined | undefined | undefined
test_04_02_19 | pycomarduino | 0058924AB98D5AD4 | 1 | 256 | WzVdIEQyMC8wNS8xOCB0MTI6MDAgVzAwMDAgVDAwMDAgPyAxICAgAA== | [5] D20/05/18 t12:00 W0000 T0000 ? 1 | 2020-06-17T11:57:21.851189545Z | 868,1 | LORA | SF7BW125 | 4/5 | undefined | eui-fcc23dfffe0b696a | 1849545779 | 0 | -111 | -0,5 | undefined | undefined | undefined | eui-b827ebfffef74e1a | 940026443 | 0 | -83 | 10 | undefined | undefined | undefined
test_04_02_19 | pycomarduino | 0058924AB98D5AD4 | 1 | 257 | WzJdIEQyMC8wNS8xOCB0MTI6MDAgVzAwMDAgVDAwMDAgPyAxICAgAA== | [2] D20/05/18 t12:00 W0000 T0000 ? 1 | 2020-06-17T12:14:06.870232154Z | 867,3 | LORA | SF7BW125 | 4/5 | undefined | eui-fcc23dfffe0b696a | 2854565755 | 4 | -113 | -0,2 | undefined | undefined | undefined | eui-b827ebfffef74e1a | 1945046811 | 4 | -89 | 9,5 | undefined | undefined | undefined
test_04_02_19 | pycomarduino | 0058924AB98D5AD4 | 1 | 258 | WzNdIEQyMC8wNS8xOCB0MTI6MDAgVzAwMDAgVDAwMDAgPyAxICAgAA== | [3] D20/05/18 t12:00 W0000 T0000 ? 1 | 2020-06-17T12:15:11.482781824Z | 868,3 | LORA | SF7BW125 | 4/5 | undefined | eui-b827ebfffef74e1a | 2009654323 | 1 | -81 | 9,2 | undefined | undefined | undefined
test_04_02_19 | pycomarduino | 0058924AB98D5AD4 | 1 | 259 | WzRdIEQyMC8wNS8xOCB0MTI6MDAgVzAwMDAgVDAwMDAgPyAxICAgAA== | [4] D20/05/18 t12:00 W0000 T0000 ? 1 | 2020-06-17T12:16:08.01019398Z | 868,5 | LORA | SF7BW125 | 4/5 | undefined | eui-fcc23dfffe0b696a | 2975708867 | 2 | -112 | -2,2 | undefined | undefined | undefined | eui-b827ebfffef74e1a | 2066189971 | 2 | -79 | 8,2 | undefined | undefined | undefined
test_04_02_19 | pycomarduino | 0058924AB98D5AD4 | 1 | 260 | WzVdIEQyMC8wNS8xOCB0MTI6MDAgVzAwMDAgVDAwMDAgPyAxICAgAA== | [5] D20/05/18 t12:00 W0000 T0000 ? 1 | 2020-06-17T12:17:21.854535246Z | 867,5 | LORA | SF7BW125 | 4/5 | undefined | eui-fcc23dfffe0b696a | 3049545740 | 5 | -115 | -2 | undefined | undefined | undefined | eui-b827ebfffef74e1a | 2140026876 | 5 | -85 | 7,8 | undefined | undefined | undefined
test_04_02_19 | pycomarduino | 0058924AB98D5AD4 | 1 | 261 | WzJdIEQyMC8wNS8xOCB0MTI6MDAgVzAwMDAgVDAwMDAgPyAxICAgAA== | [2] D20/05/18 t12:00 W0000 T0000 ? 1 | 2020-06-17T12:34:06.875711952Z | 868,1 | LORA | SF7BW125 | 4/5 | undefined | eui-fcc23dfffe0b696a | 4054569635 | 0 | -116 | -2,5 | undefined | undefined | undefined | eui-b827ebfffef74e1a | 3145051179 | 0 | -80 | 9 | undefined | undefined | undefined
test_04_02_19 | pycomarduino | 0058924AB98D5AD4 | 1 | 262 | WzNdIEQyMC8wNS8xOCB0MTI6MDAgVzAwMDAgVDAwMDAgPyAxICAgAA== | [3] D20/05/18 t12:00 W0000 T0000 ? 1 | 2020-06-17T12:35:11.475128102Z | 867,7 | LORA | SF7BW125 | 4/5 | undefined | eui-fcc23dfffe0b696a | 4119171212 | 6 | -116 | -5,5 | undefined | undefined | undefined | eui-b827ebfffef74e1a | 3209652788 | 6 | -84 | 9,5 | undefined | undefined | undefined
test_04_02_19 | pycomarduino | 0058924AB98D5AD4 | 1 | 263 | WzRdIEQyMC8wNS8xOCB0MTI6MDAgVzAwMDAgVDAwMDAgPyAxICAgAA== | [4] D20/05/18 t12:00 W0000 T0000 ? 1 | 2020-06-17T12:36:08.017121178Z | 868,3 | LORA | SF7BW125 | 4/5 | undefined | eui-fcc23dfffe0b696a | 4175709659 | 1 | -112 | -2,8 | undefined | undefined | undefined | eui-b827ebfffef74e1a | 3266191259 | 1 | -83 | 10,8 | undefined | undefined | undefined
test_04_02_19 | pycomarduino | 0058924AB98D5AD4 | 1 | 264 | WzVdIEQyMC8wNS8xOCB0MTI6MDAgVzAwMDAgVDAwMDAgPyAxICAgAA== | [5] D20/05/18 t12:00 W0000 T0000 ? 1 | 2020-06-17T12:37:21.856786297Z | 868,5 | LORA | SF7BW125 | 4/5 | undefined | eui-fcc23dfffe0b696a | 4249547787 | 2 | -113 | -0,5 | undefined | undefined | undefined | eui-b827ebfffef74e1a | 3340029411 | 2 | -83 | 7,2 | undefined | undefined | undefined
test_04_02_19 | pycomarduino | 0058924AB98D5AD4 | 1 | 265 | WzJdIEQyMC8wNS8xOCB0MTI6MDAgVzAwMDAgVDAwMDAgPyAxICAgAA== | [2] D20/05/18 t12:00 W0000 T0000 ? 1 | 2020-06-17T12:54:06.880582824Z | 867,9 | LORA | SF7BW125 | 4/5 | undefined | eui-b827ebfffef74e1a | 50086404 | 7 | -84 | 10,5 | undefined | undefined | undefined
test_04_02_19 | pycomarduino | 0058924AB98D5AD4 | 1 | 266 | WzNdIEQyMC8wNS8xOCB0MTI6MDAgVzAwMDAgVDAwMDAgPyAxICAgAA== | [3] D20/05/18 t12:00 W0000 T0000 ? 1 | 2020-06-17T12:55:11.472401296Z | 868,1 | LORA | SF7BW125 | 4/5 | undefined | eui-fcc23dfffe0b696a | 1024199947 | 0 | -115 | -0,8 | undefined | undefined | undefined | eui-b827ebfffef74e1a | 114681987 | 0 | -83 | 9,5 | undefined | undefined | undefined
test_04_02_19 | pycomarduino | 0058924AB98D5AD4 | 1 | 267 | WzRdIEQyMC8wNS8xOCB0MTI6MDAgVzAwMDAgVDAwMDAgPyAxICAgAA== | [4] D20/05/18 t12:00 W0000 T0000 ? 1 | 2020-06-17T12:56:08.014826482Z | 868,3 | LORA | SF7BW125 | 4/5 | undefined | eui-fcc23dfffe0b696a | 1080741283 | 1 | -113 | -8 | undefined | undefined | undefined | eui-b827ebfffef74e1a | 171223339 | 1 | -80 | 9 | undefined | undefined | undefined
test_04_02_19 | pycomarduino | 0058924AB98D5AD4 | 1 | 268 | WzVdIEQyMC8wNS8xOCB0MTI6MDAgVzAwMDAgVDAwMDAgPyAxICAgAA== | [5] D20/05/18 t12:00 W0000 T0000 ? 1 | 2020-06-17T12:57:21.859136946Z | 867,1 | LORA | SF7BW125 | 4/5 | undefined | eui-fcc23dfffe0b696a | 1154580355 | 3 | -117 | -2,8 | undefined | undefined | undefined | eui-b827ebfffef74e1a | 245062443 | 3 | -89 | 10,8 | undefined | undefined | undefined
test_04_02_19 | pycomarduino | 0058924AB98D5AD4 | 1 | 269 | WzJdIEQyMC8wNS8xOCB0MTI6MDAgVzAwMDAgVDAwMDAgPyAxICAgAA== | [2] D20/05/18 t12:00 W0000 T0000 ? 1 | 2020-06-17T13:14:06.885310828Z | 868,5 | LORA | SF7BW125 | 4/5 | undefined | eui-fcc23dfffe0b696a | 2159608459 | 2 | -113 | -1,8 | undefined | undefined | undefined | eui-b827ebfffef74e1a | 1250090947 | 2 | -81 | 7 | undefined | undefined | undefined
test_04_02_19 | pycomarduino | 0058924AB98D5AD4 | 1 | 270 | WzNdIEQyMC8wNS8xOCB0MTI6MDAgVzAwMDAgVDAwMDAgPyAxICAgAA== | [3] D20/05/18 t12:00 W0000 T0000 ? 1 | 2020-06-17T13:15:11.477328507Z | 867,3 | LORA | SF7BW125 | 4/5 | undefined | eui-fcc23dfffe0a9698 | 2226242795 | 4 | -116 | -7 | undefined | undefined | undefined | eui-fcc23dfffe0b696a | 2224198211 | 4 | -112 | 2,2 | undefined | undefined | undefined | eui-b827ebfffef74e1a | 1314680731 | 4 | -84 | 9 | undefined | undefined | undefined
test_04_02_19 | pycomarduino | 0058924AB98D5AD4 | 1 | 271 | WzRdIEQyMC8wNS8xOCB0MTI6MDAgVzAwMDAgVDAwMDAgPyAxICAgAA== | [4] D20/05/18 t12:00 W0000 T0000 ? 1 | 2020-06-17T13:16:08.012094419Z | 868,1 | LORA | SF7BW125 | 4/5 | undefined | eui-fcc23dfffe0b696a | 2280742363 | 0 | -115 | -0,2 | undefined | undefined | undefined | eui-b827ebfffef74e1a | 1371224899 | 0 | -84 | 11 | undefined | undefined | undefined
test_04_02_19 | pycomarduino | 0058924AB98D5AD4 | 1 | 272 | WzVdIEQyMC8wNS8xOCB0MTI6MDAgVzAwMDAgVDAwMDAgPyAxICAgAA== | [5] D20/05/18 t12:00 W0000 T0000 ? 1 | 2020-06-17T13:17:21.856037832Z | 868,3 | LORA | SF7BW125 | 4/5 | undefined | eui-b827ebfffef74e1a | 1445065003 | 1 | -81 | 9,5 | undefined | undefined | undefined
test_04_02_19 | pycomarduino | 0058924AB98D5AD4 | 1 | 273 | WzJdIEQyMC8wNS8xOCB0MTI6MDAgVzAwMDAgVDAwMDAgPyAxICAgAA== | [2] D20/05/18 t12:00 W0000 T0000 ? 1 | 2020-06-17T13:34:06.884380264Z | 867,5 | LORA | SF7BW125 | 4/5 | undefined | eui-fcc23dfffe0b696a | 3359610484 | 5 | -117 | -5,8 | undefined | undefined | undefined | eui-b827ebfffef74e1a | 2450093476 | 5 | -84 | 7,8 | undefined | undefined | undefined
test_04_02_19 | pycomarduino | 0058924AB98D5AD4 | 1 | 274 | WzNdIEQyMC8wNS8xOCB0MTI6MDAgVzAwMDAgVDAwMDAgPyAxICAgAA== | [3] D20/05/18 t12:00 W0000 T0000 ? 1 | 2020-06-17T13:35:11.469621928Z | 868,5 | LORA | SF7BW125 | 4/5 | undefined | eui-fcc23dfffe0b696a | 3424194323 | 2 | -113 | -0,2 | undefined | undefined | undefined | eui-b827ebfffef74e1a | 2514677347 | 2 | -83 | 7 | undefined | undefined | undefined
test_04_02_19 | pycomarduino | 0058924AB98D5AD4 | 1 | 275 | WzRdIEQyMC8wNS8xOCB0MTI6MDAgVzAwMDAgVDAwMDAgPyAxICAgAA== | [4] D20/05/18 t12:00 W0000 T0000 ? 1 | 2020-06-17T13:36:08.021946635Z | 868,1 | LORA | SF7BW125 | 4/5 | undefined | eui-b827ebfffef74e1a | 2571224379 | 0 | -82 | 8,8 | undefined | undefined | undefined
test_04_02_19 | pycomarduino | 0058924AB98D5AD4 | 1 | 276 | WzVdIEQyMC8wNS8xOCB0MTI6MDAgVzAwMDAgVDAwMDAgPyAxICAgAA== | [5] D20/05/18 t12:00 W0000 T0000 ? 1 | 2020-06-17T13:37:21.854890017Z | 867,7 | LORA | SF7BW125 | 4/5 | undefined | eui-b827ebfffef74e1a | 2645065612 | 6 | -83 | 10 | undefined | undefined | undefined
test_04_02_19 | pycomarduino | 0058924AB98D5AD4 | 1 | 277 | WzJdIEQyMC8wNS8xOCB0MTI6MDAgVzAwMDAgVDAwMDAgPyAxICAgAA== | [2] D20/05/18 t12:00 W0000 T0000 ? 1 | 2020-06-17T13:54:06.894706245Z | 868,3 | LORA | SF7BW125 | 4/5 | undefined | eui-fcc23dfffe0b696a | 264647363 | 1 | -113 | -1 | undefined | undefined | undefined | eui-b827ebfffef74e1a | 3650098179 | 1 | -83 | 9,5 | undefined | undefined | undefined
test_04_02_19 | pycomarduino | 0058924AB98D5AD4 | 1 | 278 | WzNdIEQyMC8wNS8xOCB0MTI6MDAgVzAwMDAgVDAwMDAgPyAxICAgAA== | [3] D20/05/18 t12:00 W0000 T0000 ? 1 | 2020-06-17T13:55:11.481313795Z | 867,9 | LORA | SF7BW125 | 4/5 | undefined | eui-fcc23dfffe0b696a | 329225372 | 7 | -117 | -3 | undefined | undefined | undefined | eui-b827ebfffef74e1a | 3714676220 | 7 | -87 | 10,2 | undefined | undefined | undefined
test_04_02_19 | pycomarduino | 0058924AB98D5AD4 | 1 | 279 | WzRdIEQyMC8wNS8xOCB0MTI6MDAgVzAwMDAgVDAwMDAgPyAxICAgAA== | [4] D20/05/18 t12:00 W0000 T0000 ? 1 | 2020-06-17T13:56:08.014073559Z | 868,5 | LORA | SF7BW125 | 4/5 | undefined | eui-fcc23dfffe0b696a | 385775123 | 2 | -110 | -3,5 | undefined | undefined | undefined | eui-b827ebfffef74e1a | 3771225995 | 2 | -83 | 7,5 | undefined | undefined | undefined
test_04_02_19 | pycomarduino | 0058924AB98D5AD4 | 1 | 280 | WzVdIEQyMC8wNS8xOCB0MTI6MDAgVzAwMDAgVDAwMDAgPyAxICAgAA== | [5] D20/05/18 t12:00 W0000 T0000 ? 1 | 2020-06-17T13:57:21.858201101Z | 868,1 | LORA | SF7BW125 | 4/5 | undefined | eui-b827ebfffef74e1a | 3845068411 | 0 | -84 | 10 | undefined | undefined | undefined
test_04_02_19 | pycomarduino | 0058924AB98D5AD4 | 1 | 281 | WzJdIEQyMC8wNS8xOCB0MTI6MDAgVzAwMDAgVDAwMDAgPyAxICAgAA== | [2] D20/05/18 t12:00 W0000 T0000 ? 1 | 2020-06-17T14:14:06.892794994Z | 867,1 | LORA | SF7BW125 | 4/5 | undefined | eui-fcc23dfffe0a9698 | 1466693107 | 3 | -117 | -6 | undefined | undefined | undefined | eui-fcc23dfffe0b696a | 1464649467 | 3 | -115 | 1,5 | undefined | undefined | undefined | eui-b827ebfffef74e1a | 555133515 | 3 | -95 | 8,8 | undefined | undefined | undefined
test_04_02_19 | pycomarduino | 0058924AB98D5AD4 | 1 | 282 | WzNdIEQyMC8wNS8xOCB0MTI6MDAgVzAwMDAgVDAwMDAgPyAxICAgAA== | [3] D20/05/18 t12:00 W0000 T0000 ? 1 | 2020-06-17T14:15:11.46805475Z | 868,3 | LORA | SF7BW125 | 4/5 | undefined | eui-fcc23dfffe0b696a | 1529221675 | 1 | -112 | -5,2 | undefined | undefined | undefined | eui-b827ebfffef74e1a | 619705755 | 1 | -83 | 9,8 | undefined | undefined | undefined
test_04_02_19 | pycomarduino | 0058924AB98D5AD4 | 1 | 283 | WzRdIEQyMC8wNS8xOCB0MTI6MDAgVzAwMDAgVDAwMDAgPyAxICAgAA== | [4] D20/05/18 t12:00 W0000 T0000 ? 1 | 2020-06-17T14:16:08.023518008Z | 868,5 | LORA | SF7BW125 | 4/5 | undefined | eui-fcc23dfffe0b696a | 1585774339 | 2 | -115 | -3,2 | undefined | undefined | undefined | eui-b827ebfffef74e1a | 676258443 | 2 | -79 | 8 | undefined | undefined | undefined
test_04_02_19 | pycomarduino | 0058924AB98D5AD4 | 1 | 284 | WzVdIEQyMC8wNS8xOCB0MTI6MDAgVzAwMDAgVDAwMDAgPyAxICAgAA== | [5] D20/05/18 t12:00 W0000 T0000 ? 1 | 2020-06-17T14:17:21.882677097Z | 867,3 | LORA | SF7BW125 | 4/5 | undefined | eui-fcc23dfffe0b696a | 1659617723 | 4 | -112 | -0,8 | undefined | undefined | undefined | eui-b827ebfffef74e1a | 750101859 | 4 | -84 | 10,5 | undefined | undefined | undefined
test_04_02_19 | pycomarduino | 0058924AB98D5AD4 | 1 | 285 | WzJdIEQyMC8wNS8xOCB0MTI6MDAgVzAwMDAgVDAwMDAgPyAxICAgAA== | [2] D20/05/18 t12:00 W0000 T0000 ? 1 | 2020-06-17T14:34:06.898551954Z | 868,1 | LORA | SF7BW125 | 4/5 | undefined | eui-fcc23dfffe0b696a | 2664653771 | 0 | -113 | -2,5 | undefined | undefined | undefined | eui-b827ebfffef74e1a | 1755138339 | 0 | -83 | 9,2 | undefined | undefined | undefined
test_04_02_19 | pycomarduino | 0058924AB98D5AD4 | 1 | 286 | WzNdIEQyMC8wNS8xOCB0MTI6MDAgVzAwMDAgVDAwMDAgPyAxICAgAA== | [3] D20/05/18 t12:00 W0000 T0000 ? 1 | 2020-06-17T14:35:11.462096309Z | 867,5 | LORA | SF7BW125 | 4/5 | undefined | eui-fcc23dfffe0b696a | 2729220188 | 5 | -114 | -3,2 | undefined | undefined | undefined | eui-b827ebfffef74e1a | 1819704788 | 5 | -87 | 7,2 | undefined | undefined | undefined
test_04_02_19 | pycomarduino | 0058924AB98D5AD4 | 1 | 287 | WzRdIEQyMC8wNS8xOCB0MTI6MDAgVzAwMDAgVDAwMDAgPyAxICAgAA== | [4] D20/05/18 t12:00 W0000 T0000 ? 1 | 2020-06-17T14:36:08.019999559Z | 868,3 | LORA | SF7BW125 | 4/5 | undefined | eui-fcc23dfffe0b696a | 2785775723 | 1 | -109 | -5 | undefined | undefined | undefined | eui-b827ebfffef74e1a | 1876260347 | 1 | -80 | 9,2 | undefined | undefined | undefined
test_04_02_19 | pycomarduino | 0058924AB98D5AD4 | 1 | 288 | WzVdIEQyMC8wNS8xOCB0MTI6MDAgVzAwMDAgVDAwMDAgPyAxICAgAA== | [5] D20/05/18 t12:00 W0000 T0000 ? 1 | 2020-06-17T14:37:21.86504066Z | 868,5 | LORA | SF7BW125 | 4/5 | undefined | eui-fcc23dfffe0b696a | 2859620187 | 2 | -111 | -1,8 | undefined | undefined | undefined | eui-b827ebfffef74e1a | 1950104843 | 2 | -81 | 7,5 | undefined | undefined | undefined
test_04_02_19 | pycomarduino | 0058924AB98D5AD4 | 1 | 289 | WzJdIEQyMC8wNS8xOCB0MTI6MDAgVzAwMDAgVDAwMDAgPyAxICAgAA== | [2] D20/05/18 t12:00 W0000 T0000 ? 1 | 2020-06-17T14:54:06.900721655Z | 867,7 | LORA | SF7BW125 | 4/5 | undefined | eui-fcc23dfffe0b696a | 3864655948 | 6 | -116 | -5,5 | undefined | undefined | undefined | eui-b827ebfffef74e1a | 2955141044 | 6 | -85 | 9,2 | undefined | undefined | undefined
test_04_02_19 | pycomarduino | 0058924AB98D5AD4 | 1 | 290 | WzNdIEQyMC8wNS8xOCB0MTI6MDAgVzAwMDAgVDAwMDAgPyAxICAgAA== | [3] D20/05/18 t12:00 W0000 T0000 ? 1 | 2020-06-17T14:55:11.458354715Z | 868,1 | LORA | SF7BW125 | 4/5 | undefined | eui-b827ebfffef74e1a | 3019701795 | 0 | -83 | 9,5 | undefined | undefined | undefined
test_04_02_19 | pycomarduino | 0058924AB98D5AD4 | 1 | 291 | WzRdIEQyMC8wNS8xOCB0MTI6MDAgVzAwMDAgVDAwMDAgPyAxICAgAA== | [4] D20/05/18 t12:00 W0000 T0000 ? 1 | 2020-06-17T14:56:08.020529962Z | 868,3 | LORA | SF7BW125 | 4/5 | undefined | eui-fcc23dfffe0b696a | 3985775171 | 1 | -111 | -3 | undefined | undefined | undefined | eui-b827ebfffef74e1a | 3076260315 | 1 | -81 | 9,2 | undefined | undefined | undefined
test_04_02_19 | pycomarduino | 0058924AB98D5AD4 | 1 | 292 | WzVdIEQyMC8wNS8xOCB0MTI6MDAgVzAwMDAgVDAwMDAgPyAxICAgAA== | [5] D20/05/18 t12:00 W0000 T0000 ? 1 | 2020-06-17T14:57:21.860730085Z | 867,9 | LORA | SF7BW125 | 4/5 | undefined | eui-fcc23dfffe0b696a | 4059620908 | 7 | -118 | -6,2 | undefined | undefined | undefined | eui-b827ebfffef74e1a | 3150106092 | 7 | -83 | 9 | undefined | undefined | undefined
test_04_02_19 | pycomarduino | 0058924AB98D5AD4 | 1 | 293 | WzJdIEQyMC8wNS8xOCB0MTI6MDAgVzAwMDAgVDAwMDAgPyAxICAgAA== | [2] D20/05/18 t12:00 W0000 T0000 ? 1 | 2020-06-17T15:14:06.899623151Z | 868,5 | LORA | SF7BW125 | 4/5 | undefined | eui-fcc23dfffe0b696a | 769692987 | 2 | -117 | -2,2 | undefined | undefined | undefined | eui-b827ebfffef74e1a | 4155145931 | 2 | -83 | 7,8 | undefined | undefined | undefined
test_04_02_19 | pycomarduino | 0058924AB98D5AD4 | 1 | 294 | WzNdIEQyMC8wNS8xOCB0MTI6MDAgVzAwMDAgVDAwMDAgPyAxICAgAA== | [3] D20/05/18 t12:00 W0000 T0000 ? 1 | 2020-06-17T15:15:11.460234955Z | 867,1 | LORA | SF7BW125 | 4/5 | undefined | eui-fcc23dfffe0b696a | 834247971 | 3 | -113 | 1 | undefined | undefined | undefined | eui-b827ebfffef74e1a | 4219700939 | 3 | -89 | 9,2 | undefined | undefined | undefined
test_04_02_19 | pycomarduino | 0058924AB98D5AD4 | 1 | 295 | WzRdIEQyMC8wNS8xOCB0MTI6MDAgVzAwMDAgVDAwMDAgPyAxICAgAA== | [4] D20/05/18 t12:00 W0000 T0000 ? 1 | 2020-06-17T15:16:08.022412789Z | 868,1 | LORA | SF7BW125 | 4/5 | undefined | eui-fcc23dfffe0b696a | 890809387 | 0 | -117 | -1,2 | undefined | undefined | undefined | eui-b827ebfffef74e1a | 4276262387 | 0 | -85 | 10,2 | undefined | undefined | undefined
test_04_02_19 | pycomarduino | 0058924AB98D5AD4 | 1 | 296 | WzVdIEQyMC8wNS8xOCB0MTI6MDAgVzAwMDAgVDAwMDAgPyAxICAgAA== | [5] D20/05/18 t12:00 W0000 T0000 ? 1 | 2020-06-17T15:17:21.877086224Z | 868,3 | LORA | SF7BW125 | 4/5 | undefined | eui-fcc23dfffe0b696a | 964657011 | 1 | -112 | -6 | undefined | undefined | undefined | eui-b827ebfffef74e1a | 55142747 | 1 | -81 | 9,5 | undefined | undefined | undefined
test_04_02_19 | pycomarduino | 0058924AB98D5AD4 | 1 | 297 | WzJdIEQyMC8wNS8xOCB0MTI6MDAgVzAwMDAgVDAwMDAgPyAxICAgAA== | [2] D20/05/18 t12:00 W0000 T0000 ? 1 | 2020-06-17T15:34:06.913061537Z | 867,3 | LORA | SF7BW125 | 4/5 | undefined | eui-fcc23dfffe0a9698 | 1971737715 | 4 | -117 | -6,8 | undefined | undefined | undefined | eui-fcc23dfffe0b696a | 1969695355 | 4 | -112 | 1,5 | undefined | undefined | undefined | eui-b827ebfffef74e1a | 1060181539 | 4 | -85 | 10,8 | undefined | undefined | undefined
test_04_02_19 | pycomarduino | 0058924AB98D5AD4 | 1 | 298 | WzNdIEQyMC8wNS8xOCB0MTI6MDAgVzAwMDAgVDAwMDAgPyAxICAgAA== | [3] D20/05/18 t12:00 W0000 T0000 ? 1 | 2020-06-17T15:35:11.457274241Z | 868,5 | LORA | SF7BW125 | 4/5 | undefined | eui-b827ebfffef74e1a | 1124730939 | 2 | -81 | 7,2 | undefined | undefined | undefined
test_04_02_19 | pycomarduino | 0058924AB98D5AD4 | 1 | 299 | WzRdIEQyMC8wNS8xOCB0MTI6MDAgVzAwMDAgVDAwMDAgPyAxICAgAA== | [4] D20/05/18 t12:00 W0000 T0000 ? 1 | 2020-06-17T15:36:08.040472955Z | 868,1 | LORA | SF7BW125 | 4/5 | undefined | eui-fcc23dfffe0b696a | 2090809003 | 0 | -108 | -5 | undefined | undefined | undefined | eui-b827ebfffef74e1a | 1181295235 | 0 | -82 | 9,5 | undefined | undefined | undefined
test_04_02_19 | pycomarduino | 0058924AB98D5AD4 | 1 | 300 | WzVdIEQyMC8wNS8xOCB0MTI6MDAgVzAwMDAgVDAwMDAgPyAxICAgAA== | [5] D20/05/18 t12:00 W0000 T0000 ? 1 | 2020-06-17T15:37:21.873453268Z | 867,5 | LORA | SF7BW125 | 4/5 | undefined | eui-fcc23dfffe0b696a | 2164660412 | 5 | -115 | -2 | undefined | undefined | undefined | eui-b827ebfffef74e1a | 1255146684 | 5 | -85 | 7,5 | undefined | undefined | undefined
test_04_02_19 | pycomarduino | 0058924AB98D5AD4 | 1 | 301 | WzJdIEQyMC8wNS8xOCB0MTI6MDAgVzAwMDAgVDAwMDAgPyAxICAgAA== | [2] D20/05/18 t12:00 W0000 T0000 ? 1 | 2020-06-17T15:54:06.911612469Z | 868,3 | LORA | SF7BW125 | 4/5 | undefined | eui-b827ebfffef74e1a | 2260186539 | 1 | -79 | 9 | undefined | undefined | undefined
test_04_02_19 | pycomarduino | 0058924AB98D5AD4 | 1 | 302 | WzNdIEQyMC8wNS8xOCB0MTI6MDAgVzAwMDAgVDAwMDAgPyAxICAgAA== | [3] D20/05/18 t12:00 W0000 T0000 ? 1 | 2020-06-17T15:55:11.464877954Z | 867,7 | LORA | SF7BW125 | 4/5 | undefined | eui-fcc23dfffe0b696a | 3234243444 | 6 | -117 | -7,2 | undefined | undefined | undefined | eui-b827ebfffef74e1a | 2324730196 | 6 | -84 | 9 | undefined | undefined | undefined
test_04_02_19 | pycomarduino | 0058924AB98D5AD4 | 1 | 303 | WzRdIEQyMC8wNS8xOCB0MTI6MDAgVzAwMDAgVDAwMDAgPyAxICAgAA== | [4] D20/05/18 t12:00 W0000 T0000 ? 1 | 2020-06-17T15:56:08.021112224Z | 868,5 | LORA | SF7BW125 | 4/5 | undefined | eui-fcc23dfffe0b696a | 3290810691 | 2 | -114 | -4,2 | undefined | undefined | undefined | eui-b827ebfffef74e1a | 2381297467 | 2 | -83 | 7,8 | undefined | undefined | undefined
test_04_02_19 | pycomarduino | 0058924AB98D5AD4 | 1 | 304 | WzVdIEQyMC8wNS8xOCB0MTI6MDAgVzAwMDAgVDAwMDAgPyAxICAgAA== | [5] D20/05/18 t12:00 W0000 T0000 ? 1 | 2020-06-17T15:57:21.901784511Z | 868,1 | LORA | SF7BW125 | 4/5 | undefined | eui-b827ebfffef74e1a | 2455150691 | 0 | -81 | 10,8 | undefined | undefined | undefined
test_04_02_19 | pycomarduino | 0058924AB98D5AD4 | 1 | 305 | WzJdIEQyMC8wNS8xOCB0MTI6MDAgVzAwMDAgVDAwMDAgPyAxICAgAA== | [2] D20/05/18 t12:00 W0000 T0000 ? 1 | 2020-06-17T16:14:06.911273645Z | 867,9 | LORA | SF7BW125 | 4/5 | undefined | eui-fcc23dfffe0b696a | 74734932 | 7 | -118 | -3 | undefined | undefined | undefined | eui-b827ebfffef74e1a | 3460189492 | 7 | -84 | 9,5 | undefined | undefined | undefined
test_04_02_19 | pycomarduino | 0058924AB98D5AD4 | 1 | 306 | WzNdIEQyMC8wNS8xOCB0MTI6MDAgVzAwMDAgVDAwMDAgPyAxICAgAA== | [3] D20/05/18 t12:00 W0000 T0000 ? 1 | 2020-06-17T16:15:11.452130471Z | 868,3 | LORA | SF7BW125 | 4/5 | undefined | eui-b827ebfffef74e1a | 3524727483 | 1 | -80 | 9 | undefined | undefined | undefined
test_04_02_19 | pycomarduino | 0058924AB98D5AD4 | 1 | 307 | WzRdIEQyMC8wNS8xOCB0MTI6MDAgVzAwMDAgVDAwMDAgPyAxICAgAA== | [4] D20/05/18 t12:00 W0000 T0000 ? 1 | 2020-06-17T16:16:08.031234153Z | 868,5 | LORA | SF7BW125 | 4/5 | undefined | eui-b827ebfffef74e1a | 3581297507 | 2 | -82 | 8,2 | undefined | undefined | undefined
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
