ComNets-Bremen/MoleNet/experiments/2024-LoRa_Gateway_for_WUSN/Field_Experiment/Field_experiment_2020_06_18.ods

jsonData.app_id | jsonData.dev_id | jsonData.hardware_serial | jsonData.port | jsonData.counter | jsonData.payload_raw | jsonData.payload_decoded | jsonData.metadata.time | jsonData.metadata.frequency | jsonData.metadata.modulation | jsonData.metadata.data_rate | jsonData.metadata.coding_rate | jsonData.metadata.downlink_url | gateway.gtw_id | gateway.timestamp | gateway.channel | gateway.rssi | gateway.snr | gateway.latitude | gateway.longitude | gateway.altitude | gateway.gtw_id | gateway.timestamp | gateway.channel | gateway.rssi | gateway.snr | gateway.latitude | gateway.longitude | gateway.altitude | gateway.gtw_id | gateway.timestamp | gateway.channel | gateway.rssi | gateway.snr | gateway.latitude | gateway.longitude | gateway.altitude | gateway.gtw_id | gateway.timestamp | gateway.channel | gateway.rssi | gateway.snr | gateway.latitude | gateway.longitude | gateway.altitude
test_04_02_19 | pycomarduino | 0058924AB98D5AD4 | 1 | 0 | TW9pbgAAAAAAAAAAAAAAAAAAAAAAAAAAAAAAAAAAAAAAAAAAAAAAAA== | Moin | 2020-06-18T16:05:23.824984058Z | 867,1 | LORA | SF7BW125 | 4/5 | undefined | eui-fcc23dfffe0b696a | 52272219 | 3 | -112 | -6,2 | undefined | undefined | undefined | eui-fcc23dfffe0a9698 | 54293163 | 3 | -117 | -4,2 | undefined | undefined | undefined | eui-b827ebfffef74e1a | 3437766619 | 3 | -87 | 9,8 | undefined | undefined | undefined
test_04_02_19 | pycomarduino | 0058924AB98D5AD4 | 1 | 1 | WzJdIEQyMC8wNS8xOCB0MTI6MDAgVzAwMDAgVDAwMDAgPyAxICAgAA== | [2] D20/05/18 t12:00 W0000 T0000 ? 1 | 2020-06-18T16:08:11.524216945Z | 868,1 | LORA | SF7BW125 | 4/5 | undefined | eui-fcc23dfffe0b696a | 219962307 | 0 | -115 | -6,8 | undefined | undefined | undefined | eui-b827ebfffef74e1a | 3605456779 | 0 | -85 | 9 | undefined | undefined | undefined
test_04_02_19 | pycomarduino | 0058924AB98D5AD4 | 1 | 2 | WzNdIEQyMC8wNS8xOCB0MTI6MDAgVzAwMDAgVDAwMDAgPyAxICAgAA== | [3] D20/05/18 t12:00 W0000 T0000 ? 1 | 2020-06-18T16:08:42.136853758Z | 867,3 | LORA | SF7BW125 | 4/5 | undefined | eui-b827ebfffef74e1a | 3636071427 | 4 | -87 | 11 | undefined | undefined | undefined
test_04_02_19 | pycomarduino | 0058924AB98D5AD4 | 1 | 3 | WzRdIEQyMC8wNS8xOCB0MTI6MDAgVzAwMDAgVDAwMDAgPyAxICAgAA== | [4] D20/05/18 t12:00 W0000 T0000 ? 1 | 2020-06-18T16:09:27.535488559Z | 868,3 | LORA | SF7BW125 | 4/5 | undefined | eui-b827ebfffef74e1a | 3681479019 | 1 | -85 | 10 | undefined | undefined | undefined
test_04_02_19 | pycomarduino | 0058924AB98D5AD4 | 1 | 4 | WzVdIEQyMC8wNS8xOCB0MTI6MDAgVzAwMDAgVDAwMDAgPyAxICAgAA== | [5] D20/05/18 t12:00 W0000 T0000 ? 1 | 2020-06-18T16:09:54.359383285Z | 868,5 | LORA | SF7BW125 | 4/5 | undefined | eui-fcc23dfffe0b696a | 322806011 | 2 | -112 | -3 | undefined | undefined | undefined | eui-b827ebfffef74e1a | 3708300531 | 2 | -84 | 7,8 | undefined | undefined | undefined
test_04_02_19 | pycomarduino | 0058924AB98D5AD4 | 1 | 5 | WzJdIEQyMC8wNS8xOCB0MTI6MDAgVzAwMDAgVDAwMDAgPyAxICAgAA== | [2] D20/05/18 t12:00 W0000 T0000 ? 1 | 2020-06-18T16:13:11.369715441Z | 868,1 | LORA | SF7BW125 | 4/5 | undefined | eui-b827ebfffef74e1a | 3905313211 | 0 | -85 | 9,5 | undefined | undefined | undefined
test_04_02_19 | pycomarduino | 0058924AB98D5AD4 | 1 | 6 | WzNdIEQyMC8wNS8xOCB0MTI6MDAgVzAwMDAgVDAwMDAgPyAxICAgAA== | [3] D20/05/18 t12:00 W0000 T0000 ? 1 | 2020-06-18T16:13:42.133645316Z | 867,5 | LORA | SF7BW125 | 4/5 | undefined | eui-fcc23dfffe0b696a | 550577444 | 5 | -112 | -7,8 | undefined | undefined | undefined | eui-b827ebfffef74e1a | 3936072068 | 5 | -82 | 7,8 | undefined | undefined | undefined
test_04_02_19 | pycomarduino | 0058924AB98D5AD4 | 1 | 7 | WzRdIEQyMC8wNS8xOCB0MTI6MDAgVzAwMDAgVDAwMDAgPyAxICAgAA== | [4] D20/05/18 t12:00 W0000 T0000 ? 1 | 2020-06-18T16:14:27.544184322Z | 868,3 | LORA | SF7BW125 | 4/5 | undefined | eui-b827ebfffef74e1a | 3981480315 | 1 | -84 | 10,5 | undefined | undefined | undefined
test_04_02_19 | pycomarduino | 0058924AB98D5AD4 | 1 | 8 | WzVdIEQyMC8wNS8xOCB0MTI6MDAgVzAwMDAgVDAwMDAgPyAxICAgAA== | [5] D20/05/18 t12:00 W0000 T0000 ? 1 | 2020-06-18T16:14:54.360509246Z | 868,5 | LORA | SF7BW125 | 4/5 | undefined | eui-b827ebfffef74e1a | 4008302123 | 2 | -82 | 7,5 | undefined | undefined | undefined
test_04_02_19 | pycomarduino | 0058924AB98D5AD4 | 1 | 9 | WzJdIEQyMC8wNS8xOCB0MTI6MDAgVzAwMDAgVDAwMDAgPyAxICAgAA== | [2] D20/05/18 t12:00 W0000 T0000 ? 1 | 2020-06-18T16:18:11.381733006Z | 868,1 | LORA | SF7BW125 | 4/5 | undefined | eui-b827ebfffef74e1a | 4205313291 | 0 | -84 | 9,8 | undefined | undefined | undefined
test_04_02_19 | pycomarduino | 0058924AB98D5AD4 | 1 | 10 | WzNdIEQyMC8wNS8xOCB0MTI6MDAgVzAwMDAgVDAwMDAgPyAxICAgAA== | [3] D20/05/18 t12:00 W0000 T0000 ? 1 | 2020-06-18T16:18:42.141585681Z | 867,7 | LORA | SF7BW125 | 4/5 | undefined | eui-b827ebfffef74e1a | 4236070572 | 6 | -85 | 10 | undefined | undefined | undefined
test_04_02_19 | pycomarduino | 0058924AB98D5AD4 | 1 | 11 | WzRdIEQyMC8wNS8xOCB0MTI6MDAgVzAwMDAgVDAwMDAgPyAxICAgAA== | [4] D20/05/18 t12:00 W0000 T0000 ? 1 | 2020-06-18T16:19:27.564585024Z | 868,3 | LORA | SF7BW125 | 4/5 | undefined | eui-b827ebfffef74e1a | 4281479467 | 1 | -82 | 8,8 | undefined | undefined | undefined
test_04_02_19 | pycomarduino | 0058924AB98D5AD4 | 1 | 12 | WzVdIEQyMC8wNS8xOCB0MTI6MDAgVzAwMDAgVDAwMDAgPyAxICAgAA== | [5] D20/05/18 t12:00 W0000 T0000 ? 1 | 2020-06-18T16:19:54.361880863Z | 868,5 | LORA | SF7BW125 | 4/5 | undefined | eui-fcc23dfffe0b696a | 922806931 | 2 | -112 | -4,8 | undefined | undefined | undefined | eui-b827ebfffef74e1a | 13334411 | 2 | -85 | 7,8 | undefined | undefined | undefined
test_04_02_19 | pycomarduino | 0058924AB98D5AD4 | 1 | 13 | WzJdIEQyMC8wNS8xOCB0MTI6MDAgVzAwMDAgVDAwMDAgPyAxICAgAA== | [2] D20/05/18 t12:00 W0000 T0000 ? 1 | 2020-06-18T16:23:11.384909795Z | 868,1 | LORA | SF7BW125 | 4/5 | undefined | eui-b827ebfffef74e1a | 210346163 | 0 | -85 | 11,2 | undefined | undefined | undefined
test_04_02_19 | pycomarduino | 0058924AB98D5AD4 | 1 | 15 | WzRdIEQyMC8wNS8xOCB0MTI6MDAgVzAwMDAgVDAwMDAgPyAxICAgAA== | [4] D20/05/18 t12:00 W0000 T0000 ? 1 | 2020-06-18T16:24:27.542206685Z | 868,3 | LORA | SF7BW125 | 4/5 | undefined | eui-b827ebfffef74e1a | 286511427 | 1 | -82 | 8,8 | undefined | undefined | undefined
test_04_02_19 | pycomarduino | 0058924AB98D5AD4 | 1 | 16 | WzVdIEQyMC8wNS8xOCB0MTI6MDAgVzAwMDAgVDAwMDAgPyAxICAgAA== | [5] D20/05/18 t12:00 W0000 T0000 ? 1 | 2020-06-18T16:24:54.362409134Z | 868,5 | LORA | SF7BW125 | 4/5 | undefined | eui-fcc23dfffe0b696a | 1222806299 | 2 | -112 | -3 | undefined | undefined | undefined | eui-b827ebfffef74e1a | 313333907 | 2 | -84 | 8,2 | undefined | undefined | undefined
test_04_02_19 | pycomarduino | 0058924AB98D5AD4 | 1 | 17 | WzJdIEQyMC8wNS8xOCB0MTI6MDAgVzAwMDAgVDAwMDAgPyAxICAgAA== | [2] D20/05/18 t12:00 W0000 T0000 ? 1 | 2020-06-18T16:28:11.37214586Z | 868,1 | LORA | SF7BW125 | 4/5 | undefined | eui-fcc23dfffe0b696a | 1419820603 | 0 | -115 | -5,8 | undefined | undefined | undefined | eui-b827ebfffef74e1a | 510348299 | 0 | -89 | 10 | undefined | undefined | undefined
test_04_02_19 | pycomarduino | 0058924AB98D5AD4 | 1 | 18 | WzNdIEQyMC8wNS8xOCB0MTI6MDAgVzAwMDAgVDAwMDAgPyAxICAgAA== | [3] D20/05/18 t12:00 W0000 T0000 ? 1 | 2020-06-18T16:28:42.127415715Z | 867,1 | LORA | SF7BW125 | 4/5 | undefined | eui-fcc23dfffe0b696a | 1450574707 | 3 | -113 | -4,8 | undefined | undefined | undefined | eui-b827ebfffef74e1a | 541102411 | 3 | -89 | 9,5 | undefined | undefined | undefined
test_04_02_19 | pycomarduino | 0058924AB98D5AD4 | 1 | 19 | WzRdIEQyMC8wNS8xOCB0MTI6MDAgVzAwMDAgVDAwMDAgPyAxICAgAA== | [4] D20/05/18 t12:00 W0000 T0000 ? 1 | 2020-06-18T16:29:27.539182453Z | 868,3 | LORA | SF7BW125 | 4/5 | undefined | eui-b827ebfffef74e1a | 586512715 | 1 | -88 | 9,2 | undefined | undefined | undefined
test_04_02_19 | pycomarduino | 0058924AB98D5AD4 | 1 | 20 | WzVdIEQyMC8wNS8xOCB0MTI6MDAgVzAwMDAgVDAwMDAgPyAxICAgAA== | [5] D20/05/18 t12:00 W0000 T0000 ? 1 | 2020-06-18T16:29:54.410431723Z | 868,5 | LORA | SF7BW125 | 4/5 | undefined | eui-b827ebfffef74e1a | 613335451 | 2 | -84 | 7,8 | undefined | undefined | undefined
test_04_02_19 | pycomarduino | 0058924AB98D5AD4 | 1 | 21 | WzJdIEQyMC8wNS8xOCB0MTI6MDAgVzAwMDAgVDAwMDAgPyAxICAgAA== | [2] D20/05/18 t12:00 W0000 T0000 ? 1 | 2020-06-18T16:33:11.37436543Z | 868,1 | LORA | SF7BW125 | 4/5 | undefined | eui-fcc23dfffe0b696a | 1719820731 | 0 | -111 | -5,5 | undefined | undefined | undefined | eui-b827ebfffef74e1a | 810348547 | 0 | -88 | 10 | undefined | undefined | undefined
test_04_02_19 | pycomarduino | 0058924AB98D5AD4 | 1 | 22 | WzNdIEQyMC8wNS8xOCB0MTI6MDAgVzAwMDAgVDAwMDAgPyAxICAgAA== | [3] D20/05/18 t12:00 W0000 T0000 ? 1 | 2020-06-18T16:33:42.133748687Z | 867,3 | LORA | SF7BW125 | 4/5 | undefined | eui-fcc23dfffe0b696a | 1750573211 | 4 | -112 | -8,8 | undefined | undefined | undefined | eui-b827ebfffef74e1a | 841101043 | 4 | -87 | 9,5 | undefined | undefined | undefined
test_04_02_19 | pycomarduino | 0058924AB98D5AD4 | 1 | 23 | WzRdIEQyMC8wNS8xOCB0MTI6MDAgVzAwMDAgVDAwMDAgPyAxICAgAA== | [4] D20/05/18 t12:00 W0000 T0000 ? 1 | 2020-06-18T16:34:27.553631729Z | 868,3 | LORA | SF7BW125 | 4/5 | undefined | eui-b827ebfffef74e1a | 886512091 | 1 | -87 | 10,2 | undefined | undefined | undefined
test_04_02_19 | pycomarduino | 0058924AB98D5AD4 | 1 | 24 | WzVdIEQyMC8wNS8xOCB0MTI6MDAgVzAwMDAgVDAwMDAgPyAxICAgAA== | [5] D20/05/18 t12:00 W0000 T0000 ? 1 | 2020-06-18T16:34:54.363585374Z | 868,5 | LORA | SF7BW125 | 4/5 | undefined | eui-fcc23dfffe0b696a | 1822807323 | 2 | -111 | -3,2 | undefined | undefined | undefined | eui-b827ebfffef74e1a | 913335187 | 2 | -85 | 7,5 | undefined | undefined | undefined
test_04_02_19 | pycomarduino | 0058924AB98D5AD4 | 1 | 25 | WzJdIEQyMC8wNS8xOCB0MTI6MDAgVzAwMDAgVDAwMDAgPyAxICAgAA== | [2] D20/05/18 t12:00 W0000 T0000 ? 1 | 2020-06-18T16:38:11.383865783Z | 868,1 | LORA | SF7BW125 | 4/5 | undefined | eui-b827ebfffef74e1a | 1110348699 | 0 | -87 | 9,2 | undefined | undefined | undefined
test_04_02_19 | pycomarduino | 0058924AB98D5AD4 | 1 | 26 | WzNdIEQyMC8wNS8xOCB0MTI6MDAgVzAwMDAgVDAwMDAgPyAxICAgAA== | [3] D20/05/18 t12:00 W0000 T0000 ? 1 | 2020-06-18T16:38:42.127212745Z | 867,5 | LORA | SF7BW125 | 4/5 | undefined | eui-b827ebfffef74e1a | 1141099516 | 5 | -87 | 8 | undefined | undefined | undefined
test_04_02_19 | pycomarduino | 0058924AB98D5AD4 | 1 | 27 | WzRdIEQyMC8wNS8xOCB0MTI6MDAgVzAwMDAgVDAwMDAgPyAxICAgAA== | [4] D20/05/18 t12:00 W0000 T0000 ? 1 | 2020-06-18T16:39:27.54107291Z | 868,3 | LORA | SF7BW125 | 4/5 | undefined | eui-b827ebfffef74e1a | 1186511315 | 1 | -87 | 10 | undefined | undefined | undefined
test_04_02_19 | pycomarduino | 0058924AB98D5AD4 | 1 | 28 | WzVdIEQyMC8wNS8xOCB0MTI6MDAgVzAwMDAgVDAwMDAgPyAxICAgAA== | [5] D20/05/18 t12:00 W0000 T0000 ? 1 | 2020-06-18T16:39:54.364588321Z | 868,5 | LORA | SF7BW125 | 4/5 | undefined | eui-fcc23dfffe0b696a | 2122806595 | 2 | -108 | -3,5 | undefined | undefined | undefined | eui-b827ebfffef74e1a | 1213334587 | 2 | -87 | 6,5 | undefined | undefined | undefined
test_04_02_19 | pycomarduino | 0058924AB98D5AD4 | 1 | 29 | WzJdIEQyMC8wNS8xOCB0MTI6MDAgVzAwMDAgVDAwMDAgPyAxICAgAA== | [2] D20/05/18 t12:00 W0000 T0000 ? 1 | 2020-06-18T16:43:11.378220056Z | 868,1 | LORA | SF7BW125 | 4/5 | undefined | eui-fcc23dfffe0b696a | 2319822747 | 0 | -112 | -7,5 | undefined | undefined | undefined | eui-b827ebfffef74e1a | 1410350811 | 0 | -89 | 10 | undefined | undefined | undefined
test_04_02_19 | pycomarduino | 0058924AB98D5AD4 | 1 | 30 | WzNdIEQyMC8wNS8xOCB0MTI6MDAgVzAwMDAgVDAwMDAgPyAxICAgAA== | [3] D20/05/18 t12:00 W0000 T0000 ? 1 | 2020-06-18T16:43:42.128356021Z | 867,7 | LORA | SF7BW125 | 4/5 | undefined | eui-b827ebfffef74e1a | 1441100108 | 6 | -87 | 10,8 | undefined | undefined | undefined
test_04_02_19 | pycomarduino | 0058924AB98D5AD4 | 1 | 31 | WzRdIEQyMC8wNS8xOCB0MTI6MDAgVzAwMDAgVDAwMDAgPyAxICAgAA== | [4] D20/05/18 t12:00 W0000 T0000 ? 1 | 2020-06-18T16:44:27.555507191Z | 868,3 | LORA | SF7BW125 | 4/5 | undefined | eui-b827ebfffef74e1a | 1486512587 | 1 | -87 | 10,2 | undefined | undefined | undefined
test_04_02_19 | pycomarduino | 0058924AB98D5AD4 | 1 | 32 | WzVdIEQyMC8wNS8xOCB0MTI6MDAgVzAwMDAgVDAwMDAgPyAxICAgAA== | [5] D20/05/18 t12:00 W0000 T0000 ? 1 | 2020-06-18T16:44:54.496765948Z | 868,5 | LORA | SF7BW125 | 4/5 | undefined | eui-fcc23dfffe0b696a | 2422808187 | 2 | -112 | -3,8 | undefined | undefined | undefined | eui-b827ebfffef74e1a | 1513336299 | 2 | -87 | 7,5 | undefined | undefined | undefined
test_04_02_19 | pycomarduino | 0058924AB98D5AD4 | 1 | 33 | WzJdIEQyMC8wNS8xOCB0MTI6MDAgVzAwMDAgVDAwMDAgPyAxICAgAA== | [2] D20/05/18 t12:00 W0000 T0000 ? 1 | 2020-06-18T16:48:11.388014635Z | 868,1 | LORA | SF7BW125 | 4/5 | undefined | eui-b827ebfffef74e1a | 1710350875 | 0 | -89 | 10,2 | undefined | undefined | undefined
test_04_02_19 | pycomarduino | 0058924AB98D5AD4 | 1 | 34 | WzNdIEQyMC8wNS8xOCB0MTI6MDAgVzAwMDAgVDAwMDAgPyAxICAgAA== | [3] D20/05/18 t12:00 W0000 T0000 ? 1 | 2020-06-18T16:48:42.125076495Z | 867,9 | LORA | SF7BW125 | 4/5 | undefined | eui-b827ebfffef74e1a | 1741098572 | 7 | -89 | 9 | undefined | undefined | undefined
test_04_02_19 | pycomarduino | 0058924AB98D5AD4 | 1 | 35 | WzRdIEQyMC8wNS8xOCB0MTI6MDAgVzAwMDAgVDAwMDAgPyAxICAgAA== | [4] D20/05/18 t12:00 W0000 T0000 ? 1 | 2020-06-18T16:49:27.586354578Z | 868,3 | LORA | SF7BW125 | 4/5 | undefined | eui-b827ebfffef74e1a | 1786511723 | 1 | -85 | 9,5 | undefined | undefined | undefined
test_04_02_19 | pycomarduino | 0058924AB98D5AD4 | 1 | 36 | WzVdIEQyMC8wNS8xOCB0MTI6MDAgVzAwMDAgVDAwMDAgPyAxICAgAA== | [5] D20/05/18 t12:00 W0000 T0000 ? 1 | 2020-06-18T16:49:54.362622471Z | 868,5 | LORA | SF7BW125 | 4/5 | undefined | eui-fcc23dfffe0b696a | 2722807563 | 2 | -111 | -3 | undefined | undefined | undefined | eui-b827ebfffef74e1a | 1813335795 | 2 | -87 | 7,8 | undefined | undefined | undefined
test_04_02_19 | pycomarduino | 0058924AB98D5AD4 | 1 | 37 | WzJdIEQyMC8wNS8xOCB0MTI6MDAgVzAwMDAgVDAwMDAgPyAxICAgAA== | [2] D20/05/18 t12:00 W0000 T0000 ? 1 | 2020-06-18T16:53:11.382143115Z | 868,1 | LORA | SF7BW125 | 4/5 | undefined | eui-fcc23dfffe0b696a | 2919824739 | 0 | -115 | -7 | undefined | undefined | undefined | eui-b827ebfffef74e1a | 2010353059 | 0 | -89 | 10,8 | undefined | undefined | undefined
test_04_02_19 | pycomarduino | 0058924AB98D5AD4 | 1 | 38 | WzNdIEQyMC8wNS8xOCB0MTI6MDAgVzAwMDAgVDAwMDAgPyAxICAgAA== | [3] D20/05/18 t12:00 W0000 T0000 ? 1 | 2020-06-18T16:53:42.128121885Z | 867,1 | LORA | SF7BW125 | 4/5 | undefined | eui-b827ebfffef74e1a | 2041099171 | 3 | -89 | 9,5 | undefined | undefined | undefined
test_04_02_19 | pycomarduino | 0058924AB98D5AD4 | 1 | 39 | WzRdIEQyMC8wNS8xOCB0MTI6MDAgVzAwMDAgVDAwMDAgPyAxICAgAA== | [4] D20/05/18 t12:00 W0000 T0000 ? 1 | 2020-06-18T16:54:27.544942605Z | 868,3 | LORA | SF7BW125 | 4/5 | undefined | eui-b827ebfffef74e1a | 2086513011 | 1 | -82 | 9,2 | undefined | undefined | undefined
test_04_02_19 | pycomarduino | 0058924AB98D5AD4 | 1 | 40 | WzVdIEQyMC8wNS8xOCB0MTI6MDAgVzAwMDAgVDAwMDAgPyAxICAgAA== | [5] D20/05/18 t12:00 W0000 T0000 ? 1 | 2020-06-18T16:54:54.364789382Z | 868,5 | LORA | SF7BW125 | 4/5 | undefined | eui-fcc23dfffe0b696a | 3022808971 | 2 | -110 | -2 | undefined | undefined | undefined | eui-b827ebfffef74e1a | 2113337323 | 2 | -79 | 8 | undefined | undefined | undefined
test_04_02_19 | pycomarduino | 0058924AB98D5AD4 | 1 | 41 | WzJdIEQyMC8wNS8xOCB0MTI6MDAgVzAwMDAgVDAwMDAgPyAxICAgAA== | [2] D20/05/18 t12:00 W0000 T0000 ? 1 | 2020-06-18T16:58:11.378352387Z | 868,1 | LORA | SF7BW125 | 4/5 | undefined | eui-b827ebfffef74e1a | 2310353235 | 0 | -84 | 9 | undefined | undefined | undefined
test_04_02_19 | pycomarduino | 0058924AB98D5AD4 | 1 | 42 | WzNdIEQyMC8wNS8xOCB0MTI6MDAgVzAwMDAgVDAwMDAgPyAxICAgAA== | [3] D20/05/18 t12:00 W0000 T0000 ? 1 | 2020-06-18T16:58:42.125393557Z | 867,3 | LORA | SF7BW125 | 4/5 | undefined | eui-fcc23dfffe0b696a | 3250569227 | 4 | -113 | -5,2 | undefined | undefined | undefined | eui-b827ebfffef74e1a | 2341097683 | 4 | -85 | 9,5 | undefined | undefined | undefined
test_04_02_19 | pycomarduino | 0058924AB98D5AD4 | 1 | 43 | WzRdIEQyMC8wNS8xOCB0MTI6MDAgVzAwMDAgVDAwMDAgPyAxICAgAA== | [4] D20/05/18 t12:00 W0000 T0000 ? 1 | 2020-06-18T16:59:27.544906678Z | 868,3 | LORA | SF7BW125 | 4/5 | undefined | eui-b827ebfffef74e1a | 2386512235 | 1 | -81 | 10,2 | undefined | undefined | undefined
test_04_02_19 | pycomarduino | 0058924AB98D5AD4 | 1 | 44 | WzVdIEQyMC8wNS8xOCB0MTI6MDAgVzAwMDAgVDAwMDAgPyAxICAgAA== | [5] D20/05/18 t12:00 W0000 T0000 ? 1 | 2020-06-18T16:59:54.365920456Z | 868,5 | LORA | SF7BW125 | 4/5 | undefined | eui-fcc23dfffe0b696a | 3322808347 | 2 | -112 | -2,8 | undefined | undefined | undefined | eui-b827ebfffef74e1a | 2413336835 | 2 | -81 | 7,5 | undefined | undefined | undefined
test_04_02_19 | pycomarduino | 0058924AB98D5AD4 | 1 | 45 | WzJdIEQyMC8wNS8xOCB0MTI6MDAgVzAwMDAgVDAwMDAgPyAxICAgAA== | [2] D20/05/18 t12:00 W0000 T0000 ? 1 | 2020-06-18T17:03:11.380344361Z | 868,1 | LORA | SF7BW125 | 4/5 | undefined | eui-b827ebfffef74e1a | 2610353275 | 0 | -84 | 8,8 | undefined | undefined | undefined
test_04_02_19 | pycomarduino | 0058924AB98D5AD4 | 1 | 46 | WzNdIEQyMC8wNS8xOCB0MTI6MDAgVzAwMDAgVDAwMDAgPyAxICAgAA== | [3] D20/05/18 t12:00 W0000 T0000 ? 1 | 2020-06-18T17:03:42.122428929Z | 867,5 | LORA | SF7BW125 | 4/5 | undefined | eui-fcc23dfffe0b696a | 3550567668 | 5 | -112 | -7,2 | undefined | undefined | undefined | eui-b827ebfffef74e1a | 2641096252 | 5 | -83 | 7,2 | undefined | undefined | undefined
test_04_02_19 | pycomarduino | 0058924AB98D5AD4 | 1 | 47 | WzRdIEQyMC8wNS8xOCB0MTI6MDAgVzAwMDAgVDAwMDAgPyAxICAgAA== | [4] D20/05/18 t12:00 W0000 T0000 ? 1 | 2020-06-18T17:04:27.537622249Z | 868,3 | LORA | SF7BW125 | 4/5 | undefined | eui-b827ebfffef74e1a | 2686511467 | 1 | -81 | 9,2 | undefined | undefined | undefined
test_04_02_19 | pycomarduino | 0058924AB98D5AD4 | 1 | 48 | WzVdIEQyMC8wNS8xOCB0MTI6MDAgVzAwMDAgVDAwMDAgPyAxICAgAA== | [5] D20/05/18 t12:00 W0000 T0000 ? 1 | 2020-06-18T17:04:54.36698543Z | 868,5 | LORA | SF7BW125 | 4/5 | undefined | eui-fcc23dfffe0b696a | 3622807803 | 2 | -111 | -2 | undefined | undefined | undefined | eui-b827ebfffef74e1a | 2713336411 | 2 | -82 | 8 | undefined | undefined | undefined
test_04_02_19 | pycomarduino | 0058924AB98D5AD4 | 1 | 49 | WzJdIEQyMC8wNS8xOCB0MTI6MDAgVzAwMDAgVDAwMDAgPyAxICAgAA== | [2] D20/05/18 t12:00 W0000 T0000 ? 1 | 2020-06-18T17:08:11.378701134Z | 868,1 | LORA | SF7BW125 | 4/5 | undefined | eui-b827ebfffef74e1a | 2910355403 | 0 | -82 | 9,8 | undefined | undefined | undefined
test_04_02_19 | pycomarduino | 0058924AB98D5AD4 | 1 | 50 | WzNdIEQyMC8wNS8xOCB0MTI6MDAgVzAwMDAgVDAwMDAgPyAxICAgAA== | [3] D20/05/18 t12:00 W0000 T0000 ? 1 | 2020-06-18T17:08:42.122863903Z | 867,7 | LORA | SF7BW125 | 4/5 | undefined | eui-b827ebfffef74e1a | 2941096796 | 6 | -83 | 9,8 | undefined | undefined | undefined
test_04_02_19 | pycomarduino | 0058924AB98D5AD4 | 1 | 51 | WzRdIEQyMC8wNS8xOCB0MTI6MDAgVzAwMDAgVDAwMDAgPyAxICAgAA== | [4] D20/05/18 t12:00 W0000 T0000 ? 1 | 2020-06-18T17:09:27.539840823Z | 868,3 | LORA | SF7BW125 | 4/5 | undefined | eui-b827ebfffef74e1a | 2986512683 | 1 | -82 | 10,8 | undefined | undefined | undefined
test_04_02_19 | pycomarduino | 0058924AB98D5AD4 | 1 | 52 | WzVdIEQyMC8wNS8xOCB0MTI6MDAgVzAwMDAgVDAwMDAgPyAxICAgAA== | [5] D20/05/18 t12:00 W0000 T0000 ? 1 | 2020-06-18T17:09:54.367706056Z | 868,5 | LORA | SF7BW125 | 4/5 | undefined | eui-fcc23dfffe0b696a | 3922809211 | 2 | -111 | -1,2 | undefined | undefined | undefined | eui-b827ebfffef74e1a | 3013337947 | 2 | -83 | 7,8 | undefined | undefined | undefined
test_04_02_19 | pycomarduino | 0058924AB98D5AD4 | 1 | 53 | WzJdIEQyMC8wNS8xOCB0MTI6MDAgVzAwMDAgVDAwMDAgPyAxICAgAA== | [2] D20/05/18 t12:00 W0000 T0000 ? 1 | 2020-06-18T17:13:11.381987127Z | 868,1 | LORA | SF7BW125 | 4/5 | undefined | eui-b827ebfffef74e1a | 3210355523 | 0 | -85 | 10 | undefined | undefined | undefined
test_04_02_19 | pycomarduino | 0058924AB98D5AD4 | 1 | 54 | WzNdIEQyMC8wNS8xOCB0MTI6MDAgVzAwMDAgVDAwMDAgPyAxICAgAA== | [3] D20/05/18 t12:00 W0000 T0000 ? 1 | 2020-06-18T17:13:42.12424164Z | 867,9 | LORA | SF7BW125 | 4/5 | undefined | eui-fcc23dfffe0a9698 | 4152586380 | 7 | -115 | -7,5 | undefined | undefined | undefined | eui-b827ebfffef74e1a | 3241095276 | 7 | -85 | 11,2 | undefined | undefined | undefined
test_04_02_19 | pycomarduino | 0058924AB98D5AD4 | 1 | 55 | WzRdIEQyMC8wNS8xOCB0MTI6MDAgVzAwMDAgVDAwMDAgPyAxICAgAA== | [4] D20/05/18 t12:00 W0000 T0000 ? 1 | 2020-06-18T17:14:27.572760634Z | 868,3 | LORA | SF7BW125 | 4/5 | undefined | eui-b827ebfffef74e1a | 3286511907 | 1 | -82 | 10,2 | undefined | undefined | undefined
test_04_02_19 | pycomarduino | 0058924AB98D5AD4 | 1 | 56 | WzVdIEQyMC8wNS8xOCB0MTI6MDAgVzAwMDAgVDAwMDAgPyAxICAgAA== | [5] D20/05/18 t12:00 W0000 T0000 ? 1 | 2020-06-18T17:14:54.364113313Z | 868,5 | LORA | SF7BW125 | 4/5 | undefined | eui-b827ebfffef74e1a | 3313337435 | 2 | -83 | 7,8 | undefined | undefined | undefined
test_04_02_19 | pycomarduino | 0058924AB98D5AD4 | 1 | 58 | WzNdIEQyMC8wNS8xOCB0MTI6MDAgVzAwMDAgVDAwMDAgPyAxICAgAA== | [3] D20/05/18 t12:00 W0000 T0000 ? 1 | 2020-06-18T17:18:42.129475101Z | 867,1 | LORA | SF7BW125 | 4/5 | undefined | eui-fcc23dfffe0b696a | 155597531 | 3 | -113 | -5,5 | undefined | undefined | undefined
test_04_02_19 | pycomarduino | 0058924AB98D5AD4 | 1 | 59 | WzRdIEQyMC8wNS8xOCB0MTI6MDAgVzAwMDAgVDAwMDAgPyAxICAgAA== | [4] D20/05/18 t12:00 W0000 T0000 ? 1 | 2020-06-18T17:19:27.54292358Z | 868,3 | LORA | SF7BW125 | 4/5 | undefined | eui-b827ebfffef74e1a | 3586511059 | 1 | -80 | 10,5 | undefined | undefined | undefined
test_04_02_19 | pycomarduino | 0058924AB98D5AD4 | 1 | 60 | WzVdIEQyMC8wNS8xOCB0MTI6MDAgVzAwMDAgVDAwMDAgPyAxICAgAA== | [5] D20/05/18 t12:00 W0000 T0000 ? 1 | 2020-06-18T17:19:54.358728369Z | 868,5 | LORA | SF7BW125 | 4/5 | undefined | eui-fcc23dfffe0b696a | 227840739 | 2 | -112 | -3 | undefined | undefined | undefined | eui-b827ebfffef74e1a | 3613337019 | 2 | -79 | 7,2 | undefined | undefined | undefined
test_04_02_19 | pycomarduino | 0058924AB98D5AD4 | 1 | 61 | WzJdIEQyMC8wNS8xOCB0MTI6MDAgVzAwMDAgVDAwMDAgPyAxICAgAA== | [2] D20/05/18 t12:00 W0000 T0000 ? 1 | 2020-06-18T17:23:11.379246543Z | 868,1 | LORA | SF7BW125 | 4/5 | undefined | eui-b827ebfffef74e1a | 3810357755 | 0 | -82 | 9,2 | undefined | undefined | undefined
test_04_02_19 | pycomarduino | 0058924AB98D5AD4 | 1 | 62 | WzNdIEQyMC8wNS8xOCB0MTI6MDAgVzAwMDAgVDAwMDAgPyAxICAgAA== | [3] D20/05/18 t12:00 W0000 T0000 ? 1 | 2020-06-18T17:23:42.117728254Z | 867,3 | LORA | SF7BW125 | 4/5 | undefined | eui-fcc23dfffe0b696a | 455597939 | 4 | -113 | -4,2 | undefined | undefined | undefined | eui-b827ebfffef74e1a | 3841094315 | 4 | -85 | 9,2 | undefined | undefined | undefined
test_04_02_19 | pycomarduino | 0058924AB98D5AD4 | 1 | 63 | WzRdIEQyMC8wNS8xOCB0MTI6MDAgVzAwMDAgVDAwMDAgPyAxICAgAA== | [4] D20/05/18 t12:00 W0000 T0000 ? 1 | 2020-06-18T17:24:27.821010254Z | 868,3 | LORA | SF7BW125 | 4/5 | undefined | eui-b827ebfffef74e1a | 3886512339 | 1 | -81 | 9 | undefined | undefined | undefined
test_04_02_19 | pycomarduino | 0058924AB98D5AD4 | 1 | 64 | WzVdIEQyMC8wNS8xOCB0MTI6MDAgVzAwMDAgVDAwMDAgPyAxICAgAA== | [5] D20/05/18 t12:00 W0000 T0000 ? 1 | 2020-06-18T17:24:54.368047732Z | 868,5 | LORA | SF7BW125 | 4/5 | undefined | eui-fcc23dfffe0b696a | 527842139 | 2 | -111 | -1,2 | undefined | undefined | undefined | eui-b827ebfffef74e1a | 3913338547 | 2 | -79 | 8,2 | undefined | undefined | undefined
test_04_02_19 | pycomarduino | 0058924AB98D5AD4 | 1 | 65 | WzJdIEQyMC8wNS8xOCB0MTI6MDAgVzAwMDAgVDAwMDAgPyAxICAgAA== | [2] D20/05/18 t12:00 W0000 T0000 ? 1 | 2020-06-18T17:28:11.384899337Z | 868,1 | LORA | SF7BW125 | 4/5 | undefined | eui-fcc23dfffe0a9698 | 726881099 | 0 | -115 | -8 | undefined | undefined | undefined | eui-b827ebfffef74e1a | 4110357867 | 0 | -83 | 9,2 | undefined | undefined | undefined
test_04_02_19 | pycomarduino | 0058924AB98D5AD4 | 1 | 66 | WzNdIEQyMC8wNS8xOCB0MTI6MDAgVzAwMDAgVDAwMDAgPyAxICAgAA== | [3] D20/05/18 t12:00 W0000 T0000 ? 1 | 2020-06-18T17:28:42.120872141Z | 867,5 | LORA | SF7BW125 | 4/5 | undefined | eui-fcc23dfffe0b696a | 755596380 | 5 | -113 | -8,2 | undefined | undefined | undefined | eui-b827ebfffef74e1a | 4141092884 | 5 | -81 | 6,8 | undefined | undefined | undefined
test_04_02_19 | pycomarduino | 0058924AB98D5AD4 | 1 | 67 | WzRdIEQyMC8wNS8xOCB0MTI6MDAgVzAwMDAgVDAwMDAgPyAxICAgAA== | [4] D20/05/18 t12:00 W0000 T0000 ? 1 | 2020-06-18T17:29:27.53861796Z | 868,3 | LORA | SF7BW125 | 4/5 | undefined | eui-b827ebfffef74e1a | 4186511547 | 1 | -83 | 9,8 | undefined | undefined | undefined
test_04_02_19 | pycomarduino | 0058924AB98D5AD4 | 1 | 68 | WzVdIEQyMC8wNS8xOCB0MTI6MDAgVzAwMDAgVDAwMDAgPyAxICAgAA== | [5] D20/05/18 t12:00 W0000 T0000 ? 1 | 2020-06-18T17:29:54.364221135Z | 868,5 | LORA | SF7BW125 | 4/5 | undefined | eui-fcc23dfffe0b696a | 827841507 | 2 | -111 | -2 | undefined | undefined | undefined | eui-b827ebfffef74e1a | 4213338043 | 2 | -81 | 7,8 | undefined | undefined | undefined
test_04_02_19 | pycomarduino | 0058924AB98D5AD4 | 1 | 69 | WzJdIEQyMC8wNS8xOCB0MTI6MDAgVzAwMDAgVDAwMDAgPyAxICAgAA== | [2] D20/05/18 t12:00 W0000 T0000 ? 1 | 2020-06-18T17:33:11.384928806Z | 868,1 | LORA | SF7BW125 | 4/5 | undefined | eui-fcc23dfffe0a9698 | 1026882995 | 0 | -112 | -9,5 | undefined | undefined | undefined | eui-b827ebfffef74e1a | 115392675 | 0 | -84 | 9,8 | undefined | undefined | undefined
test_04_02_19 | pycomarduino | 0058924AB98D5AD4 | 1 | 70 | WzNdIEQyMC8wNS8xOCB0MTI6MDAgVzAwMDAgVDAwMDAgPyAxICAgAA== | [3] D20/05/18 t12:00 W0000 T0000 ? 1 | 2020-06-18T17:33:42.129538814Z | 867,7 | LORA | SF7BW125 | 4/5 | undefined | eui-b827ebfffef74e1a | 146126116 | 6 | -84 | 9,5 | undefined | undefined | undefined
test_04_02_19 | pycomarduino | 0058924AB98D5AD4 | 1 | 71 | WzRdIEQyMC8wNS8xOCB0MTI6MDAgVzAwMDAgVDAwMDAgPyAxICAgAA== | [4] D20/05/18 t12:00 W0000 T0000 ? 1 | 2020-06-18T17:34:27.537909029Z | 868,3 | LORA | SF7BW125 | 4/5 | undefined | eui-b827ebfffef74e1a | 191545539 | 1 | -81 | 9,8 | undefined | undefined | undefined
test_04_02_19 | pycomarduino | 0058924AB98D5AD4 | 1 | 72 | WzVdIEQyMC8wNS8xOCB0MTI6MDAgVzAwMDAgVDAwMDAgPyAxICAgAA== | [5] D20/05/18 t12:00 W0000 T0000 ? 1 | 2020-06-18T17:34:54.361852503Z | 868,5 | LORA | SF7BW125 | 4/5 | undefined | eui-fcc23dfffe0b696a | 1127842979 | 2 | -111 | -2 | undefined | undefined | undefined | eui-b827ebfffef74e1a | 218372347 | 2 | -80 | 7,8 | undefined | undefined | undefined
test_04_02_19 | pycomarduino | 0058924AB98D5AD4 | 1 | 73 | WzJdIEQyMC8wNS8xOCB0MTI6MDAgVzAwMDAgVDAwMDAgPyAxICAgAA== | [2] D20/05/18 t12:00 W0000 T0000 ? 1 | 2020-06-18T17:38:11.391158279Z | 868,1 | LORA | SF7BW125 | 4/5 | undefined | eui-b827ebfffef74e1a | 415392795 | 0 | -84 | 8,8 | undefined | undefined | undefined
test_04_02_19 | pycomarduino | 0058924AB98D5AD4 | 1 | 74 | WzNdIEQyMC8wNS8xOCB0MTI6MDAgVzAwMDAgVDAwMDAgPyAxICAgAA== | [3] D20/05/18 t12:00 W0000 T0000 ? 1 | 2020-06-18T17:38:42.269340041Z | 867,9 | LORA | SF7BW125 | 4/5 | undefined | eui-fcc23dfffe0a9698 | 1357765220 | 7 | -115 | -6 | undefined | undefined | undefined | eui-b827ebfffef74e1a | 446275124 | 7 | -85 | 9,2 | undefined | undefined | undefined
test_04_02_19 | pycomarduino | 0058924AB98D5AD4 | 1 | 75 | WzRdIEQyMC8wNS8xOCB0MTI6MDAgVzAwMDAgVDAwMDAgPyAxICAgAA== | [4] D20/05/18 t12:00 W0000 T0000 ? 1 | 2020-06-18T17:39:27.545620202Z | 868,3 | LORA | SF7BW125 | 4/5 | undefined | eui-b827ebfffef74e1a | 491544643 | 1 | -82 | 9 | undefined | undefined | undefined
test_04_02_19 | pycomarduino | 0058924AB98D5AD4 | 1 | 76 | WzVdIEQyMC8wNS8xOCB0MTI6MDAgVzAwMDAgVDAwMDAgPyAxICAgAA== | [5] D20/05/18 t12:00 W0000 T0000 ? 1 | 2020-06-18T17:39:54.366536274Z | 868,5 | LORA | SF7BW125 | 4/5 | undefined | eui-fcc23dfffe0b696a | 1427842363 | 2 | -111 | -1,8 | undefined | undefined | undefined | eui-b827ebfffef74e1a | 518371859 | 2 | -83 | 7,5 | undefined | undefined | undefined
test_04_02_19 | pycomarduino | 0058924AB98D5AD4 | 1 | 77 | WzJdIEQyMC8wNS8xOCB0MTI6MDAgVzAwMDAgVDAwMDAgPyAxICAgAA== | [2] D20/05/18 t12:00 W0000 T0000 ? 1 | 2020-06-18T17:43:11.391177848Z | 868,1 | LORA | SF7BW125 | 4/5 | undefined | eui-b827ebfffef74e1a | 715392891 | 0 | -84 | 9,5 | undefined | undefined | undefined
test_04_02_19 | pycomarduino | 0058924AB98D5AD4 | 1 | 78 | WzNdIEQyMC8wNS8xOCB0MTI6MDAgVzAwMDAgVDAwMDAgPyAxICAgAA== | [3] D20/05/18 t12:00 W0000 T0000 ? 1 | 2020-06-18T17:43:42.12343935Z | 867,1 | LORA | SF7BW125 | 4/5 | undefined | eui-fcc23dfffe0b696a | 1655593587 | 3 | -115 | -4,8 | undefined | undefined | undefined | eui-b827ebfffef74e1a | 746123187 | 3 | -87 | 9,8 | undefined | undefined | undefined
test_04_02_19 | pycomarduino | 0058924AB98D5AD4 | 1 | 79 | WzRdIEQyMC8wNS8xOCB0MTI6MDAgVzAwMDAgVDAwMDAgPyAxICAgAA== | [4] D20/05/18 t12:00 W0000 T0000 ? 1 | 2020-06-18T17:44:27.538050339Z | 868,3 | LORA | SF7BW125 | 4/5 | undefined | eui-b827ebfffef74e1a | 791543939 | 1 | -81 | 10 | undefined | undefined | undefined
test_04_02_19 | pycomarduino | 0058924AB98D5AD4 | 1 | 80 | WzVdIEQyMC8wNS8xOCB0MTI6MDAgVzAwMDAgVDAwMDAgPyAxICAgAA== | [5] D20/05/18 t12:00 W0000 T0000 ? 1 | 2020-06-18T17:44:54.360785263Z | 868,5 | LORA | SF7BW125 | 4/5 | undefined | eui-fcc23dfffe0b696a | 1727841699 | 2 | -112 | -3,8 | undefined | undefined | undefined | eui-b827ebfffef74e1a | 818371331 | 2 | -82 | 7,8 | undefined | undefined | undefined
test_04_02_19 | pycomarduino | 0058924AB98D5AD4 | 1 | 81 | WzJdIEQyMC8wNS8xOCB0MTI6MDAgVzAwMDAgVDAwMDAgPyAxICAgAA== | [2] D20/05/18 t12:00 W0000 T0000 ? 1 | 2020-06-18T17:48:11.390610945Z | 868,1 | LORA | SF7BW125 | 4/5 | undefined | eui-b827ebfffef74e1a | 1015395011 | 0 | -85 | 9,2 | undefined | undefined | undefined
test_04_02_19 | pycomarduino | 0058924AB98D5AD4 | 1 | 82 | WzNdIEQyMC8wNS8xOCB0MTI6MDAgVzAwMDAgVDAwMDAgPyAxICAgAA== | [3] D20/05/18 t12:00 W0000 T0000 ? 1 | 2020-06-18T17:48:42.115109716Z | 867,3 | LORA | SF7BW125 | 4/5 | undefined | eui-fcc23dfffe0b696a | 1955593995 | 4 | -112 | -3,8 | undefined | undefined | undefined | eui-b827ebfffef74e1a | 1046123731 | 4 | -84 | 9,2 | undefined | undefined | undefined
test_04_02_19 | pycomarduino | 0058924AB98D5AD4 | 1 | 83 | WzRdIEQyMC8wNS8xOCB0MTI6MDAgVzAwMDAgVDAwMDAgPyAxICAgAA== | [4] D20/05/18 t12:00 W0000 T0000 ? 1 | 2020-06-18T17:49:27.542702195Z | 868,3 | LORA | SF7BW125 | 4/5 | undefined | eui-b827ebfffef74e1a | 1091545147 | 1 | -81 | 9,2 | undefined | undefined | undefined
test_04_02_19 | pycomarduino | 0058924AB98D5AD4 | 1 | 84 | WzVdIEQyMC8wNS8xOCB0MTI6MDAgVzAwMDAgVDAwMDAgPyAxICAgAA== | [5] D20/05/18 t12:00 W0000 T0000 ? 1 | 2020-06-18T17:49:54.36871452Z | 868,5 | LORA | SF7BW125 | 4/5 | undefined | eui-fcc23dfffe0b696a | 2027843131 | 2 | -113 | -3,2 | undefined | undefined | undefined | eui-b827ebfffef74e1a | 1118372891 | 2 | -83 | 7,8 | undefined | undefined | undefined
test_04_02_19 | pycomarduino | 0058924AB98D5AD4 | 1 | 85 | WzJdIEQyMC8wNS8xOCB0MTI6MDAgVzAwMDAgVDAwMDAgPyAxICAgAA== | [2] D20/05/18 t12:00 W0000 T0000 ? 1 | 2020-06-18T17:53:11.390557199Z | 868,1 | LORA | SF7BW125 | 4/5 | undefined | eui-b827ebfffef74e1a | 1315395147 | 0 | -83 | 10 | undefined | undefined | undefined
test_04_02_19 | pycomarduino | 0058924AB98D5AD4 | 1 | 86 | WzNdIEQyMC8wNS8xOCB0MTI6MDAgVzAwMDAgVDAwMDAgPyAxICAgAA== | [3] D20/05/18 t12:00 W0000 T0000 ? 1 | 2020-06-18T17:53:42.111845669Z | 867,5 | LORA | SF7BW125 | 4/5 | undefined | eui-fcc23dfffe0b696a | 2255592444 | 5 | -113 | -6 | undefined | undefined | undefined | eui-b827ebfffef74e1a | 1346122300 | 5 | -82 | 7,5 | undefined | undefined | undefined
test_04_02_19 | pycomarduino | 0058924AB98D5AD4 | 1 | 87 | WzRdIEQyMC8wNS8xOCB0MTI6MDAgVzAwMDAgVDAwMDAgPyAxICAgAA== | [4] D20/05/18 t12:00 W0000 T0000 ? 1 | 2020-06-18T17:54:27.542053149Z | 868,3 | LORA | SF7BW125 | 4/5 | undefined | eui-b827ebfffef74e1a | 1391544363 | 1 | -83 | 9,2 | undefined | undefined | undefined
test_04_02_19 | pycomarduino | 0058924AB98D5AD4 | 1 | 88 | WzVdIEQyMC8wNS8xOCB0MTI6MDAgVzAwMDAgVDAwMDAgPyAxICAgAA== | [5] D20/05/18 t12:00 W0000 T0000 ? 1 | 2020-06-18T17:54:54.364087872Z | 868,5 | LORA | SF7BW125 | 4/5 | undefined | eui-fcc23dfffe0b696a | 2327842491 | 2 | -113 | -2,8 | undefined | undefined | undefined | eui-b827ebfffef74e1a | 1418372379 | 2 | -81 | 8 | undefined | undefined | undefined
test_04_02_19 | pycomarduino | 0058924AB98D5AD4 | 1 | 89 | WzJdIEQyMC8wNS8xOCB0MTI6MDAgVzAwMDAgVDAwMDAgPyAxICAgAA== | [2] D20/05/18 t12:00 W0000 T0000 ? 1 | 2020-06-18T17:58:11.388361152Z | 868,1 | LORA | SF7BW125 | 4/5 | undefined | eui-fcc23dfffe0a9698 | 2526884483 | 0 | -116 | -7,8 | undefined | undefined | undefined | eui-b827ebfffef74e1a | 1615395171 | 0 | -84 | 10,5 | undefined | undefined | undefined
test_04_02_19 | pycomarduino | 0058924AB98D5AD4 | 1 | 90 | WzNdIEQyMC8wNS8xOCB0MTI6MDAgVzAwMDAgVDAwMDAgPyAxICAgAA== | [3] D20/05/18 t12:00 W0000 T0000 ? 1 | 2020-06-18T17:58:42.118755126Z | 867,7 | LORA | SF7BW125 | 4/5 | undefined | eui-fcc23dfffe0b696a | 2555590804 | 6 | -112 | -4 | undefined | undefined | undefined | eui-b827ebfffef74e1a | 1646120788 | 6 | -82 | 9,5 | undefined | undefined | undefined
test_04_02_19 | pycomarduino | 0058924AB98D5AD4 | 1 | 91 | WzRdIEQyMC8wNS8xOCB0MTI6MDAgVzAwMDAgVDAwMDAgPyAxICAgAA== | [4] D20/05/18 t12:00 W0000 T0000 ? 1 | 2020-06-18T17:59:27.753224692Z | 868,3 | LORA | SF7BW125 | 4/5 | undefined | eui-b827ebfffef74e1a | 1691543595 | 1 | -83 | 10,5 | undefined | undefined | undefined
test_04_02_19 | pycomarduino | 0058924AB98D5AD4 | 1 | 92 | WzVdIEQyMC8wNS8xOCB0MTI6MDAgVzAwMDAgVDAwMDAgPyAxICAgAA== | [5] D20/05/18 t12:00 W0000 T0000 ? 1 | 2020-06-18T17:59:54.367027428Z | 868,5 | LORA | SF7BW125 | 4/5 | undefined | eui-b827ebfffef74e1a | 1718371883 | 2 | -81 | 8 | undefined | undefined | undefined
test_04_02_19 | pycomarduino | 0058924AB98D5AD4 | 1 | 93 | WzJdIEQyMC8wNS8xOCB0MTI6MDAgVzAwMDAgVDAwMDAgPyAxICAgAA== | [2] D20/05/18 t12:00 W0000 T0000 ? 1 | 2020-06-18T18:03:11.425612212Z | 868,1 | LORA | SF7BW125 | 4/5 | undefined | eui-b827ebfffef74e1a | 1915397347 | 0 | -83 | 9,2 | undefined | undefined | undefined
test_04_02_19 | pycomarduino | 0058924AB98D5AD4 | 1 | 94 | WzNdIEQyMC8wNS8xOCB0MTI6MDAgVzAwMDAgVDAwMDAgPyAxICAgAA== | [3] D20/05/18 t12:00 W0000 T0000 ? 1 | 2020-06-18T18:03:42.11552109Z | 867,9 | LORA | SF7BW125 | 4/5 | undefined | eui-b827ebfffef74e1a | 1946121364 | 7 | -84 | 10 | undefined | undefined | undefined
test_04_02_19 | pycomarduino | 0058924AB98D5AD4 | 1 | 95 | WzRdIEQyMC8wNS8xOCB0MTI6MDAgVzAwMDAgVDAwMDAgPyAxICAgAA== | [4] D20/05/18 t12:00 W0000 T0000 ? 1 | 2020-06-18T18:04:27.537129745Z | 868,3 | LORA | SF7BW125 | 4/5 | undefined | eui-b827ebfffef74e1a | 1991544755 | 1 | -83 | 10,5 | undefined | undefined | undefined
test_04_02_19 | pycomarduino | 0058924AB98D5AD4 | 1 | 96 | WzVdIEQyMC8wNS8xOCB0MTI6MDAgVzAwMDAgVDAwMDAgPyAxICAgAA== | [5] D20/05/18 t12:00 W0000 T0000 ? 1 | 2020-06-18T18:04:54.368066878Z | 868,5 | LORA | SF7BW125 | 4/5 | undefined | eui-fcc23dfffe0b696a | 2927843331 | 2 | -113 | -5,5 | undefined | undefined | undefined | eui-b827ebfffef74e1a | 2018373483 | 2 | -83 | 8,2 | undefined | undefined | undefined
test_04_02_19 | pycomarduino | 0058924AB98D5AD4 | 1 | 97 | WzJdIEQyMC8wNS8xOCB0MTI6MDAgVzAwMDAgVDAwMDAgPyAxICAgAA== | [2] D20/05/18 t12:00 W0000 T0000 ? 1 | 2020-06-18T18:08:11.396343535Z | 868,1 | LORA | SF7BW125 | 4/5 | undefined | eui-b827ebfffef74e1a | 2215397395 | 0 | -84 | 10 | undefined | undefined | undefined
test_04_02_19 | pycomarduino | 0058924AB98D5AD4 | 1 | 98 | WzNdIEQyMC8wNS8xOCB0MTI6MDAgVzAwMDAgVDAwMDAgPyAxICAgAA== | [3] D20/05/18 t12:00 W0000 T0000 ? 1 | 2020-06-18T18:08:42.114275424Z | 867,1 | LORA | SF7BW125 | 4/5 | undefined | eui-fcc23dfffe0b696a | 3155589571 | 3 | -115 | -7 | undefined | undefined | undefined | eui-b827ebfffef74e1a | 2246119827 | 3 | -87 | 9,8 | undefined | undefined | undefined
test_04_02_19 | pycomarduino | 0058924AB98D5AD4 | 1 | 99 | WzRdIEQyMC8wNS8xOCB0MTI6MDAgVzAwMDAgVDAwMDAgPyAxICAgAA== | [4] D20/05/18 t12:00 W0000 T0000 ? 1 | 2020-06-18T18:09:27.545745984Z | 868,3 | LORA | SF7BW125 | 4/5 | undefined | eui-b827ebfffef74e1a | 2291544059 | 1 | -82 | 9,5 | undefined | undefined | undefined
test_04_02_19 | pycomarduino | 0058924AB98D5AD4 | 1 | 100 | WzVdIEQyMC8wNS8xOCB0MTI6MDAgVzAwMDAgVDAwMDAgPyAxICAgAA== | [5] D20/05/18 t12:00 W0000 T0000 ? 1 | 2020-06-18T18:09:54.366169412Z | 868,5 | LORA | SF7BW125 | 4/5 | undefined | eui-fcc23dfffe0b696a | 3227842643 | 2 | -112 | -1,5 | undefined | undefined | undefined | eui-b827ebfffef74e1a | 2318372931 | 2 | -81 | 8,5 | undefined | undefined | undefined
test_04_02_19 | pycomarduino | 0058924AB98D5AD4 | 1 | 101 | WzJdIEQyMC8wNS8xOCB0MTI6MDAgVzAwMDAgVDAwMDAgPyAxICAgAA== | [2] D20/05/18 t12:00 W0000 T0000 ? 1 | 2020-06-18T18:13:11.405432874Z | 868,1 | LORA | SF7BW125 | 4/5 | undefined | eui-b827ebfffef74e1a | 2515399539 | 0 | -82 | 8,8 | undefined | undefined | undefined
test_04_02_19 | pycomarduino | 0058924AB98D5AD4 | 1 | 102 | WzNdIEQyMC8wNS8xOCB0MTI6MDAgVzAwMDAgVDAwMDAgPyAxICAgAA== | [3] D20/05/18 t12:00 W0000 T0000 ? 1 | 2020-06-18T18:13:42.11454716Z | 867,3 | LORA | SF7BW125 | 4/5 | undefined | eui-fcc23dfffe0b696a | 3455589979 | 4 | -112 | -4,5 | undefined | undefined | undefined | eui-b827ebfffef74e1a | 2546120363 | 4 | -84 | 10,2 | undefined | undefined | undefined
test_04_02_19 | pycomarduino | 0058924AB98D5AD4 | 1 | 103 | WzRdIEQyMC8wNS8xOCB0MTI6MDAgVzAwMDAgVDAwMDAgPyAxICAgAA== | [4] D20/05/18 t12:00 W0000 T0000 ? 1 | 2020-06-18T18:14:27.553202222Z | 868,3 | LORA | SF7BW125 | 4/5 | undefined | eui-b827ebfffef74e1a | 2591545243 | 1 | -83 | 9,5 | undefined | undefined | undefined
test_04_02_19 | pycomarduino | 0058924AB98D5AD4 | 1 | 104 | WzVdIEQyMC8wNS8xOCB0MTI6MDAgVzAwMDAgVDAwMDAgPyAxICAgAA== | [5] D20/05/18 t12:00 W0000 T0000 ? 1 | 2020-06-18T18:14:54.37285885Z | 868,5 | LORA | SF7BW125 | 4/5 | undefined | eui-fcc23dfffe0b696a | 3527844027 | 2 | -112 | -2,5 | undefined | undefined | undefined | eui-b827ebfffef74e1a | 2618374443 | 2 | -82 | 7,8 | undefined | undefined | undefined
test_04_02_19 | pycomarduino | 0058924AB98D5AD4 | 1 | 105 | WzJdIEQyMC8wNS8xOCB0MTI6MDAgVzAwMDAgVDAwMDAgPyAxICAgAA== | [2] D20/05/18 t12:00 W0000 T0000 ? 1 | 2020-06-18T18:18:11.398065506Z | 868,1 | LORA | SF7BW125 | 4/5 | undefined | eui-b827ebfffef74e1a | 2815399667 | 0 | -84 | 9,2 | undefined | undefined | undefined
test_04_02_19 | pycomarduino | 0058924AB98D5AD4 | 1 | 106 | WzNdIEQyMC8wNS8xOCB0MTI6MDAgVzAwMDAgVDAwMDAgPyAxICAgAA== | [3] D20/05/18 t12:00 W0000 T0000 ? 1 | 2020-06-18T18:18:42.117357848Z | 867,5 | LORA | SF7BW125 | 4/5 | undefined | eui-fcc23dfffe0b696a | 3755588332 | 5 | -113 | -6 | undefined | undefined | undefined | eui-b827ebfffef74e1a | 2846118852 | 5 | -82 | 8,2 | undefined | undefined | undefined
test_04_02_19 | pycomarduino | 0058924AB98D5AD4 | 1 | 107 | WzRdIEQyMC8wNS8xOCB0MTI6MDAgVzAwMDAgVDAwMDAgPyAxICAgAA== | [4] D20/05/18 t12:00 W0000 T0000 ? 1 | 2020-06-18T18:19:27.540401481Z | 868,3 | LORA | SF7BW125 | 4/5 | undefined | eui-b827ebfffef74e1a | 2891544395 | 1 | -82 | 10 | undefined | undefined | undefined
test_04_02_19 | pycomarduino | 0058924AB98D5AD4 | 1 | 108 | WzVdIEQyMC8wNS8xOCB0MTI6MDAgVzAwMDAgVDAwMDAgPyAxICAgAA== | [5] D20/05/18 t12:00 W0000 T0000 ? 1 | 2020-06-18T18:19:54.375714808Z | 868,5 | LORA | SF7BW125 | 4/5 | undefined | eui-b827ebfffef74e1a | 2918374019 | 2 | -81 | 8 | undefined | undefined | undefined
test_04_02_19 | pycomarduino | 0058924AB98D5AD4 | 1 | 109 | WzJdIEQyMC8wNS8xOCB0MTI6MDAgVzAwMDAgVDAwMDAgPyAxICAgAA== | [2] D20/05/18 t12:00 W0000 T0000 ? 1 | 2020-06-18T18:23:11.394773039Z | 868,1 | LORA | SF7BW125 | 4/5 | undefined | eui-fcc23dfffe0a9698 | 4026888027 | 0 | -117 | -8 | undefined | undefined | undefined | eui-b827ebfffef74e1a | 3115399723 | 0 | -84 | 9,5 | undefined | undefined | undefined
test_04_02_19 | pycomarduino | 0058924AB98D5AD4 | 1 | 110 | WzNdIEQyMC8wNS8xOCB0MTI6MDAgVzAwMDAgVDAwMDAgPyAxICAgAA== | [3] D20/05/18 t12:00 W0000 T0000 ? 1 | 2020-06-18T18:23:42.10664806Z | 867,7 | LORA | SF7BW125 | 4/5 | undefined | eui-b827ebfffef74e1a | 3146117420 | 6 | -83 | 8,8 | undefined | undefined | undefined
test_04_02_19 | pycomarduino | 0058924AB98D5AD4 | 1 | 111 | WzRdIEQyMC8wNS8xOCB0MTI6MDAgVzAwMDAgVDAwMDAgPyAxICAgAA== | [4] D20/05/18 t12:00 W0000 T0000 ? 1 | 2020-06-18T18:24:27.536801097Z | 868,3 | LORA | SF7BW125 | 4/5 | undefined | eui-b827ebfffef74e1a | 3191543619 | 1 | -82 | 9,8 | undefined | undefined | undefined
test_04_02_19 | pycomarduino | 0058924AB98D5AD4 | 1 | 112 | WzVdIEQyMC8wNS8xOCB0MTI6MDAgVzAwMDAgVDAwMDAgPyAxICAgAA== | [5] D20/05/18 t12:00 W0000 T0000 ? 1 | 2020-06-18T18:24:54.363151219Z | 868,5 | LORA | SF7BW125 | 4/5 | undefined | eui-fcc23dfffe0b696a | 4127842811 | 2 | -112 | -1,8 | undefined | undefined | undefined | eui-b827ebfffef74e1a | 3218373491 | 2 | -83 | 7 | undefined | undefined | undefined
test_04_02_19 | pycomarduino | 0058924AB98D5AD4 | 1 | 113 | WzJdIEQyMC8wNS8xOCB0MTI6MDAgVzAwMDAgVDAwMDAgPyAxICAgAA== | [2] D20/05/18 t12:00 W0000 T0000 ? 1 | 2020-06-18T18:28:11.404484861Z | 868,1 | LORA | SF7BW125 | 4/5 | undefined | eui-b827ebfffef74e1a | 3415401859 | 0 | -82 | 8,5 | undefined | undefined | undefined
test_04_02_19 | pycomarduino | 0058924AB98D5AD4 | 1 | 114 | WzNdIEQyMC8wNS8xOCB0MTI6MDAgVzAwMDAgVDAwMDAgPyAxICAgAA== | [3] D20/05/18 t12:00 W0000 T0000 ? 1 | 2020-06-18T18:28:42.116459282Z | 867,9 | LORA | SF7BW125 | 4/5 | undefined | eui-fcc23dfffe0a9698 | 62638652 | 7 | -116 | -6 | undefined | undefined | undefined | eui-b827ebfffef74e1a | 3446117868 | 7 | -85 | 9,2 | undefined | undefined | undefined
test_04_02_19 | pycomarduino | 0058924AB98D5AD4 | 1 | 115 | WzRdIEQyMC8wNS8xOCB0MTI6MDAgVzAwMDAgVDAwMDAgPyAxICAgAA== | [4] D20/05/18 t12:00 W0000 T0000 ? 1 | 2020-06-18T18:29:27.541806417Z | 868,3 | LORA | SF7BW125 | 4/5 | undefined | eui-b827ebfffef74e1a | 3491544899 | 1 | -80 | 9,8 | undefined | undefined | undefined
test_04_02_19 | pycomarduino | 0058924AB98D5AD4 | 1 | 116 | WzVdIEQyMC8wNS8xOCB0MTI6MDAgVzAwMDAgVDAwMDAgPyAxICAgAA== | [5] D20/05/18 t12:00 W0000 T0000 ? 1 | 2020-06-18T18:29:54.367013539Z | 868,5 | LORA | SF7BW125 | 4/5 | undefined | eui-fcc23dfffe0b696a | 132876915 | 2 | -112 | -2,8 | undefined | undefined | undefined | eui-b827ebfffef74e1a | 3518375019 | 2 | -82 | 8 | undefined | undefined | undefined
test_04_02_19 | pycomarduino | 0058924AB98D5AD4 | 1 | 117 | WzJdIEQyMC8wNS8xOCB0MTI6MDAgVzAwMDAgVDAwMDAgPyAxICAgAA== | [2] D20/05/18 t12:00 W0000 T0000 ? 1 | 2020-06-18T18:33:11.400015776Z | 868,1 | LORA | SF7BW125 | 4/5 | undefined | eui-b827ebfffef74e1a | 3715401915 | 0 | -82 | 9 | undefined | undefined | undefined
test_04_02_19 | pycomarduino | 0058924AB98D5AD4 | 1 | 118 | WzNdIEQyMC8wNS8xOCB0MTI6MDAgVzAwMDAgVDAwMDAgPyAxICAgAA== | [3] D20/05/18 t12:00 W0000 T0000 ? 1 | 2020-06-18T18:33:42.107408996Z | 867,1 | LORA | SF7BW125 | 4/5 | undefined | eui-fcc23dfffe0b696a | 360618227 | 3 | -113 | -6,5 | undefined | undefined | undefined | eui-b827ebfffef74e1a | 3746116427 | 3 | -87 | 9,8 | undefined | undefined | undefined
test_04_02_19 | pycomarduino | 0058924AB98D5AD4 | 1 | 119 | WzRdIEQyMC8wNS8xOCB0MTI6MDAgVzAwMDAgVDAwMDAgPyAxICAgAA== | [4] D20/05/18 t12:00 W0000 T0000 ? 1 | 2020-06-18T18:34:27.535936932Z | 868,3 | LORA | SF7BW125 | 4/5 | undefined | eui-b827ebfffef74e1a | 3791544051 | 1 | -81 | 9,8 | undefined | undefined | undefined
test_04_02_19 | pycomarduino | 0058924AB98D5AD4 | 1 | 120 | WzVdIEQyMC8wNS8xOCB0MTI6MDAgVzAwMDAgVDAwMDAgPyAxICAgAA== | [5] D20/05/18 t12:00 W0000 T0000 ? 1 | 2020-06-18T18:34:54.370497558Z | 868,5 | LORA | SF7BW125 | 4/5 | undefined | eui-fcc23dfffe0b696a | 432876283 | 2 | -112 | -2 | undefined | undefined | undefined | eui-b827ebfffef74e1a | 3818374523 | 2 | -82 | 7,5 | undefined | undefined | undefined
test_04_02_19 | pycomarduino | 0058924AB98D5AD4 | 1 | 121 | WzJdIEQyMC8wNS8xOCB0MTI6MDAgVzAwMDAgVDAwMDAgPyAxICAgAA== | [2] D20/05/18 t12:00 W0000 T0000 ? 1 | 2020-06-18T18:38:11.408256652Z | 868,1 | LORA | SF7BW125 | 4/5 | undefined | eui-b827ebfffef74e1a | 4015401939 | 0 | -84 | 9,5 | undefined | undefined | undefined
test_04_02_19 | pycomarduino | 0058924AB98D5AD4 | 1 | 122 | WzNdIEQyMC8wNS8xOCB0MTI6MDAgVzAwMDAgVDAwMDAgPyAxICAgAA== | [3] D20/05/18 t12:00 W0000 T0000 ? 1 | 2020-06-18T18:38:42.105453688Z | 867,3 | LORA | SF7BW125 | 4/5 | undefined | eui-fcc23dfffe0b696a | 660616595 | 4 | -111 | -4 | undefined | undefined | undefined | eui-b827ebfffef74e1a | 4046114923 | 4 | -82 | 8,8 | undefined | undefined | undefined
test_04_02_19 | pycomarduino | 0058924AB98D5AD4 | 1 | 123 | WzRdIEQyMC8wNS8xOCB0MTI6MDAgVzAwMDAgVDAwMDAgPyAxICAgAA== | [4] D20/05/18 t12:00 W0000 T0000 ? 1 | 2020-06-18T18:39:27.533051303Z | 868,3 | LORA | SF7BW125 | 4/5 | undefined | eui-b827ebfffef74e1a | 4091543275 | 1 | -81 | 9,8 | undefined | undefined | undefined
test_04_02_19 | pycomarduino | 0058924AB98D5AD4 | 1 | 124 | WzVdIEQyMC8wNS8xOCB0MTI6MDAgVzAwMDAgVDAwMDAgPyAxICAgAA== | [5] D20/05/18 t12:00 W0000 T0000 ? 1 | 2020-06-18T18:39:54.366724335Z | 868,5 | LORA | SF7BW125 | 4/5 | undefined | eui-fcc23dfffe0b696a | 732875603 | 2 | -112 | -3 | undefined | undefined | undefined | eui-b827ebfffef74e1a | 4118373971 | 2 | -82 | 8 | undefined | undefined | undefined
test_04_02_19 | pycomarduino | 0058924AB98D5AD4 | 1 | 125 | WzJdIEQyMC8wNS8xOCB0MTI6MDAgVzAwMDAgVDAwMDAgPyAxICAgAA== | [2] D20/05/18 t12:00 W0000 T0000 ? 1 | 2020-06-18T18:43:11.403420953Z | 868,1 | LORA | SF7BW125 | 4/5 | undefined | eui-b827ebfffef74e1a | 20436803 | 0 | -84 | 10 | undefined | undefined | undefined
test_04_02_19 | pycomarduino | 0058924AB98D5AD4 | 1 | 126 | WzNdIEQyMC8wNS8xOCB0MTI6MDAgVzAwMDAgVDAwMDAgPyAxICAgAA== | [3] D20/05/18 t12:00 W0000 T0000 ? 1 | 2020-06-18T18:43:42.105677291Z | 867,5 | LORA | SF7BW125 | 4/5 | undefined | eui-fcc23dfffe0b696a | 960616884 | 5 | -111 | -7,5 | undefined | undefined | undefined | eui-b827ebfffef74e1a | 51148052 | 5 | -84 | 7,2 | undefined | undefined | undefined
test_04_02_19 | pycomarduino | 0058924AB98D5AD4 | 1 | 127 | WzRdIEQyMC8wNS8xOCB0MTI6MDAgVzAwMDAgVDAwMDAgPyAxICAgAA== | [4] D20/05/18 t12:00 W0000 T0000 ? 1 | 2020-06-18T18:44:27.538213809Z | 868,3 | LORA | SF7BW125 | 4/5 | undefined | eui-b827ebfffef74e1a | 96577203 | 1 | -82 | 10 | undefined | undefined | undefined
test_04_02_19 | pycomarduino | 0058924AB98D5AD4 | 1 | 128 | WzVdIEQyMC8wNS8xOCB0MTI6MDAgVzAwMDAgVDAwMDAgPyAxICAgAA== | [5] D20/05/18 t12:00 W0000 T0000 ? 1 | 2020-06-18T18:44:54.513919707Z | 868,5 | LORA | SF7BW125 | 4/5 | undefined | eui-fcc23dfffe0b696a | 1033023219 | 2 | -112 | -1,5 | undefined | undefined | undefined | eui-b827ebfffef74e1a | 123554419 | 2 | -81 | 8,2 | undefined | undefined | undefined
test_04_02_19 | pycomarduino | 0058924AB98D5AD4 | 1 | 129 | WzJdIEQyMC8wNS8xOCB0MTI6MDAgVzAwMDAgVDAwMDAgPyAxICAgAA== | [2] D20/05/18 t12:00 W0000 T0000 ? 1 | 2020-06-18T18:48:11.398562654Z | 868,1 | LORA | SF7BW125 | 4/5 | undefined | eui-fcc23dfffe0a9698 | 1231924203 | 0 | -117 | -7 | undefined | undefined | undefined | eui-b827ebfffef74e1a | 320436915 | 0 | -83 | 9,8 | undefined | undefined | undefined
test_04_02_19 | pycomarduino | 0058924AB98D5AD4 | 1 | 130 | WzNdIEQyMC8wNS8xOCB0MTI6MDAgVzAwMDAgVDAwMDAgPyAxICAgAA== | [3] D20/05/18 t12:00 W0000 T0000 ? 1 | 2020-06-18T18:48:42.108792396Z | 867,7 | LORA | SF7BW125 | 4/5 | undefined | eui-b827ebfffef74e1a | 351146668 | 6 | -85 | 12 | undefined | undefined | undefined
test_04_02_19 | pycomarduino | 0058924AB98D5AD4 | 1 | 131 | WzRdIEQyMC8wNS8xOCB0MTI6MDAgVzAwMDAgVDAwMDAgPyAxICAgAA== | [4] D20/05/18 t12:00 W0000 T0000 ? 1 | 2020-06-18T18:49:27.541519814Z | 868,3 | LORA | SF7BW125 | 4/5 | undefined | eui-b827ebfffef74e1a | 396576315 | 1 | -79 | 7,8 | undefined | undefined | undefined
test_04_02_19 | pycomarduino | 0058924AB98D5AD4 | 1 | 132 | WzVdIEQyMC8wNS8xOCB0MTI6MDAgVzAwMDAgVDAwMDAgPyAxICAgAA== | [5] D20/05/18 t12:00 W0000 T0000 ? 1 | 2020-06-18T18:49:54.36411984Z | 868,5 | LORA | SF7BW125 | 4/5 | undefined | eui-b827ebfffef74e1a | 423407755 | 2 | -80 | 8 | undefined | undefined | undefined
test_04_02_19 | pycomarduino | 0058924AB98D5AD4 | 1 | 133 | WzJdIEQyMC8wNS8xOCB0MTI6MDAgVzAwMDAgVDAwMDAgPyAxICAgAA== | [2] D20/05/18 t12:00 W0000 T0000 ? 1 | 2020-06-18T18:53:11.402602223Z | 868,1 | LORA | SF7BW125 | 4/5 | undefined | eui-b827ebfffef74e1a | 620438979 | 0 | -82 | 9,5 | undefined | undefined | undefined
test_04_02_19 | pycomarduino | 0058924AB98D5AD4 | 1 | 135 | WzRdIEQyMC8wNS8xOCB0MTI6MDAgVzAwMDAgVDAwMDAgPyAxICAgAA== | [4] D20/05/18 t12:00 W0000 T0000 ? 1 | 2020-06-18T18:54:27.547621386Z | 868,3 | LORA | SF7BW125 | 4/5 | undefined | eui-b827ebfffef74e1a | 696577571 | 1 | -80 | 9,8 | undefined | undefined | undefined
test_04_02_19 | pycomarduino | 0058924AB98D5AD4 | 1 | 136 | WzVdIEQyMC8wNS8xOCB0MTI6MDAgVzAwMDAgVDAwMDAgPyAxICAgAA== | [5] D20/05/18 t12:00 W0000 T0000 ? 1 | 2020-06-18T18:54:54.36951569Z | 868,5 | LORA | SF7BW125 | 4/5 | undefined | eui-fcc23dfffe0b696a | 1632877795 | 2 | -112 | -2 | undefined | undefined | undefined | eui-b827ebfffef74e1a | 723409259 | 2 | -82 | 7,2 | undefined | undefined | undefined
test_04_02_19 | pycomarduino | 0058924AB98D5AD4 | 1 | 137 | WzJdIEQyMC8wNS8xOCB0MTI6MDAgVzAwMDAgVDAwMDAgPyAxICAgAA== | [2] D20/05/18 t12:00 W0000 T0000 ? 1 | 2020-06-18T18:58:11.399746906Z | 868,1 | LORA | SF7BW125 | 4/5 | undefined | eui-b827ebfffef74e1a | 920439019 | 0 | -84 | 9,2 | undefined | undefined | undefined
test_04_02_19 | pycomarduino | 0058924AB98D5AD4 | 1 | 138 | WzNdIEQyMC8wNS8xOCB0MTI6MDAgVzAwMDAgVDAwMDAgPyAxICAgAA== | [3] D20/05/18 t12:00 W0000 T0000 ? 1 | 2020-06-18T18:58:42.104131162Z | 867,1 | LORA | SF7BW125 | 4/5 | undefined | eui-fcc23dfffe0b696a | 1860614123 | 3 | -113 | -7 | undefined | undefined | undefined | eui-b827ebfffef74e1a | 951145691 | 3 | -85 | 9,2 | undefined | undefined | undefined
test_04_02_19 | pycomarduino | 0058924AB98D5AD4 | 1 | 139 | WzRdIEQyMC8wNS8xOCB0MTI6MDAgVzAwMDAgVDAwMDAgPyAxICAgAA== | [4] D20/05/18 t12:00 W0000 T0000 ? 1 | 2020-06-18T18:59:27.542004867Z | 868,3 | LORA | SF7BW125 | 4/5 | undefined | eui-b827ebfffef74e1a | 996576771 | 1 | -82 | 10 | undefined | undefined | undefined
test_04_02_19 | pycomarduino | 0058924AB98D5AD4 | 1 | 140 | WzVdIEQyMC8wNS8xOCB0MTI6MDAgVzAwMDAgVDAwMDAgPyAxICAgAA== | [5] D20/05/18 t12:00 W0000 T0000 ? 1 | 2020-06-18T18:59:54.365738172Z | 868,5 | LORA | SF7BW125 | 4/5 | undefined | eui-fcc23dfffe0b696a | 1932877115 | 2 | -112 | -7,5 | undefined | undefined | undefined | eui-b827ebfffef74e1a | 1023408707 | 2 | -82 | 8 | undefined | undefined | undefined
test_04_02_19 | pycomarduino | 0058924AB98D5AD4 | 1 | 141 | WzJdIEQyMC8wNS8xOCB0MTI6MDAgVzAwMDAgVDAwMDAgPyAxICAgAA== | [2] D20/05/18 t12:00 W0000 T0000 ? 1 | 2020-06-18T19:03:11.400245689Z | 868,1 | LORA | SF7BW125 | 4/5 | undefined | eui-fcc23dfffe0a9698 | 2131925835 | 0 | -117 | -6,5 | undefined | undefined | undefined | eui-b827ebfffef74e1a | 1220439147 | 0 | -82 | 9 | undefined | undefined | undefined
test_04_02_19 | pycomarduino | 0058924AB98D5AD4 | 1 | 142 | WzNdIEQyMC8wNS8xOCB0MTI6MDAgVzAwMDAgVDAwMDAgPyAxICAgAA== | [3] D20/05/18 t12:00 W0000 T0000 ? 1 | 2020-06-18T19:03:42.103124945Z | 867,3 | LORA | SF7BW125 | 4/5 | undefined | eui-fcc23dfffe0b696a | 2160612443 | 4 | -112 | -2,8 | undefined | undefined | undefined | eui-b827ebfffef74e1a | 1251144139 | 4 | -84 | 10 | undefined | undefined | undefined
test_04_02_19 | pycomarduino | 0058924AB98D5AD4 | 1 | 143 | WzRdIEQyMC8wNS8xOCB0MTI6MDAgVzAwMDAgVDAwMDAgPyAxICAgAA== | [4] D20/05/18 t12:00 W0000 T0000 ? 1 | 2020-06-18T19:04:27.67346271Z | 868,3 | LORA | SF7BW125 | 4/5 | undefined | eui-b827ebfffef74e1a | 1296575979 | 1 | -81 | 9,2 | undefined | undefined | undefined
test_04_02_19 | pycomarduino | 0058924AB98D5AD4 | 1 | 144 | WzVdIEQyMC8wNS8xOCB0MTI6MDAgVzAwMDAgVDAwMDAgPyAxICAgAA== | [5] D20/05/18 t12:00 W0000 T0000 ? 1 | 2020-06-18T19:04:54.366862956Z | 868,5 | LORA | SF7BW125 | 4/5 | undefined | eui-fcc23dfffe0b696a | 2232876443 | 2 | -111 | -2,5 | undefined | undefined | undefined | eui-b827ebfffef74e1a | 1323408163 | 2 | -79 | 7,8 | undefined | undefined | undefined
test_04_02_19 | pycomarduino | 0058924AB98D5AD4 | 1 | 145 | WzJdIEQyMC8wNS8xOCB0MTI6MDAgVzAwMDAgVDAwMDAgPyAxICAgAA== | [2] D20/05/18 t12:00 W0000 T0000 ? 1 | 2020-06-18T19:08:11.398460272Z | 868,1 | LORA | SF7BW125 | 4/5 | undefined | eui-fcc23dfffe0a9698 | 2431927731 | 0 | -117 | -7 | undefined | undefined | undefined | eui-b827ebfffef74e1a | 1520441251 | 0 | -82 | 9,5 | undefined | undefined | undefined
test_04_02_19 | pycomarduino | 0058924AB98D5AD4 | 1 | 146 | WzNdIEQyMC8wNS8xOCB0MTI6MDAgVzAwMDAgVDAwMDAgPyAxICAgAA== | [3] D20/05/18 t12:00 W0000 T0000 ? 1 | 2020-06-18T19:08:42.104267429Z | 867,5 | LORA | SF7BW125 | 4/5 | undefined | eui-fcc23dfffe0b696a | 2460612860 | 5 | -112 | -4,8 | undefined | undefined | undefined | eui-b827ebfffef74e1a | 1551144692 | 5 | -85 | 7,5 | undefined | undefined | undefined
test_04_02_19 | pycomarduino | 0058924AB98D5AD4 | 1 | 147 | WzRdIEQyMC8wNS8xOCB0MTI6MDAgVzAwMDAgVDAwMDAgPyAxICAgAA== | [4] D20/05/18 t12:00 W0000 T0000 ? 1 | 2020-06-18T19:09:27.537465332Z | 868,3 | LORA | SF7BW125 | 4/5 | undefined | eui-b827ebfffef74e1a | 1596577123 | 1 | -80 | 9,8 | undefined | undefined | undefined
test_04_02_19 | pycomarduino | 0058924AB98D5AD4 | 1 | 148 | WzVdIEQyMC8wNS8xOCB0MTI6MDAgVzAwMDAgVDAwMDAgPyAxICAgAA== | [5] D20/05/18 t12:00 W0000 T0000 ? 1 | 2020-06-18T19:09:54.371828942Z | 868,5 | LORA | SF7BW125 | 4/5 | undefined | eui-fcc23dfffe0b696a | 2532877915 | 2 | -112 | -1,2 | undefined | undefined | undefined | eui-b827ebfffef74e1a | 1623409779 | 2 | -81 | 7,5 | undefined | undefined | undefined
test_04_02_19 | pycomarduino | 0058924AB98D5AD4 | 1 | 149 | WzJdIEQyMC8wNS8xOCB0MTI6MDAgVzAwMDAgVDAwMDAgPyAxICAgAA== | [2] D20/05/18 t12:00 W0000 T0000 ? 1 | 2020-06-18T19:13:11.409861496Z | 868,1 | LORA | SF7BW125 | 4/5 | undefined | eui-b827ebfffef74e1a | 1820441371 | 0 | -82 | 9 | undefined | undefined | undefined
test_04_02_19 | pycomarduino | 0058924AB98D5AD4 | 1 | 150 | WzNdIEQyMC8wNS8xOCB0MTI6MDAgVzAwMDAgVDAwMDAgPyAxICAgAA== | [3] D20/05/18 t12:00 W0000 T0000 ? 1 | 2020-06-18T19:13:42.106854506Z | 867,7 | LORA | SF7BW125 | 4/5 | undefined | eui-b827ebfffef74e1a | 1851143140 | 6 | -83 | 9,5 | undefined | undefined | undefined
test_04_02_19 | pycomarduino | 0058924AB98D5AD4 | 1 | 151 | WzRdIEQyMC8wNS8xOCB0MTI6MDAgVzAwMDAgVDAwMDAgPyAxICAgAA== | [4] D20/05/18 t12:00 W0000 T0000 ? 1 | 2020-06-18T19:14:27.535238068Z | 868,3 | LORA | SF7BW125 | 4/5 | undefined | eui-b827ebfffef74e1a | 1896576315 | 1 | -83 | 9,8 | undefined | undefined | undefined
test_04_02_19 | pycomarduino | 0058924AB98D5AD4 | 1 | 152 | WzVdIEQyMC8wNS8xOCB0MTI6MDAgVzAwMDAgVDAwMDAgPyAxICAgAA== | [5] D20/05/18 t12:00 W0000 T0000 ? 1 | 2020-06-18T19:14:54.371114777Z | 868,5 | LORA | SF7BW125 | 4/5 | undefined | eui-fcc23dfffe0b696a | 2832877235 | 2 | -110 | -1 | undefined | undefined | undefined | eui-b827ebfffef74e1a | 1923409227 | 2 | -80 | 7,8 | undefined | undefined | undefined
test_04_02_19 | pycomarduino | 0058924AB98D5AD4 | 1 | 153 | WzJdIEQyMC8wNS8xOCB0MTI6MDAgVzAwMDAgVDAwMDAgPyAxICAgAA== | [2] D20/05/18 t12:00 W0000 T0000 ? 1 | 2020-06-18T19:18:11.399223661Z | 868,1 | LORA | SF7BW125 | 4/5 | undefined | eui-fcc23dfffe0a9698 | 3031927483 | 0 | -117 | -7,8 | undefined | undefined | undefined | eui-b827ebfffef74e1a | 2120441403 | 0 | -83 | 9,5 | undefined | undefined | undefined
test_04_02_19 | pycomarduino | 0058924AB98D5AD4 | 1 | 154 | WzNdIEQyMC8wNS8xOCB0MTI6MDAgVzAwMDAgVDAwMDAgPyAxICAgAA== | [3] D20/05/18 t12:00 W0000 T0000 ? 1 | 2020-06-18T19:18:42.103425475Z | 867,9 | LORA | SF7BW125 | 4/5 | undefined | eui-fcc23dfffe0a9698 | 3062627668 | 7 | -115 | -5,8 | undefined | undefined | undefined | eui-b827ebfffef74e1a | 2151141612 | 7 | -84 | 9,8 | undefined | undefined | undefined
test_04_02_19 | pycomarduino | 0058924AB98D5AD4 | 1 | 155 | WzRdIEQyMC8wNS8xOCB0MTI6MDAgVzAwMDAgVDAwMDAgPyAxICAgAA== | [4] D20/05/18 t12:00 W0000 T0000 ? 1 | 2020-06-18T19:19:27.537978639Z | 868,3 | LORA | SF7BW125 | 4/5 | undefined | eui-b827ebfffef74e1a | 2196575547 | 1 | -83 | 10,2 | undefined | undefined | undefined
test_04_02_19 | pycomarduino | 0058924AB98D5AD4 | 1 | 156 | WzVdIEQyMC8wNS8xOCB0MTI6MDAgVzAwMDAgVDAwMDAgPyAxICAgAA== | [5] D20/05/18 t12:00 W0000 T0000 ? 1 | 2020-06-18T19:19:54.370562947Z | 868,5 | LORA | SF7BW125 | 4/5 | undefined | eui-fcc23dfffe0b696a | 3132876571 | 2 | -112 | -2 | undefined | undefined | undefined | eui-b827ebfffef74e1a | 2223408699 | 2 | -82 | 7,8 | undefined | undefined | undefined
test_04_02_19 | pycomarduino | 0058924AB98D5AD4 | 1 | 157 | WzJdIEQyMC8wNS8xOCB0MTI6MDAgVzAwMDAgVDAwMDAgPyAxICAgAA== | [2] D20/05/18 t12:00 W0000 T0000 ? 1 | 2020-06-18T19:23:11.399967331Z | 868,1 | LORA | SF7BW125 | 4/5 | undefined | eui-b827ebfffef74e1a | 2420443563 | 0 | -82 | 9 | undefined | undefined | undefined
test_04_02_19 | pycomarduino | 0058924AB98D5AD4 | 1 | 158 | WzNdIEQyMC8wNS8xOCB0MTI6MDAgVzAwMDAgVDAwMDAgPyAxICAgAA== | [3] D20/05/18 t12:00 W0000 T0000 ? 1 | 2020-06-18T19:23:42.102097844Z | 867,1 | LORA | SF7BW125 | 4/5 | undefined | eui-fcc23dfffe0b696a | 3360609971 | 3 | -113 | -4,5 | undefined | undefined | undefined | eui-b827ebfffef74e1a | 2451142195 | 3 | -85 | 9,2 | undefined | undefined | undefined
test_04_02_19 | pycomarduino | 0058924AB98D5AD4 | 1 | 159 | WzRdIEQyMC8wNS8xOCB0MTI6MDAgVzAwMDAgVDAwMDAgPyAxICAgAA== | [4] D20/05/18 t12:00 W0000 T0000 ? 1 | 2020-06-18T19:24:27.53907501Z | 868,3 | LORA | SF7BW125 | 4/5 | undefined | eui-b827ebfffef74e1a | 2496576707 | 1 | -82 | 10,8 | undefined | undefined | undefined
test_04_02_19 | pycomarduino | 0058924AB98D5AD4 | 1 | 160 | WzVdIEQyMC8wNS8xOCB0MTI6MDAgVzAwMDAgVDAwMDAgPyAxICAgAA== | [5] D20/05/18 t12:00 W0000 T0000 ? 1 | 2020-06-18T19:24:54.371682617Z | 868,5 | LORA | SF7BW125 | 4/5 | undefined | eui-fcc23dfffe0b696a | 3432877987 | 2 | -113 | -3,5 | undefined | undefined | undefined | eui-b827ebfffef74e1a | 2523410251 | 2 | -81 | 7,8 | undefined | undefined | undefined
test_04_02_19 | pycomarduino | 0058924AB98D5AD4 | 1 | 161 | WzJdIEQyMC8wNS8xOCB0MTI6MDAgVzAwMDAgVDAwMDAgPyAxICAgAA== | [2] D20/05/18 t12:00 W0000 T0000 ? 1 | 2020-06-18T19:28:11.406092646Z | 868,1 | LORA | SF7BW125 | 4/5 | undefined | eui-b827ebfffef74e1a | 2720443603 | 0 | -84 | 9,8 | undefined | undefined | undefined
test_04_02_19 | pycomarduino | 0058924AB98D5AD4 | 1 | 162 | WzNdIEQyMC8wNS8xOCB0MTI6MDAgVzAwMDAgVDAwMDAgPyAxICAgAA== | [3] D20/05/18 t12:00 W0000 T0000 ? 1 | 2020-06-18T19:28:42.101544324Z | 867,3 | LORA | SF7BW125 | 4/5 | undefined | eui-fcc23dfffe0b696a | 3660608299 | 4 | -112 | -4,5 | undefined | undefined | undefined | eui-b827ebfffef74e1a | 2751140659 | 4 | -84 | 9,2 | undefined | undefined | undefined
test_04_02_19 | pycomarduino | 0058924AB98D5AD4 | 1 | 163 | WzRdIEQyMC8wNS8xOCB0MTI6MDAgVzAwMDAgVDAwMDAgPyAxICAgAA== | [4] D20/05/18 t12:00 W0000 T0000 ? 1 | 2020-06-18T19:29:27.569293274Z | 868,3 | LORA | SF7BW125 | 4/5 | undefined | eui-b827ebfffef74e1a | 2796575907 | 1 | -80 | 10 | undefined | undefined | undefined
test_04_02_19 | pycomarduino | 0058924AB98D5AD4 | 1 | 164 | WzVdIEQyMC8wNS8xOCB0MTI6MDAgVzAwMDAgVDAwMDAgPyAxICAgAA== | [5] D20/05/18 t12:00 W0000 T0000 ? 1 | 2020-06-18T19:29:54.366460039Z | 868,5 | LORA | SF7BW125 | 4/5 | undefined | eui-fcc23dfffe0b696a | 3732877235 | 2 | -112 | -2,8 | undefined | undefined | undefined | eui-b827ebfffef74e1a | 2823409627 | 2 | -83 | 8 | undefined | undefined | undefined
test_04_02_19 | pycomarduino | 0058924AB98D5AD4 | 1 | 165 | WzJdIEQyMC8wNS8xOCB0MTI6MDAgVzAwMDAgVDAwMDAgPyAxICAgAA== | [2] D20/05/18 t12:00 W0000 T0000 ? 1 | 2020-06-18T19:33:11.414879299Z | 868,1 | LORA | SF7BW125 | 4/5 | undefined | eui-b827ebfffef74e1a | 3020445699 | 0 | -84 | 8,2 | undefined | undefined | undefined
test_04_02_19 | pycomarduino | 0058924AB98D5AD4 | 1 | 166 | WzNdIEQyMC8wNS8xOCB0MTI6MDAgVzAwMDAgVDAwMDAgPyAxICAgAA== | [3] D20/05/18 t12:00 W0000 T0000 ? 1 | 2020-06-18T19:33:42.100583473Z | 867,5 | LORA | SF7BW125 | 4/5 | undefined | eui-fcc23dfffe0b696a | 3960608572 | 5 | -112 | -8,2 | undefined | undefined | undefined | eui-b827ebfffef74e1a | 3051141068 | 5 | -85 | 7,8 | undefined | undefined | undefined
test_04_02_19 | pycomarduino | 0058924AB98D5AD4 | 1 | 167 | WzRdIEQyMC8wNS8xOCB0MTI6MDAgVzAwMDAgVDAwMDAgPyAxICAgAA== | [4] D20/05/18 t12:00 W0000 T0000 ? 1 | 2020-06-18T19:34:27.536401408Z | 868,3 | LORA | SF7BW125 | 4/5 | undefined | eui-b827ebfffef74e1a | 3096577163 | 1 | -81 | 9,2 | undefined | undefined | undefined
test_04_02_19 | pycomarduino | 0058924AB98D5AD4 | 1 | 168 | WzVdIEQyMC8wNS8xOCB0MTI6MDAgVzAwMDAgVDAwMDAgPyAxICAgAA== | [5] D20/05/18 t12:00 W0000 T0000 ? 1 | 2020-06-18T19:34:54.380553295Z | 868,5 | LORA | SF7BW125 | 4/5 | undefined | eui-b827ebfffef74e1a | 3123411227 | 2 | -80 | 8,2 | undefined | undefined | undefined
test_04_02_19 | pycomarduino | 0058924AB98D5AD4 | 1 | 169 | WzJdIEQyMC8wNS8xOCB0MTI6MDAgVzAwMDAgVDAwMDAgPyAxICAgAA== | [2] D20/05/18 t12:00 W0000 T0000 ? 1 | 2020-06-18T19:38:11.410303946Z | 868,1 | LORA | SF7BW125 | 4/5 | undefined | eui-b827ebfffef74e1a | 3320445651 | 0 | -82 | 8,5 | undefined | undefined | undefined
test_04_02_19 | pycomarduino | 0058924AB98D5AD4 | 1 | 170 | WzNdIEQyMC8wNS8xOCB0MTI6MDAgVzAwMDAgVDAwMDAgPyAxICAgAA== | [3] D20/05/18 t12:00 W0000 T0000 ? 1 | 2020-06-18T19:38:42.104387724Z | 867,7 | LORA | SF7BW125 | 4/5 | undefined | eui-b827ebfffef74e1a | 3351139628 | 6 | -84 | 9 | undefined | undefined | undefined
test_04_02_19 | pycomarduino | 0058924AB98D5AD4 | 1 | 171 | WzRdIEQyMC8wNS8xOCB0MTI6MDAgVzAwMDAgVDAwMDAgPyAxICAgAA== | [4] D20/05/18 t12:00 W0000 T0000 ? 1 | 2020-06-18T19:39:27.537622658Z | 868,3 | LORA | SF7BW125 | 4/5 | undefined | eui-b827ebfffef74e1a | 3396576267 | 1 | -83 | 9,5 | undefined | undefined | undefined
test_04_02_19 | pycomarduino | 0058924AB98D5AD4 | 1 | 172 | WzVdIEQyMC8wNS8xOCB0MTI6MDAgVzAwMDAgVDAwMDAgPyAxICAgAA== | [5] D20/05/18 t12:00 W0000 T0000 ? 1 | 2020-06-18T19:39:54.368328039Z | 868,5 | LORA | SF7BW125 | 4/5 | undefined | eui-b827ebfffef74e1a | 3423410699 | 2 | -80 | 8,8 | undefined | undefined | undefined
test_04_02_19 | pycomarduino | 0058924AB98D5AD4 | 1 | 173 | WzJdIEQyMC8wNS8xOCB0MTI6MDAgVzAwMDAgVDAwMDAgPyAxICAgAA== | [2] D20/05/18 t12:00 W0000 T0000 ? 1 | 2020-06-18T19:43:11.402189092Z | 868,1 | LORA | SF7BW125 | 4/5 | undefined | eui-b827ebfffef74e1a | 3620445859 | 0 | -84 | 10,2 | undefined | undefined | undefined
test_04_02_19 | pycomarduino | 0058924AB98D5AD4 | 1 | 174 | WzNdIEQyMC8wNS8xOCB0MTI6MDAgVzAwMDAgVDAwMDAgPyAxICAgAA== | [3] D20/05/18 t12:00 W0000 T0000 ? 1 | 2020-06-18T19:43:42.102328972Z | 867,9 | LORA | SF7BW125 | 4/5 | undefined | eui-fcc23dfffe0a9698 | 267655820 | 7 | -115 | -6,8 | undefined | undefined | undefined | eui-b827ebfffef74e1a | 3651138076 | 7 | -84 | 9,5 | undefined | undefined | undefined
test_04_02_19 | pycomarduino | 0058924AB98D5AD4 | 1 | 175 | WzRdIEQyMC8wNS8xOCB0MTI6MDAgVzAwMDAgVDAwMDAgPyAxICAgAA== | [4] D20/05/18 t12:00 W0000 T0000 ? 1 | 2020-06-18T19:44:27.539398108Z | 868,3 | LORA | SF7BW125 | 4/5 | undefined | eui-b827ebfffef74e1a | 3696575491 | 1 | -80 | 9,5 | undefined | undefined | undefined
test_04_02_19 | pycomarduino | 0058924AB98D5AD4 | 1 | 176 | WzVdIEQyMC8wNS8xOCB0MTI6MDAgVzAwMDAgVDAwMDAgPyAxICAgAA== | [5] D20/05/18 t12:00 W0000 T0000 ? 1 | 2020-06-18T19:44:54.371255068Z | 868,5 | LORA | SF7BW125 | 4/5 | undefined | eui-fcc23dfffe0b696a | 337910091 | 2 | -111 | -1,2 | undefined | undefined | undefined | eui-b827ebfffef74e1a | 3723410179 | 2 | -82 | 8 | undefined | undefined | undefined
test_04_02_19 | pycomarduino | 0058924AB98D5AD4 | 1 | 177 | WzJdIEQyMC8wNS8xOCB0MTI6MDAgVzAwMDAgVDAwMDAgPyAxICAgAA== | [2] D20/05/18 t12:00 W0000 T0000 ? 1 | 2020-06-18T19:48:11.409306253Z | 868,1 | LORA | SF7BW125 | 4/5 | undefined | eui-fcc23dfffe0b696a | 534947771 | 0 | -115 | -7,5 | undefined | undefined | undefined | eui-b827ebfffef74e1a | 3920447947 | 0 | -83 | 10 | undefined | undefined | undefined
test_04_02_19 | pycomarduino | 0058924AB98D5AD4 | 1 | 178 | WzNdIEQyMC8wNS8xOCB0MTI6MDAgVzAwMDAgVDAwMDAgPyAxICAgAA== | [3] D20/05/18 t12:00 W0000 T0000 ? 1 | 2020-06-18T19:48:42.096884599Z | 867,1 | LORA | SF7BW125 | 4/5 | undefined | eui-fcc23dfffe0b696a | 565638475 | 3 | -115 | -5,5 | undefined | undefined | undefined | eui-b827ebfffef74e1a | 3951138651 | 3 | -83 | 9,2 | undefined | undefined | undefined
test_04_02_19 | pycomarduino | 0058924AB98D5AD4 | 1 | 179 | WzRdIEQyMC8wNS8xOCB0MTI6MDAgVzAwMDAgVDAwMDAgPyAxICAgAA== | [4] D20/05/18 t12:00 W0000 T0000 ? 1 | 2020-06-18T19:49:27.534468595Z | 868,3 | LORA | SF7BW125 | 4/5 | undefined | eui-b827ebfffef74e1a | 3996576683 | 1 | -83 | 9,8 | undefined | undefined | undefined
test_04_02_19 | pycomarduino | 0058924AB98D5AD4 | 1 | 180 | WzVdIEQyMC8wNS8xOCB0MTI6MDAgVzAwMDAgVDAwMDAgPyAxICAgAA== | [5] D20/05/18 t12:00 W0000 T0000 ? 1 | 2020-06-18T19:49:54.370092178Z | 868,5 | LORA | SF7BW125 | 4/5 | undefined | eui-fcc23dfffe0b696a | 637911491 | 2 | -111 | -2 | undefined | undefined | undefined | eui-b827ebfffef74e1a | 4023411707 | 2 | -81 | 7,8 | undefined | undefined | undefined
test_04_02_19 | pycomarduino | 0058924AB98D5AD4 | 1 | 181 | WzJdIEQyMC8wNS8xOCB0MTI6MDAgVzAwMDAgVDAwMDAgPyAxICAgAA== | [2] D20/05/18 t12:00 W0000 T0000 ? 1 | 2020-06-18T19:53:11.694833594Z | 868,1 | LORA | SF7BW125 | 4/5 | undefined | eui-b827ebfffef74e1a | 4220447907 | 0 | -84 | 10 | undefined | undefined | undefined
test_04_02_19 | pycomarduino | 0058924AB98D5AD4 | 1 | 182 | WzNdIEQyMC8wNS8xOCB0MTI6MDAgVzAwMDAgVDAwMDAgPyAxICAgAA== | [3] D20/05/18 t12:00 W0000 T0000 ? 1 | 2020-06-18T19:53:42.096303009Z | 867,3 | LORA | SF7BW125 | 4/5 | undefined | eui-fcc23dfffe0b696a | 865636795 | 4 | -113 | -5,8 | undefined | undefined | undefined | eui-b827ebfffef74e1a | 4251137115 | 4 | -85 | 10,5 | undefined | undefined | undefined
test_04_02_19 | pycomarduino | 0058924AB98D5AD4 | 1 | 183 | WzRdIEQyMC8wNS8xOCB0MTI6MDAgVzAwMDAgVDAwMDAgPyAxICAgAA== | [4] D20/05/18 t12:00 W0000 T0000 ? 1 | 2020-06-18T19:54:27.531337305Z | 868,3 | LORA | SF7BW125 | 4/5 | undefined | eui-b827ebfffef74e1a | 1608507 | 1 | -81 | 9,8 | undefined | undefined | undefined
test_04_02_19 | pycomarduino | 0058924AB98D5AD4 | 1 | 184 | WzVdIEQyMC8wNS8xOCB0MTI6MDAgVzAwMDAgVDAwMDAgPyAxICAgAA== | [5] D20/05/18 t12:00 W0000 T0000 ? 1 | 2020-06-18T19:54:54.371277689Z | 868,5 | LORA | SF7BW125 | 4/5 | undefined | eui-fcc23dfffe0b696a | 937910803 | 2 | -112 | -1,8 | undefined | undefined | undefined | eui-b827ebfffef74e1a | 28443859 | 2 | -82 | 7,8 | undefined | undefined | undefined
test_04_02_19 | pycomarduino | 0058924AB98D5AD4 | 1 | 185 | WzJdIEQyMC8wNS8xOCB0MTI6MDAgVzAwMDAgVDAwMDAgPyAxICAgAA== | [2] D20/05/18 t12:00 W0000 T0000 ? 1 | 2020-06-18T19:58:11.409727174Z | 868,1 | LORA | SF7BW125 | 4/5 | undefined | eui-b827ebfffef74e1a | 225480811 | 0 | -82 | 9,2 | undefined | undefined | undefined
test_04_02_19 | pycomarduino | 0058924AB98D5AD4 | 1 | 186 | WzNdIEQyMC8wNS8xOCB0MTI6MDAgVzAwMDAgVDAwMDAgPyAxICAgAA== | [3] D20/05/18 t12:00 W0000 T0000 ? 1 | 2020-06-18T19:58:42.098112321Z | 867,5 | LORA | SF7BW125 | 4/5 | undefined | eui-b827ebfffef74e1a | 256168268 | 5 | -83 | 8 | undefined | undefined | undefined
test_04_02_19 | pycomarduino | 0058924AB98D5AD4 | 1 | 187 | WzRdIEQyMC8wNS8xOCB0MTI6MDAgVzAwMDAgVDAwMDAgPyAxICAgAA== | [4] D20/05/18 t12:00 W0000 T0000 ? 1 | 2020-06-18T19:59:27.533416616Z | 868,3 | LORA | SF7BW125 | 4/5 | undefined | eui-b827ebfffef74e1a | 301607723 | 1 | -83 | 10,2 | undefined | undefined | undefined
test_04_02_19 | pycomarduino | 0058924AB98D5AD4 | 1 | 188 | WzVdIEQyMC8wNS8xOCB0MTI6MDAgVzAwMDAgVDAwMDAgPyAxICAgAA== | [5] D20/05/18 t12:00 W0000 T0000 ? 1 | 2020-06-18T19:59:54.3701105Z | 868,5 | LORA | SF7BW125 | 4/5 | undefined | eui-fcc23dfffe0b696a | 1237910211 | 2 | -111 | -2,8 | undefined | undefined | undefined | eui-b827ebfffef74e1a | 328443403 | 2 | -81 | 7,8 | undefined | undefined | undefined
test_04_02_19 | pycomarduino | 0058924AB98D5AD4 | 1 | 189 | WzJdIEQyMC8wNS8xOCB0MTI6MDAgVzAwMDAgVDAwMDAgPyAxICAgAA== | [2] D20/05/18 t12:00 W0000 T0000 ? 1 | 2020-06-18T20:03:12.197075265Z | 868,1 | LORA | SF7BW125 | 4/5 | undefined | eui-b827ebfffef74e1a | 525482875 | 0 | -82 | 9,2 | undefined | undefined | undefined
test_04_02_19 | pycomarduino | 0058924AB98D5AD4 | 1 | 190 | WzNdIEQyMC8wNS8xOCB0MTI6MDAgVzAwMDAgVDAwMDAgPyAxICAgAA== | [3] D20/05/18 t12:00 W0000 T0000 ? 1 | 2020-06-18T20:03:42.096854398Z | 867,7 | LORA | SF7BW125 | 4/5 | undefined | eui-fcc23dfffe0b696a | 1465635516 | 6 | -111 | -8 | undefined | undefined | undefined | eui-b827ebfffef74e1a | 556168804 | 6 | -83 | 9,2 | undefined | undefined | undefined
test_04_02_19 | pycomarduino | 0058924AB98D5AD4 | 1 | 191 | WzRdIEQyMC8wNS8xOCB0MTI6MDAgVzAwMDAgVDAwMDAgPyAxICAgAA== | [4] D20/05/18 t12:00 W0000 T0000 ? 1 | 2020-06-18T20:04:27.533657768Z | 868,3 | LORA | SF7BW125 | 4/5 | undefined | eui-b827ebfffef74e1a | 601608891 | 1 | -83 | 10,8 | undefined | undefined | undefined
test_04_02_19 | pycomarduino | 0058924AB98D5AD4 | 1 | 192 | WzVdIEQyMC8wNS8xOCB0MTI6MDAgVzAwMDAgVDAwMDAgPyAxICAgAA== | [5] D20/05/18 t12:00 W0000 T0000 ? 1 | 2020-06-18T20:04:54.367526194Z | 868,5 | LORA | SF7BW125 | 4/5 | undefined | eui-fcc23dfffe0b696a | 1537911579 | 2 | -111 | -4,2 | undefined | undefined | undefined | eui-b827ebfffef74e1a | 628444899 | 2 | -82 | 7,2 | undefined | undefined | undefined
test_04_02_19 | pycomarduino | 0058924AB98D5AD4 | 1 | 193 | WzJdIEQyMC8wNS8xOCB0MTI6MDAgVzAwMDAgVDAwMDAgPyAxICAgAA== | [2] D20/05/18 t12:00 W0000 T0000 ? 1 | 2020-06-18T20:08:11.464289124Z | 868,1 | LORA | SF7BW125 | 4/5 | undefined | eui-b827ebfffef74e1a | 825482971 | 0 | -82 | 9,2 | undefined | undefined | undefined
test_04_02_19 | pycomarduino | 0058924AB98D5AD4 | 1 | 194 | WzNdIEQyMC8wNS8xOCB0MTI6MDAgVzAwMDAgVDAwMDAgPyAxICAgAA== | [3] D20/05/18 t12:00 W0000 T0000 ? 1 | 2020-06-18T20:08:42.091110492Z | 867,9 | LORA | SF7BW125 | 4/5 | undefined | eui-b827ebfffef74e1a | 856167244 | 7 | -85 | 11 | undefined | undefined | undefined
test_04_02_19 | pycomarduino | 0058924AB98D5AD4 | 1 | 196 | WzVdIEQyMC8wNS8xOCB0MTI6MDAgVzAwMDAgVDAwMDAgPyAxICAgAA== | [5] D20/05/18 t12:00 W0000 T0000 ? 1 | 2020-06-18T20:09:54.369524491Z | 868,5 | LORA | SF7BW125 | 4/5 | undefined | eui-fcc23dfffe0b696a | 1837910875 | 2 | -111 | -3,2 | undefined | undefined | undefined | eui-b827ebfffef74e1a | 928444323 | 2 | -82 | 8,5 | undefined | undefined | undefined
test_04_02_19 | pycomarduino | 0058924AB98D5AD4 | 1 | 197 | WzJdIEQyMC8wNS8xOCB0MTI6MDAgVzAwMDAgVDAwMDAgPyAxICAgAA== | [2] D20/05/18 t12:00 W0000 T0000 ? 1 | 2020-06-18T20:13:11.414535497Z | 868,1 | LORA | SF7BW125 | 4/5 | undefined | eui-b827ebfffef74e1a | 1125485051 | 0 | -83 | 10 | undefined | undefined | undefined
test_04_02_19 | pycomarduino | 0058924AB98D5AD4 | 1 | 198 | WzNdIEQyMC8wNS8xOCB0MTI6MDAgVzAwMDAgVDAwMDAgPyAxICAgAA== | [3] D20/05/18 t12:00 W0000 T0000 ? 1 | 2020-06-18T20:13:42.123878203Z | 867,1 | LORA | SF7BW125 | 4/5 | undefined | eui-fcc23dfffe0b696a | 2065634275 | 3 | -115 | -6,2 | undefined | undefined | undefined | eui-b827ebfffef74e1a | 1156167819 | 3 | -87 | 9,2 | undefined | undefined | undefined
test_04_02_19 | pycomarduino | 0058924AB98D5AD4 | 1 | 199 | WzRdIEQyMC8wNS8xOCB0MTI6MDAgVzAwMDAgVDAwMDAgPyAxICAgAA== | [4] D20/05/18 t12:00 W0000 T0000 ? 1 | 2020-06-18T20:14:27.558600372Z | 868,3 | LORA | SF7BW125 | 4/5 | undefined | eui-b827ebfffef74e1a | 1201609331 | 1 | -82 | 10,2 | undefined | undefined | undefined
test_04_02_19 | pycomarduino | 0058924AB98D5AD4 | 1 | 200 | WzVdIEQyMC8wNS8xOCB0MTI6MDAgVzAwMDAgVDAwMDAgPyAxICAgAA== | [5] D20/05/18 t12:00 W0000 T0000 ? 1 | 2020-06-18T20:14:54.372803788Z | 868,5 | LORA | SF7BW125 | 4/5 | undefined | eui-b827ebfffef74e1a | 1228445827 | 2 | -81 | 7,5 | undefined | undefined | undefined
test_04_02_19 | pycomarduino | 0058924AB98D5AD4 | 1 | 201 | WzJdIEQyMC8wNS8xOCB0MTI6MDAgVzAwMDAgVDAwMDAgPyAxICAgAA== | [2] D20/05/18 t12:00 W0000 T0000 ? 1 | 2020-06-18T20:18:11.419287895Z | 868,1 | LORA | SF7BW125 | 4/5 | undefined | eui-b827ebfffef74e1a | 1425485091 | 0 | -83 | 8,8 | undefined | undefined | undefined
test_04_02_19 | pycomarduino | 0058924AB98D5AD4 | 1 | 202 | WzNdIEQyMC8wNS8xOCB0MTI6MDAgVzAwMDAgVDAwMDAgPyAxICAgAA== | [3] D20/05/18 t12:00 W0000 T0000 ? 1 | 2020-06-18T20:18:42.093144685Z | 867,3 | LORA | SF7BW125 | 4/5 | undefined | eui-fcc23dfffe0b696a | 2365632587 | 4 | -112 | -4,8 | undefined | undefined | undefined | eui-b827ebfffef74e1a | 1456166259 | 4 | -82 | 9,2 | undefined | undefined | undefined
test_04_02_19 | pycomarduino | 0058924AB98D5AD4 | 1 | 203 | WzRdIEQyMC8wNS8xOCB0MTI6MDAgVzAwMDAgVDAwMDAgPyAxICAgAA== | [4] D20/05/18 t12:00 W0000 T0000 ? 1 | 2020-06-18T20:19:27.540642981Z | 868,3 | LORA | SF7BW125 | 4/5 | undefined | eui-b827ebfffef74e1a | 1501608419 | 1 | -83 | 10,2 | undefined | undefined | undefined
test_04_02_19 | pycomarduino | 0058924AB98D5AD4 | 1 | 204 | WzVdIEQyMC8wNS8xOCB0MTI6MDAgVzAwMDAgVDAwMDAgPyAxICAgAA== | [5] D20/05/18 t12:00 W0000 T0000 ? 1 | 2020-06-18T20:19:54.379838281Z | 868,5 | LORA | SF7BW125 | 4/5 | undefined | eui-fcc23dfffe0b696a | 2437911651 | 2 | -110 | -2,8 | undefined | undefined | undefined | eui-b827ebfffef74e1a | 1528445355 | 2 | -78 | 7,2 | undefined | undefined | undefined
test_04_02_19 | pycomarduino | 0058924AB98D5AD4 | 1 | 205 | WzJdIEQyMC8wNS8xOCB0MTI6MDAgVzAwMDAgVDAwMDAgPyAxICAgAA== | [2] D20/05/18 t12:00 W0000 T0000 ? 1 | 2020-06-18T20:23:11.419028764Z | 868,1 | LORA | SF7BW125 | 4/5 | undefined | eui-b827ebfffef74e1a | 1725485195 | 0 | -82 | 9,8 | undefined | undefined | undefined
test_04_02_19 | pycomarduino | 0058924AB98D5AD4 | 1 | 206 | WzNdIEQyMC8wNS8xOCB0MTI6MDAgVzAwMDAgVDAwMDAgPyAxICAgAA== | [3] D20/05/18 t12:00 W0000 T0000 ? 1 | 2020-06-18T20:23:42.100026069Z | 867,5 | LORA | SF7BW125 | 4/5 | undefined | eui-b827ebfffef74e1a | 1756164708 | 5 | -82 | 8 | undefined | undefined | undefined
test_04_02_19 | pycomarduino | 0058924AB98D5AD4 | 1 | 207 | WzRdIEQyMC8wNS8xOCB0MTI6MDAgVzAwMDAgVDAwMDAgPyAxICAgAA== | [4] D20/05/18 t12:00 W0000 T0000 ? 1 | 2020-06-18T20:24:27.533575168Z | 868,3 | LORA | SF7BW125 | 4/5 | undefined | eui-b827ebfffef74e1a | 1801607595 | 1 | -80 | 10,2 | undefined | undefined | undefined
test_04_02_19 | pycomarduino | 0058924AB98D5AD4 | 1 | 208 | WzVdIEQyMC8wNS8xOCB0MTI6MDAgVzAwMDAgVDAwMDAgPyAxICAgAA== | [5] D20/05/18 t12:00 W0000 T0000 ? 1 | 2020-06-18T20:24:54.373482469Z | 868,5 | LORA | SF7BW125 | 4/5 | undefined | eui-fcc23dfffe0b696a | 2737910955 | 2 | -112 | -5,5 | undefined | undefined | undefined | eui-b827ebfffef74e1a | 1828444787 | 2 | -78 | 7,8 | undefined | undefined | undefined
test_04_02_19 | pycomarduino | 0058924AB98D5AD4 | 1 | 209 | WzJdIEQyMC8wNS8xOCB0MTI6MDAgVzAwMDAgVDAwMDAgPyAxICAgAA== | [2] D20/05/18 t12:00 W0000 T0000 ? 1 | 2020-06-18T20:28:11.411921652Z | 868,1 | LORA | SF7BW125 | 4/5 | undefined | eui-b827ebfffef74e1a | 2025487307 | 0 | -83 | 10 | undefined | undefined | undefined
test_04_02_19 | pycomarduino | 0058924AB98D5AD4 | 1 | 210 | WzNdIEQyMC8wNS8xOCB0MTI6MDAgVzAwMDAgVDAwMDAgPyAxICAgAA== | [3] D20/05/18 t12:00 W0000 T0000 ? 1 | 2020-06-18T20:28:42.096300858Z | 867,7 | LORA | SF7BW125 | 4/5 | undefined | eui-b827ebfffef74e1a | 2056165188 | 6 | -83 | 8 | undefined | undefined | undefined
test_04_02_19 | pycomarduino | 0058924AB98D5AD4 | 1 | 211 | WzRdIEQyMC8wNS8xOCB0MTI6MDAgVzAwMDAgVDAwMDAgPyAxICAgAA== | [4] D20/05/18 t12:00 W0000 T0000 ? 1 | 2020-06-18T20:29:27.531775459Z | 868,3 | LORA | SF7BW125 | 4/5 | undefined | eui-b827ebfffef74e1a | 2101608843 | 1 | -82 | 9,8 | undefined | undefined | undefined
test_04_02_19 | pycomarduino | 0058924AB98D5AD4 | 1 | 212 | WzVdIEQyMC8wNS8xOCB0MTI6MDAgVzAwMDAgVDAwMDAgPyAxICAgAA== | [5] D20/05/18 t12:00 W0000 T0000 ? 1 | 2020-06-18T20:29:54.37339936Z | 868,5 | LORA | SF7BW125 | 4/5 | undefined | eui-fcc23dfffe0b696a | 3037912347 | 2 | -110 | -3,2 | undefined | undefined | undefined | eui-b827ebfffef74e1a | 2128446299 | 2 | -81 | 8,8 | undefined | undefined | undefined
test_04_02_19 | pycomarduino | 0058924AB98D5AD4 | 1 | 213 | WzJdIEQyMC8wNS8xOCB0MTI6MDAgVzAwMDAgVDAwMDAgPyAxICAgAA== | [2] D20/05/18 t12:00 W0000 T0000 ? 1 | 2020-06-18T20:33:11.411777343Z | 868,1 | LORA | SF7BW125 | 4/5 | undefined | eui-b827ebfffef74e1a | 2325487347 | 0 | -85 | 10,5 | undefined | undefined | undefined
test_04_02_19 | pycomarduino | 0058924AB98D5AD4 | 1 | 214 | WzNdIEQyMC8wNS8xOCB0MTI6MDAgVzAwMDAgVDAwMDAgPyAxICAgAA== | [3] D20/05/18 t12:00 W0000 T0000 ? 1 | 2020-06-18T20:33:42.713947871Z | 867,9 | LORA | SF7BW125 | 4/5 | undefined | eui-b827ebfffef74e1a | 2356163740 | 7 | -84 | 9,5 | undefined | undefined | undefined
test_04_02_19 | pycomarduino | 0058924AB98D5AD4 | 1 | 215 | WzRdIEQyMC8wNS8xOCB0MTI6MDAgVzAwMDAgVDAwMDAgPyAxICAgAA== | [4] D20/05/18 t12:00 W0000 T0000 ? 1 | 2020-06-18T20:34:27.534240351Z | 868,3 | LORA | SF7BW125 | 4/5 | undefined | eui-b827ebfffef74e1a | 2401608051 | 1 | -81 | 9,5 | undefined | undefined | undefined
test_04_02_19 | pycomarduino | 0058924AB98D5AD4 | 1 | 216 | WzVdIEQyMC8wNS8xOCB0MTI6MDAgVzAwMDAgVDAwMDAgPyAxICAgAA== | [5] D20/05/18 t12:00 W0000 T0000 ? 1 | 2020-06-18T20:34:54.372639551Z | 868,5 | LORA | SF7BW125 | 4/5 | undefined | eui-fcc23dfffe0b696a | 3337911763 | 2 | -111 | -2,2 | undefined | undefined | undefined | eui-b827ebfffef74e1a | 2428445851 | 2 | -80 | 7,8 | undefined | undefined | undefined
test_04_02_19 | pycomarduino | 0058924AB98D5AD4 | 1 | 217 | WzJdIEQyMC8wNS8xOCB0MTI6MDAgVzAwMDAgVDAwMDAgPyAxICAgAA== | [2] D20/05/18 t12:00 W0000 T0000 ? 1 | 2020-06-18T20:38:11.415169684Z | 868,1 | LORA | SF7BW125 | 4/5 | undefined | eui-b827ebfffef74e1a | 2625487459 | 0 | -82 | 9,5 | undefined | undefined | undefined
test_04_02_19 | pycomarduino | 0058924AB98D5AD4 | 1 | 218 | WzNdIEQyMC8wNS8xOCB0MTI6MDAgVzAwMDAgVDAwMDAgPyAxICAgAA== | [3] D20/05/18 t12:00 W0000 T0000 ? 1 | 2020-06-18T20:38:42.09488498Z | 867,1 | LORA | SF7BW125 | 4/5 | undefined | eui-fcc23dfffe0b696a | 3565628075 | 3 | -113 | -5,8 | undefined | undefined | undefined | eui-b827ebfffef74e1a | 2656162259 | 3 | -85 | 9,5 | undefined | undefined | undefined
test_04_02_19 | pycomarduino | 0058924AB98D5AD4 | 1 | 219 | WzRdIEQyMC8wNS8xOCB0MTI6MDAgVzAwMDAgVDAwMDAgPyAxICAgAA== | [4] D20/05/18 t12:00 W0000 T0000 ? 1 | 2020-06-18T20:39:27.535993096Z | 868,3 | LORA | SF7BW125 | 4/5 | undefined | eui-b827ebfffef74e1a | 2701607259 | 1 | -80 | 9,5 | undefined | undefined | undefined
test_04_02_19 | pycomarduino | 0058924AB98D5AD4 | 1 | 220 | WzVdIEQyMC8wNS8xOCB0MTI6MDAgVzAwMDAgVDAwMDAgPyAxICAgAA== | [5] D20/05/18 t12:00 W0000 T0000 ? 1 | 2020-06-18T20:39:54.368819337Z | 868,5 | LORA | SF7BW125 | 4/5 | undefined | eui-fcc23dfffe0b696a | 3637911099 | 2 | -111 | -4,5 | undefined | undefined | undefined | eui-b827ebfffef74e1a | 2728445315 | 2 | -83 | 7,8 | undefined | undefined | undefined
test_04_02_19 | pycomarduino | 0058924AB98D5AD4 | 1 | 221 | WzJdIEQyMC8wNS8xOCB0MTI6MDAgVzAwMDAgVDAwMDAgPyAxICAgAA== | [2] D20/05/18 t12:00 W0000 T0000 ? 1 | 2020-06-18T20:43:11.420377672Z | 868,1 | LORA | SF7BW125 | 4/5 | undefined | eui-b827ebfffef74e1a | 2925489635 | 0 | -84 | 10,8 | undefined | undefined | undefined
test_04_02_19 | pycomarduino | 0058924AB98D5AD4 | 1 | 222 | WzNdIEQyMC8wNS8xOCB0MTI6MDAgVzAwMDAgVDAwMDAgPyAxICAgAA== | [3] D20/05/18 t12:00 W0000 T0000 ? 1 | 2020-06-18T20:43:42.087796862Z | 867,3 | LORA | SF7BW125 | 4/5 | undefined | eui-fcc23dfffe0b696a | 3865628443 | 4 | -112 | -6,5 | undefined | undefined | undefined | eui-b827ebfffef74e1a | 2956162755 | 4 | -82 | 9,8 | undefined | undefined | undefined
test_04_02_19 | pycomarduino | 0058924AB98D5AD4 | 1 | 223 | WzRdIEQyMC8wNS8xOCB0MTI6MDAgVzAwMDAgVDAwMDAgPyAxICAgAA== | [4] D20/05/18 t12:00 W0000 T0000 ? 1 | 2020-06-18T20:44:27.53423178Z | 868,3 | LORA | SF7BW125 | 4/5 | undefined | eui-b827ebfffef74e1a | 3001608339 | 1 | -80 | 9,5 | undefined | undefined | undefined
test_04_02_19 | pycomarduino | 0058924AB98D5AD4 | 1 | 224 | WzVdIEQyMC8wNS8xOCB0MTI6MDAgVzAwMDAgVDAwMDAgPyAxICAgAA== | [5] D20/05/18 t12:00 W0000 T0000 ? 1 | 2020-06-18T20:44:54.380936628Z | 868,5 | LORA | SF7BW125 | 4/5 | undefined | eui-fcc23dfffe0b696a | 3937912467 | 2 | -111 | -5 | undefined | undefined | undefined | eui-b827ebfffef74e1a | 3028446811 | 2 | -82 | 8 | undefined | undefined | undefined
test_04_02_19 | pycomarduino | 0058924AB98D5AD4 | 1 | 225 | WzJdIEQyMC8wNS8xOCB0MTI6MDAgVzAwMDAgVDAwMDAgPyAxICAgAA== | [2] D20/05/18 t12:00 W0000 T0000 ? 1 | 2020-06-18T20:48:11.428734561Z | 868,1 | LORA | SF7BW125 | 4/5 | undefined | eui-b827ebfffef74e1a | 3225489643 | 0 | -81 | 9,5 | undefined | undefined | undefined
test_04_02_19 | pycomarduino | 0058924AB98D5AD4 | 1 | 226 | WzNdIEQyMC8wNS8xOCB0MTI6MDAgVzAwMDAgVDAwMDAgPyAxICAgAA== | [3] D20/05/18 t12:00 W0000 T0000 ? 1 | 2020-06-18T20:48:42.120678463Z | 867,5 | LORA | SF7BW125 | 4/5 | undefined | eui-b827ebfffef74e1a | 3256161116 | 5 | -82 | 7,8 | undefined | undefined | undefined
test_04_02_19 | pycomarduino | 0058924AB98D5AD4 | 1 | 227 | WzRdIEQyMC8wNS8xOCB0MTI6MDAgVzAwMDAgVDAwMDAgPyAxICAgAA== | [4] D20/05/18 t12:00 W0000 T0000 ? 1 | 2020-06-18T20:49:27.533222665Z | 868,3 | LORA | SF7BW125 | 4/5 | undefined | eui-b827ebfffef74e1a | 3301607555 | 1 | -80 | 9,8 | undefined | undefined | undefined
test_04_02_19 | pycomarduino | 0058924AB98D5AD4 | 1 | 228 | WzVdIEQyMC8wNS8xOCB0MTI6MDAgVzAwMDAgVDAwMDAgPyAxICAgAA== | [5] D20/05/18 t12:00 W0000 T0000 ? 1 | 2020-06-18T20:49:54.380547613Z | 868,5 | LORA | SF7BW125 | 4/5 | undefined | eui-fcc23dfffe0b696a | 4237911875 | 2 | -111 | -3,2 | undefined | undefined | undefined | eui-b827ebfffef74e1a | 3328446339 | 2 | -81 | 7,2 | undefined | undefined | undefined
test_04_02_19 | pycomarduino | 0058924AB98D5AD4 | 1 | 229 | WzJdIEQyMC8wNS8xOCB0MTI6MDAgVzAwMDAgVDAwMDAgPyAxICAgAA== | [2] D20/05/18 t12:00 W0000 T0000 ? 1 | 2020-06-18T20:53:11.438492451Z | 868,1 | LORA | SF7BW125 | 4/5 | undefined | eui-b827ebfffef74e1a | 3525491747 | 0 | -84 | 10,8 | undefined | undefined | undefined
test_04_02_19 | pycomarduino | 0058924AB98D5AD4 | 1 | 231 | WzRdIEQyMC8wNS8xOCB0MTI6MDAgVzAwMDAgVDAwMDAgPyAxICAgAA== | [4] D20/05/18 t12:00 W0000 T0000 ? 1 | 2020-06-18T20:54:27.541739732Z | 868,3 | LORA | SF7BW125 | 4/5 | undefined | eui-b827ebfffef74e1a | 3601608803 | 1 | -81 | 9,5 | undefined | undefined | undefined
test_04_02_19 | pycomarduino | 0058924AB98D5AD4 | 1 | 232 | WzVdIEQyMC8wNS8xOCB0MTI6MDAgVzAwMDAgVDAwMDAgPyAxICAgAA== | [5] D20/05/18 t12:00 W0000 T0000 ? 1 | 2020-06-18T20:54:54.379011161Z | 868,5 | LORA | SF7BW125 | 4/5 | undefined | eui-fcc23dfffe0b696a | 242945979 | 2 | -110 | -3,8 | undefined | undefined | undefined | eui-b827ebfffef74e1a | 3628447867 | 2 | -81 | 8,2 | undefined | undefined | undefined
test_04_02_19 | pycomarduino | 0058924AB98D5AD4 | 1 | 233 | WzJdIEQyMC8wNS8xOCB0MTI6MDAgVzAwMDAgVDAwMDAgPyAxICAgAA== | [2] D20/05/18 t12:00 W0000 T0000 ? 1 | 2020-06-18T20:58:11.425691962Z | 868,1 | LORA | SF7BW125 | 4/5 | undefined | eui-b827ebfffef74e1a | 3825491787 | 0 | -84 | 9,8 | undefined | undefined | undefined
test_04_02_19 | pycomarduino | 0058924AB98D5AD4 | 1 | 234 | WzNdIEQyMC8wNS8xOCB0MTI6MDAgVzAwMDAgVDAwMDAgPyAxICAgAA== | [3] D20/05/18 t12:00 W0000 T0000 ? 1 | 2020-06-18T20:58:42.084104561Z | 867,9 | LORA | SF7BW125 | 4/5 | undefined | eui-fcc23dfffe0b696a | 470658164 | 7 | -115 | -6,8 | undefined | undefined | undefined | eui-b827ebfffef74e1a | 3856160148 | 7 | -85 | 10,5 | undefined | undefined | undefined
test_04_02_19 | pycomarduino | 0058924AB98D5AD4 | 1 | 235 | WzRdIEQyMC8wNS8xOCB0MTI6MDAgVzAwMDAgVDAwMDAgPyAxICAgAA== | [4] D20/05/18 t12:00 W0000 T0000 ? 1 | 2020-06-18T20:59:27.5422641Z | 868,3 | LORA | SF7BW125 | 4/5 | undefined | eui-b827ebfffef74e1a | 3901607915 | 1 | -82 | 9,5 | undefined | undefined | undefined
test_04_02_19 | pycomarduino | 0058924AB98D5AD4 | 1 | 236 | WzVdIEQyMC8wNS8xOCB0MTI6MDAgVzAwMDAgVDAwMDAgPyAxICAgAA== | [5] D20/05/18 t12:00 W0000 T0000 ? 1 | 2020-06-18T20:59:54.376626628Z | 868,5 | LORA | SF7BW125 | 4/5 | undefined | eui-fcc23dfffe0b696a | 542945299 | 2 | -111 | -3,2 | undefined | undefined | undefined | eui-b827ebfffef74e1a | 3928447315 | 2 | -79 | 8 | undefined | undefined | undefined
test_04_02_19 | pycomarduino | 0058924AB98D5AD4 | 1 | 237 | WzJdIEQyMC8wNS8xOCB0MTI6MDAgVzAwMDAgVDAwMDAgPyAxICAgAA== | [2] D20/05/18 t12:00 W0000 T0000 ? 1 | 2020-06-18T21:03:11.421283228Z | 868,1 | LORA | SF7BW125 | 4/5 | undefined | eui-b827ebfffef74e1a | 4125491891 | 0 | -83 | 10,2 | undefined | undefined | undefined
test_04_02_19 | pycomarduino | 0058924AB98D5AD4 | 1 | 238 | WzNdIEQyMC8wNS8xOCB0MTI6MDAgVzAwMDAgVDAwMDAgPyAxICAgAA== | [3] D20/05/18 t12:00 W0000 T0000 ? 1 | 2020-06-18T21:03:42.091128532Z | 867,1 | LORA | SF7BW125 | 4/5 | undefined | eui-fcc23dfffe0b696a | 770656563 | 3 | -113 | -7,2 | undefined | undefined | undefined | eui-b827ebfffef74e1a | 4156158675 | 3 | -85 | 9,2 | undefined | undefined | undefined
test_04_02_19 | pycomarduino | 0058924AB98D5AD4 | 1 | 239 | WzRdIEQyMC8wNS8xOCB0MTI6MDAgVzAwMDAgVDAwMDAgPyAxICAgAA== | [4] D20/05/18 t12:00 W0000 T0000 ? 1 | 2020-06-18T21:04:27.556838475Z | 868,3 | LORA | SF7BW125 | 4/5 | undefined | eui-b827ebfffef74e1a | 4201607115 | 1 | -81 | 9,8 | undefined | undefined | undefined
test_04_02_19 | pycomarduino | 0058924AB98D5AD4 | 1 | 240 | WzVdIEQyMC8wNS8xOCB0MTI6MDAgVzAwMDAgVDAwMDAgPyAxICAgAA== | [5] D20/05/18 t12:00 W0000 T0000 ? 1 | 2020-06-18T21:04:54.376617896Z | 868,5 | LORA | SF7BW125 | 4/5 | undefined | eui-fcc23dfffe0b696a | 842944595 | 2 | -111 | -2,2 | undefined | undefined | undefined | eui-b827ebfffef74e1a | 4228446731 | 2 | -82 | 7,5 | undefined | undefined | undefined
test_04_02_19 | pycomarduino | 0058924AB98D5AD4 | 1 | 241 | WzJdIEQyMC8wNS8xOCB0MTI6MDAgVzAwMDAgVDAwMDAgPyAxICAgAA== | [2] D20/05/18 t12:00 W0000 T0000 ? 1 | 2020-06-18T21:08:11.425747798Z | 868,1 | LORA | SF7BW125 | 4/5 | undefined | eui-b827ebfffef74e1a | 130526707 | 0 | -84 | 9 | undefined | undefined | undefined
test_04_02_19 | pycomarduino | 0058924AB98D5AD4 | 1 | 242 | WzNdIEQyMC8wNS8xOCB0MTI6MDAgVzAwMDAgVDAwMDAgPyAxICAgAA== | [3] D20/05/18 t12:00 W0000 T0000 ? 1 | 2020-06-18T21:08:42.085190398Z | 867,3 | LORA | SF7BW125 | 4/5 | undefined | eui-fcc23dfffe0b696a | 1070656955 | 4 | -112 | -3,8 | undefined | undefined | undefined | eui-b827ebfffef74e1a | 161191891 | 4 | -83 | 9 | undefined | undefined | undefined
test_04_02_19 | pycomarduino | 0058924AB98D5AD4 | 1 | 243 | WzRdIEQyMC8wNS8xOCB0MTI6MDAgVzAwMDAgVDAwMDAgPyAxICAgAA== | [4] D20/05/18 t12:00 W0000 T0000 ? 1 | 2020-06-18T21:09:27.540153335Z | 868,3 | LORA | SF7BW125 | 4/5 | undefined | eui-b827ebfffef74e1a | 206641011 | 1 | -83 | 10,2 | undefined | undefined | undefined
test_04_02_19 | pycomarduino | 0058924AB98D5AD4 | 1 | 244 | WzVdIEQyMC8wNS8xOCB0MTI6MDAgVzAwMDAgVDAwMDAgPyAxICAgAA== | [5] D20/05/18 t12:00 W0000 T0000 ? 1 | 2020-06-18T21:09:54.380965967Z | 868,5 | LORA | SF7BW125 | 4/5 | undefined | eui-fcc23dfffe0b696a | 1142945987 | 2 | -111 | -2,8 | undefined | undefined | undefined | eui-b827ebfffef74e1a | 233480963 | 2 | -80 | 8,2 | undefined | undefined | undefined
test_04_02_19 | pycomarduino | 0058924AB98D5AD4 | 1 | 245 | WzJdIEQyMC8wNS8xOCB0MTI6MDAgVzAwMDAgVDAwMDAgPyAxICAgAA== | [2] D20/05/18 t12:00 W0000 T0000 ? 1 | 2020-06-18T21:13:11.426902336Z | 868,1 | LORA | SF7BW125 | 4/5 | undefined | eui-b827ebfffef74e1a | 430526747 | 0 | -84 | 10,2 | undefined | undefined | undefined
test_04_02_19 | pycomarduino | 0058924AB98D5AD4 | 1 | 246 | WzNdIEQyMC8wNS8xOCB0MTI6MDAgVzAwMDAgVDAwMDAgPyAxICAgAA== | [3] D20/05/18 t12:00 W0000 T0000 ? 1 | 2020-06-18T21:13:42.086629224Z | 867,5 | LORA | SF7BW125 | 4/5 | undefined | eui-b827ebfffef74e1a | 461190348 | 5 | -83 | 7,2 | undefined | undefined | undefined
test_04_02_19 | pycomarduino | 0058924AB98D5AD4 | 1 | 247 | WzRdIEQyMC8wNS8xOCB0MTI6MDAgVzAwMDAgVDAwMDAgPyAxICAgAA== | [4] D20/05/18 t12:00 W0000 T0000 ? 1 | 2020-06-18T21:14:27.571820971Z | 868,3 | LORA | SF7BW125 | 4/5 | undefined | eui-b827ebfffef74e1a | 506640115 | 1 | -82 | 10,5 | undefined | undefined | undefined
test_04_02_19 | pycomarduino | 0058924AB98D5AD4 | 1 | 248 | WzVdIEQyMC8wNS8xOCB0MTI6MDAgVzAwMDAgVDAwMDAgPyAxICAgAA== | [5] D20/05/18 t12:00 W0000 T0000 ? 1 | 2020-06-18T21:14:54.455770112Z | 868,5 | LORA | SF7BW125 | 4/5 | undefined | eui-fcc23dfffe0b696a | 1442945299 | 2 | -112 | -2 | undefined | undefined | undefined | eui-b827ebfffef74e1a | 533480395 | 2 | -79 | 7,8 | undefined | undefined | undefined
test_04_02_19 | pycomarduino | 0058924AB98D5AD4 | 1 | 249 | WzJdIEQyMC8wNS8xOCB0MTI6MDAgVzAwMDAgVDAwMDAgPyAxICAgAA== | [2] D20/05/18 t12:00 W0000 T0000 ? 1 | 2020-06-18T21:18:11.427886558Z | 868,1 | LORA | SF7BW125 | 4/5 | undefined | eui-b827ebfffef74e1a | 730526787 | 0 | -83 | 10,2 | undefined | undefined | undefined
test_04_02_19 | pycomarduino | 0058924AB98D5AD4 | 1 | 250 | WzNdIEQyMC8wNS8xOCB0MTI6MDAgVzAwMDAgVDAwMDAgPyAxICAgAA== | [3] D20/05/18 t12:00 W0000 T0000 ? 1 | 2020-06-18T21:18:42.080903042Z | 867,7 | LORA | SF7BW125 | 4/5 | undefined | eui-fcc23dfffe0b696a | 1670653524 | 6 | -113 | -7,5 | undefined | undefined | undefined | eui-b827ebfffef74e1a | 761188716 | 6 | -81 | 9 | undefined | undefined | undefined
test_04_02_19 | pycomarduino | 0058924AB98D5AD4 | 1 | 251 | WzRdIEQyMC8wNS8xOCB0MTI6MDAgVzAwMDAgVDAwMDAgPyAxICAgAA== | [4] D20/05/18 t12:00 W0000 T0000 ? 1 | 2020-06-18T21:19:27.529351573Z | 868,3 | LORA | SF7BW125 | 4/5 | undefined | eui-b827ebfffef74e1a | 806639347 | 1 | -80 | 9,5 | undefined | undefined | undefined
test_04_02_19 | pycomarduino | 0058924AB98D5AD4 | 1 | 252 | WzVdIEQyMC8wNS8xOCB0MTI6MDAgVzAwMDAgVDAwMDAgPyAxICAgAA== | [5] D20/05/18 t12:00 W0000 T0000 ? 1 | 2020-06-18T21:19:54.376472496Z | 868,5 | LORA | SF7BW125 | 4/5 | undefined | eui-fcc23dfffe0b696a | 1742944659 | 2 | -111 | -5,5 | undefined | undefined | undefined | eui-b827ebfffef74e1a | 833479891 | 2 | -79 | 8 | undefined | undefined | undefined
test_04_02_19 | pycomarduino | 0058924AB98D5AD4 | 1 | 253 | WzJdIEQyMC8wNS8xOCB0MTI6MDAgVzAwMDAgVDAwMDAgPyAxICAgAA== | [2] D20/05/18 t12:00 W0000 T0000 ? 1 | 2020-06-18T21:23:11.447514889Z | 868,1 | LORA | SF7BW125 | 4/5 | undefined | eui-b827ebfffef74e1a | 1030528859 | 0 | -85 | 10,5 | undefined | undefined | undefined
test_04_02_19 | pycomarduino | 0058924AB98D5AD4 | 1 | 254 | WzNdIEQyMC8wNS8xOCB0MTI6MDAgVzAwMDAgVDAwMDAgPyAxICAgAA== | [3] D20/05/18 t12:00 W0000 T0000 ? 1 | 2020-06-18T21:23:42.080115563Z | 867,9 | LORA | SF7BW125 | 4/5 | undefined | eui-b827ebfffef74e1a | 1061189276 | 7 | -85 | 10 | undefined | undefined | undefined
test_04_02_19 | pycomarduino | 0058924AB98D5AD4 | 1 | 255 | WzRdIEQyMC8wNS8xOCB0MTI6MDAgVzAwMDAgVDAwMDAgPyAxICAgAA== | [4] D20/05/18 t12:00 W0000 T0000 ? 1 | 2020-06-18T21:24:27.535854597Z | 868,3 | LORA | SF7BW125 | 4/5 | undefined | eui-b827ebfffef74e1a | 1106640483 | 1 | -83 | 10,2 | undefined | undefined | undefined
test_04_02_19 | pycomarduino | 0058924AB98D5AD4 | 1 | 256 | WzVdIEQyMC8wNS8xOCB0MTI6MDAgVzAwMDAgVDAwMDAgPyAxICAgAA== | [5] D20/05/18 t12:00 W0000 T0000 ? 1 | 2020-06-18T21:24:54.377856618Z | 868,5 | LORA | SF7BW125 | 4/5 | undefined | eui-fcc23dfffe0b696a | 2042946019 | 2 | -110 | -3,2 | undefined | undefined | undefined | eui-b827ebfffef74e1a | 1133481371 | 2 | -81 | 6,8 | undefined | undefined | undefined
test_04_02_19 | pycomarduino | 0058924AB98D5AD4 | 1 | 257 | WzJdIEQyMC8wNS8xOCB0MTI6MDAgVzAwMDAgVDAwMDAgPyAxICAgAA== | [2] D20/05/18 t12:00 W0000 T0000 ? 1 | 2020-06-18T21:28:11.425480034Z | 868,1 | LORA | SF7BW125 | 4/5 | undefined | eui-b827ebfffef74e1a | 1330528963 | 0 | -84 | 9,5 | undefined | undefined | undefined
test_04_02_19 | pycomarduino | 0058924AB98D5AD4 | 1 | 258 | WzNdIEQyMC8wNS8xOCB0MTI6MDAgVzAwMDAgVDAwMDAgPyAxICAgAA== | [3] D20/05/18 t12:00 W0000 T0000 ? 1 | 2020-06-18T21:28:42.077471041Z | 867,1 | LORA | SF7BW125 | 4/5 | undefined | eui-fcc23dfffe0b696a | 2270652251 | 3 | -113 | -4 | undefined | undefined | undefined | eui-b827ebfffef74e1a | 1361187699 | 3 | -85 | 9 | undefined | undefined | undefined
test_04_02_19 | pycomarduino | 0058924AB98D5AD4 | 1 | 259 | WzRdIEQyMC8wNS8xOCB0MTI6MDAgVzAwMDAgVDAwMDAgPyAxICAgAA== | [4] D20/05/18 t12:00 W0000 T0000 ? 1 | 2020-06-18T21:29:27.534484357Z | 868,3 | LORA | SF7BW125 | 4/5 | undefined | eui-b827ebfffef74e1a | 1406639563 | 1 | -82 | 9,2 | undefined | undefined | undefined
test_04_02_19 | pycomarduino | 0058924AB98D5AD4 | 1 | 260 | WzVdIEQyMC8wNS8xOCB0MTI6MDAgVzAwMDAgVDAwMDAgPyAxICAgAA== | [5] D20/05/18 t12:00 W0000 T0000 ? 1 | 2020-06-18T21:29:54.378138586Z | 868,5 | LORA | SF7BW125 | 4/5 | undefined | eui-fcc23dfffe0b696a | 2342945403 | 2 | -111 | -2,2 | undefined | undefined | undefined | eui-b827ebfffef74e1a | 1433480883 | 2 | -82 | 7,5 | undefined | undefined | undefined
test_04_02_19 | pycomarduino | 0058924AB98D5AD4 | 1 | 261 | WzJdIEQyMC8wNS8xOCB0MTI6MDAgVzAwMDAgVDAwMDAgPyAxICAgAA== | [2] D20/05/18 t12:00 W0000 T0000 ? 1 | 2020-06-18T21:33:11.424013554Z | 868,1 | LORA | SF7BW125 | 4/5 | undefined | eui-b827ebfffef74e1a | 1630531027 | 0 | -85 | 10,2 | undefined | undefined | undefined
test_04_02_19 | pycomarduino | 0058924AB98D5AD4 | 1 | 262 | WzNdIEQyMC8wNS8xOCB0MTI6MDAgVzAwMDAgVDAwMDAgPyAxICAgAA== | [3] D20/05/18 t12:00 W0000 T0000 ? 1 | 2020-06-18T21:33:42.081897963Z | 867,3 | LORA | SF7BW125 | 4/5 | undefined | eui-fcc23dfffe0b696a | 2570652611 | 4 | -111 | -4,2 | undefined | undefined | undefined | eui-b827ebfffef74e1a | 1661188187 | 4 | -87 | 9,8 | undefined | undefined | undefined
test_04_02_19 | pycomarduino | 0058924AB98D5AD4 | 1 | 263 | WzRdIEQyMC8wNS8xOCB0MTI6MDAgVzAwMDAgVDAwMDAgPyAxICAgAA== | [4] D20/05/18 t12:00 W0000 T0000 ? 1 | 2020-06-18T21:34:27.62591212Z | 868,3 | LORA | SF7BW125 | 4/5 | undefined | eui-b827ebfffef74e1a | 1706640859 | 1 | -82 | 9,2 | undefined | undefined | undefined
test_04_02_19 | pycomarduino | 0058924AB98D5AD4 | 1 | 264 | WzVdIEQyMC8wNS8xOCB0MTI6MDAgVzAwMDAgVDAwMDAgPyAxICAgAA== | [5] D20/05/18 t12:00 W0000 T0000 ? 1 | 2020-06-18T21:34:54.376764006Z | 868,5 | LORA | SF7BW125 | 4/5 | undefined | eui-fcc23dfffe0b696a | 2642946731 | 2 | -112 | -2,5 | undefined | undefined | undefined | eui-b827ebfffef74e1a | 1733482339 | 2 | -83 | 7,2 | undefined | undefined | undefined
test_04_02_19 | pycomarduino | 0058924AB98D5AD4 | 1 | 265 | WzJdIEQyMC8wNS8xOCB0MTI6MDAgVzAwMDAgVDAwMDAgPyAxICAgAA== | [2] D20/05/18 t12:00 W0000 T0000 ? 1 | 2020-06-18T21:38:11.428217377Z | 868,1 | LORA | SF7BW125 | 4/5 | undefined | eui-b827ebfffef74e1a | 1930531067 | 0 | -84 | 9,5 | undefined | undefined | undefined
test_04_02_19 | pycomarduino | 0058924AB98D5AD4 | 1 | 266 | WzNdIEQyMC8wNS8xOCB0MTI6MDAgVzAwMDAgVDAwMDAgPyAxICAgAA== | [3] D20/05/18 t12:00 W0000 T0000 ? 1 | 2020-06-18T21:38:42.088315887Z | 867,5 | LORA | SF7BW125 | 4/5 | undefined | eui-b827ebfffef74e1a | 1961186700 | 5 | -84 | 7,5 | undefined | undefined | undefined
test_04_02_19 | pycomarduino | 0058924AB98D5AD4 | 1 | 267 | WzRdIEQyMC8wNS8xOCB0MTI6MDAgVzAwMDAgVDAwMDAgPyAxICAgAA== | [4] D20/05/18 t12:00 W0000 T0000 ? 1 | 2020-06-18T21:39:27.5377145Z | 868,3 | LORA | SF7BW125 | 4/5 | undefined | eui-b827ebfffef74e1a | 2006640051 | 1 | -82 | 9,5 | undefined | undefined | undefined
test_04_02_19 | pycomarduino | 0058924AB98D5AD4 | 1 | 268 | WzVdIEQyMC8wNS8xOCB0MTI6MDAgVzAwMDAgVDAwMDAgPyAxICAgAA== | [5] D20/05/18 t12:00 W0000 T0000 ? 1 | 2020-06-18T21:39:54.377268427Z | 868,5 | LORA | SF7BW125 | 4/5 | undefined | eui-fcc23dfffe0b696a | 2942946107 | 2 | -112 | -2 | undefined | undefined | undefined | eui-b827ebfffef74e1a | 2033481843 | 2 | -83 | 7,8 | undefined | undefined | undefined
test_04_02_19 | pycomarduino | 0058924AB98D5AD4 | 1 | 269 | WzJdIEQyMC8wNS8xOCB0MTI6MDAgVzAwMDAgVDAwMDAgPyAxICAgAA== | [2] D20/05/18 t12:00 W0000 T0000 ? 1 | 2020-06-18T21:43:11.427163497Z | 868,1 | LORA | SF7BW125 | 4/5 | undefined | eui-b827ebfffef74e1a | 2230531147 | 0 | -82 | 9,8 | undefined | undefined | undefined
test_04_02_19 | pycomarduino | 0058924AB98D5AD4 | 1 | 270 | WzNdIEQyMC8wNS8xOCB0MTI6MDAgVzAwMDAgVDAwMDAgPyAxICAgAA== | [3] D20/05/18 t12:00 W0000 T0000 ? 1 | 2020-06-18T21:43:42.078328503Z | 867,7 | LORA | SF7BW125 | 4/5 | undefined | eui-b827ebfffef74e1a | 2261185124 | 6 | -82 | 9 | undefined | undefined | undefined
test_04_02_19 | pycomarduino | 0058924AB98D5AD4 | 1 | 271 | WzRdIEQyMC8wNS8xOCB0MTI6MDAgVzAwMDAgVDAwMDAgPyAxICAgAA== | [4] D20/05/18 t12:00 W0000 T0000 ? 1 | 2020-06-18T21:44:27.53742792Z | 868,3 | LORA | SF7BW125 | 4/5 | undefined | eui-b827ebfffef74e1a | 2306639147 | 1 | -82 | 10,2 | undefined | undefined | undefined
test_04_02_19 | pycomarduino | 0058924AB98D5AD4 | 1 | 272 | WzVdIEQyMC8wNS8xOCB0MTI6MDAgVzAwMDAgVDAwMDAgPyAxICAgAA== | [5] D20/05/18 t12:00 W0000 T0000 ? 1 | 2020-06-18T21:44:54.380995849Z | 868,5 | LORA | SF7BW125 | 4/5 | undefined | eui-b827ebfffef74e1a | 2333481179 | 2 | -81 | 8 | undefined | undefined | undefined
test_04_02_19 | pycomarduino | 0058924AB98D5AD4 | 1 | 273 | WzJdIEQyMC8wNS8xOCB0MTI6MDAgVzAwMDAgVDAwMDAgPyAxICAgAA== | [2] D20/05/18 t12:00 W0000 T0000 ? 1 | 2020-06-18T21:48:11.426065355Z | 868,1 | LORA | SF7BW125 | 4/5 | undefined | eui-fcc23dfffe0b696a | 3439997275 | 0 | -112 | -5,5 | undefined | undefined | undefined | eui-b827ebfffef74e1a | 2530533227 | 0 | -83 | 10 | undefined | undefined | undefined
test_04_02_19 | pycomarduino | 0058924AB98D5AD4 | 1 | 274 | WzNdIEQyMC8wNS8xOCB0MTI6MDAgVzAwMDAgVDAwMDAgPyAxICAgAA== | [3] D20/05/18 t12:00 W0000 T0000 ? 1 | 2020-06-18T21:48:42.081024464Z | 867,9 | LORA | SF7BW125 | 4/5 | undefined | eui-fcc23dfffe0a9698 | 3472665620 | 7 | -114 | -8,2 | undefined | undefined | undefined | eui-b827ebfffef74e1a | 2561185612 | 7 | -83 | 9,5 | undefined | undefined | undefined
test_04_02_19 | pycomarduino | 0058924AB98D5AD4 | 1 | 275 | WzRdIEQyMC8wNS8xOCB0MTI6MDAgVzAwMDAgVDAwMDAgPyAxICAgAA== | [4] D20/05/18 t12:00 W0000 T0000 ? 1 | 2020-06-18T21:49:27.540756379Z | 868,3 | LORA | SF7BW125 | 4/5 | undefined | eui-b827ebfffef74e1a | 2606640379 | 1 | -80 | 9,5 | undefined | undefined | undefined
test_04_02_19 | pycomarduino | 0058924AB98D5AD4 | 1 | 276 | WzVdIEQyMC8wNS8xOCB0MTI6MDAgVzAwMDAgVDAwMDAgPyAxICAgAA== | [5] D20/05/18 t12:00 W0000 T0000 ? 1 | 2020-06-18T21:49:54.37659688Z | 868,5 | LORA | SF7BW125 | 4/5 | undefined | eui-fcc23dfffe0b696a | 3542946771 | 2 | -110 | -4 | undefined | undefined | undefined | eui-b827ebfffef74e1a | 2633482755 | 2 | -83 | 8 | undefined | undefined | undefined
test_04_02_19 | pycomarduino | 0058924AB98D5AD4 | 1 | 277 | WzJdIEQyMC8wNS8xOCB0MTI6MDAgVzAwMDAgVDAwMDAgPyAxICAgAA== | [2] D20/05/18 t12:00 W0000 T0000 ? 1 | 2020-06-18T21:53:11.430881442Z | 868,1 | LORA | SF7BW125 | 4/5 | undefined | eui-b827ebfffef74e1a | 2830533243 | 0 | -84 | 9,5 | undefined | undefined | undefined
test_04_02_19 | pycomarduino | 0058924AB98D5AD4 | 1 | 278 | WzNdIEQyMC8wNS8xOCB0MTI6MDAgVzAwMDAgVDAwMDAgPyAxICAgAA== | [3] D20/05/18 t12:00 W0000 T0000 ? 1 | 2020-06-18T21:53:42.077273047Z | 867,1 | LORA | SF7BW125 | 4/5 | undefined | eui-b827ebfffef74e1a | 2861184051 | 3 | -85 | 9,2 | undefined | undefined | undefined
test_04_02_19 | pycomarduino | 0058924AB98D5AD4 | 1 | 279 | WzRdIEQyMC8wNS8xOCB0MTI6MDAgVzAwMDAgVDAwMDAgPyAxICAgAA== | [4] D20/05/18 t12:00 W0000 T0000 ? 1 | 2020-06-18T21:54:27.53282726Z | 868,3 | LORA | SF7BW125 | 4/5 | undefined | eui-b827ebfffef74e1a | 2906639491 | 1 | -80 | 9,8 | undefined | undefined | undefined
test_04_02_19 | pycomarduino | 0058924AB98D5AD4 | 1 | 280 | WzVdIEQyMC8wNS8xOCB0MTI6MDAgVzAwMDAgVDAwMDAgPyAxICAgAA== | [5] D20/05/18 t12:00 W0000 T0000 ? 1 | 2020-06-18T21:54:54.371445262Z | 868,5 | LORA | SF7BW125 | 4/5 | undefined | eui-fcc23dfffe0b696a | 3842946075 | 2 | -111 | -8,5 | undefined | undefined | undefined | eui-b827ebfffef74e1a | 2933482187 | 2 | -82 | 8,2 | undefined | undefined | undefined
test_04_02_19 | pycomarduino | 0058924AB98D5AD4 | 1 | 281 | WzJdIEQyMC8wNS8xOCB0MTI6MDAgVzAwMDAgVDAwMDAgPyAxICAgAA== | [2] D20/05/18 t12:00 W0000 T0000 ? 1 | 2020-06-18T21:58:11.425538024Z | 868,1 | LORA | SF7BW125 | 4/5 | undefined | eui-b827ebfffef74e1a | 3130533371 | 0 | -83 | 9,2 | undefined | undefined | undefined
test_04_02_19 | pycomarduino | 0058924AB98D5AD4 | 1 | 282 | WzNdIEQyMC8wNS8xOCB0MTI6MDAgVzAwMDAgVDAwMDAgPyAxICAgAA== | [3] D20/05/18 t12:00 W0000 T0000 ? 1 | 2020-06-18T21:58:42.07499993Z | 867,3 | LORA | SF7BW125 | 4/5 | undefined | eui-fcc23dfffe0b696a | 4070646347 | 4 | -112 | -5,2 | undefined | undefined | undefined | eui-b827ebfffef74e1a | 3161182555 | 4 | -83 | 9,2 | undefined | undefined | undefined
test_04_02_19 | pycomarduino | 0058924AB98D5AD4 | 1 | 283 | WzRdIEQyMC8wNS8xOCB0MTI6MDAgVzAwMDAgVDAwMDAgPyAxICAgAA== | [4] D20/05/18 t12:00 W0000 T0000 ? 1 | 2020-06-18T21:59:27.529657043Z | 868,3 | LORA | SF7BW125 | 4/5 | undefined | eui-b827ebfffef74e1a | 3206638571 | 1 | -82 | 10 | undefined | undefined | undefined
test_04_02_19 | pycomarduino | 0058924AB98D5AD4 | 1 | 284 | WzVdIEQyMC8wNS8xOCB0MTI6MDAgVzAwMDAgVDAwMDAgPyAxICAgAA== | [5] D20/05/18 t12:00 W0000 T0000 ? 1 | 2020-06-18T21:59:54.409956765Z | 868,5 | LORA | SF7BW125 | 4/5 | undefined | eui-fcc23dfffe0b696a | 4142945467 | 2 | -111 | -2,5 | undefined | undefined | undefined | eui-b827ebfffef74e1a | 3233481715 | 2 | -82 | 7,8 | undefined | undefined | undefined
test_04_02_19 | pycomarduino | 0058924AB98D5AD4 | 1 | 285 | WzJdIEQyMC8wNS8xOCB0MTI6MDAgVzAwMDAgVDAwMDAgPyAxICAgAA== | [2] D20/05/18 t12:00 W0000 T0000 ? 1 | 2020-06-18T22:03:11.430232259Z | 868,1 | LORA | SF7BW125 | 4/5 | undefined | eui-b827ebfffef74e1a | 3430535427 | 0 | -84 | 9,5 | undefined | undefined | undefined
test_04_02_19 | pycomarduino | 0058924AB98D5AD4 | 1 | 286 | WzNdIEQyMC8wNS8xOCB0MTI6MDAgVzAwMDAgVDAwMDAgPyAxICAgAA== | [3] D20/05/18 t12:00 W0000 T0000 ? 1 | 2020-06-18T22:03:42.074436394Z | 867,5 | LORA | SF7BW125 | 4/5 | undefined | eui-fcc23dfffe0b696a | 75679396 | 5 | -112 | -4,8 | undefined | undefined | undefined | eui-b827ebfffef74e1a | 3461183020 | 5 | -83 | 7,8 | undefined | undefined | undefined
test_04_02_19 | pycomarduino | 0058924AB98D5AD4 | 1 | 287 | WzRdIEQyMC8wNS8xOCB0MTI6MDAgVzAwMDAgVDAwMDAgPyAxICAgAA== | [4] D20/05/18 t12:00 W0000 T0000 ? 1 | 2020-06-18T22:04:27.533449757Z | 868,3 | LORA | SF7BW125 | 4/5 | undefined | eui-b827ebfffef74e1a | 3506639867 | 1 | -80 | 9,8 | undefined | undefined | undefined
test_04_02_19 | pycomarduino | 0058924AB98D5AD4 | 1 | 289 | WzJdIEQyMC8wNS8xOCB0MTI6MDAgVzAwMDAgVDAwMDAgPyAxICAgAA== | [2] D20/05/18 t12:00 W0000 T0000 ? 1 | 2020-06-18T22:08:11.429501159Z | 868,1 | LORA | SF7BW125 | 4/5 | undefined | eui-b827ebfffef74e1a | 3730535531 | 0 | -82 | 9,2 | undefined | undefined | undefined
test_04_02_19 | pycomarduino | 0058924AB98D5AD4 | 1 | 290 | WzNdIEQyMC8wNS8xOCB0MTI6MDAgVzAwMDAgVDAwMDAgPyAxICAgAA== | [3] D20/05/18 t12:00 W0000 T0000 ? 1 | 2020-06-18T22:08:42.078929297Z | 867,7 | LORA | SF7BW125 | 4/5 | undefined | eui-b827ebfffef74e1a | 3761181452 | 6 | -83 | 9,2 | undefined | undefined | undefined
test_04_02_19 | pycomarduino | 0058924AB98D5AD4 | 1 | 291 | WzRdIEQyMC8wNS8xOCB0MTI6MDAgVzAwMDAgVDAwMDAgPyAxICAgAA== | [4] D20/05/18 t12:00 W0000 T0000 ? 1 | 2020-06-18T22:09:27.541732461Z | 868,3 | LORA | SF7BW125 | 4/5 | undefined | eui-b827ebfffef74e1a | 3806638971 | 1 | -81 | 9,5 | undefined | undefined | undefined
test_04_02_19 | pycomarduino | 0058924AB98D5AD4 | 1 | 292 | WzVdIEQyMC8wNS8xOCB0MTI6MDAgVzAwMDAgVDAwMDAgPyAxICAgAA== | [5] D20/05/18 t12:00 W0000 T0000 ? 1 | 2020-06-18T22:09:54.378646091Z | 868,5 | LORA | SF7BW125 | 4/5 | undefined | eui-fcc23dfffe0b696a | 447978883 | 2 | -110 | -2,8 | undefined | undefined | undefined | eui-b827ebfffef74e1a | 3833482667 | 2 | -81 | 8 | undefined | undefined | undefined
test_04_02_19 | pycomarduino | 0058924AB98D5AD4 | 1 | 293 | WzJdIEQyMC8wNS8xOCB0MTI6MDAgVzAwMDAgVDAwMDAgPyAxICAgAA== | [2] D20/05/18 t12:00 W0000 T0000 ? 1 | 2020-06-18T22:13:11.43145136Z | 868,1 | LORA | SF7BW125 | 4/5 | undefined | eui-fcc23dfffe0b696a | 645033699 | 0 | -115 | -6,2 | undefined | undefined | undefined | eui-b827ebfffef74e1a | 4030537571 | 0 | -82 | 10 | undefined | undefined | undefined
test_04_02_19 | pycomarduino | 0058924AB98D5AD4 | 1 | 294 | WzNdIEQyMC8wNS8xOCB0MTI6MDAgVzAwMDAgVDAwMDAgPyAxICAgAA== | [3] D20/05/18 t12:00 W0000 T0000 ? 1 | 2020-06-18T22:13:42.071933994Z | 867,9 | LORA | SF7BW125 | 4/5 | undefined | eui-fcc23dfffe0b696a | 675678116 | 7 | -113 | -5,2 | undefined | undefined | undefined | eui-b827ebfffef74e1a | 4061182004 | 7 | -84 | 9,5 | undefined | undefined | undefined
test_04_02_19 | pycomarduino | 0058924AB98D5AD4 | 1 | 295 | WzRdIEQyMC8wNS8xOCB0MTI6MDAgVzAwMDAgVDAwMDAgPyAxICAgAA== | [4] D20/05/18 t12:00 W0000 T0000 ? 1 | 2020-06-18T22:14:27.536442459Z | 868,3 | LORA | SF7BW125 | 4/5 | undefined | eui-b827ebfffef74e1a | 4106640203 | 1 | -83 | 10,5 | undefined | undefined | undefined
test_04_02_19 | pycomarduino | 0058924AB98D5AD4 | 1 | 296 | WzVdIEQyMC8wNS8xOCB0MTI6MDAgVzAwMDAgVDAwMDAgPyAxICAgAA== | [5] D20/05/18 t12:00 W0000 T0000 ? 1 | 2020-06-18T22:14:54.37606729Z | 868,5 | LORA | SF7BW125 | 4/5 | undefined | eui-fcc23dfffe0b696a | 747980227 | 2 | -112 | -2 | undefined | undefined | undefined | eui-b827ebfffef74e1a | 4133484147 | 2 | -79 | 7,5 | undefined | undefined | undefined
test_04_02_19 | pycomarduino | 0058924AB98D5AD4 | 1 | 297 | WzJdIEQyMC8wNS8xOCB0MTI6MDAgVzAwMDAgVDAwMDAgPyAxICAgAA== | [2] D20/05/18 t12:00 W0000 T0000 ? 1 | 2020-06-18T22:18:11.428969059Z | 868,1 | LORA | SF7BW125 | 4/5 | undefined | eui-b827ebfffef74e1a | 35570363 | 0 | -84 | 9,8 | undefined | undefined | undefined
test_04_02_19 | pycomarduino | 0058924AB98D5AD4 | 1 | 299 | WzRdIEQyMC8wNS8xOCB0MTI6MDAgVzAwMDAgVDAwMDAgPyAxICAgAA== | [4] D20/05/18 t12:00 W0000 T0000 ? 1 | 2020-06-18T22:19:27.530491557Z | 868,3 | LORA | SF7BW125 | 4/5 | undefined | eui-b827ebfffef74e1a | 111672019 | 1 | -83 | 10,2 | undefined | undefined | undefined
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
