ComNets-Bremen/MoleNet/experiments/2025-EWSN_Water_Sensors/readout/molly_mascot_digital.png

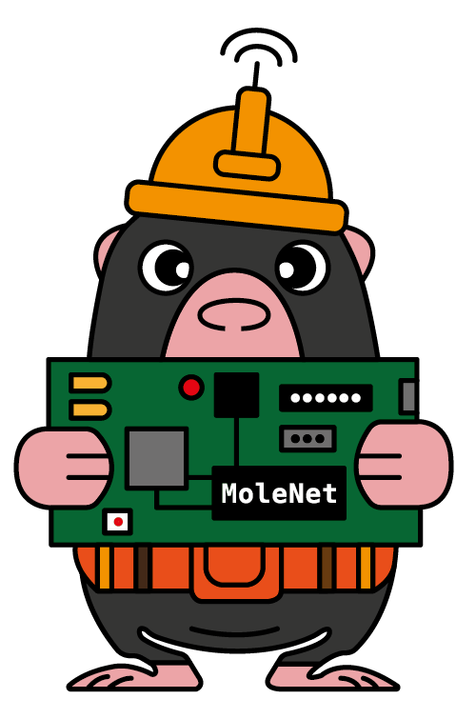
experiments/2025-EWSN_Water_Sensors/readout/molly_mascot_digital.png
