ComNets-Bremen/MoleNet/experiments/2026-power-consumption-and-voltage-measurement/data-sources/1stRun-pyscript.png

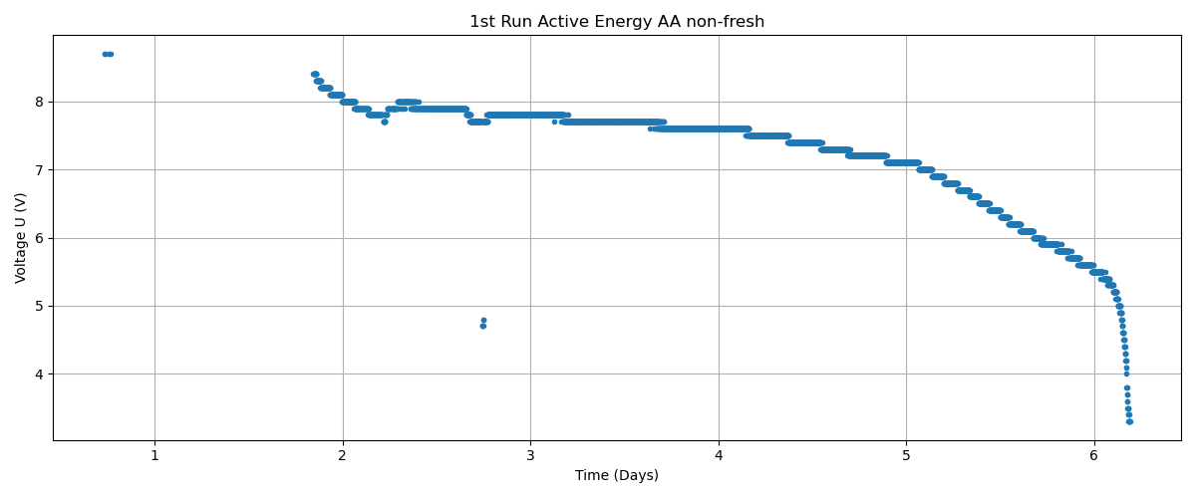
experiments/2026-power-consumption-and-voltage-measurement/data-sources/1stRun-pyscript.png
