ComNets-Bremen/MoleNet/experiments/2026-power-consumption-and-voltage-measurement/data-sources/active-energy.png

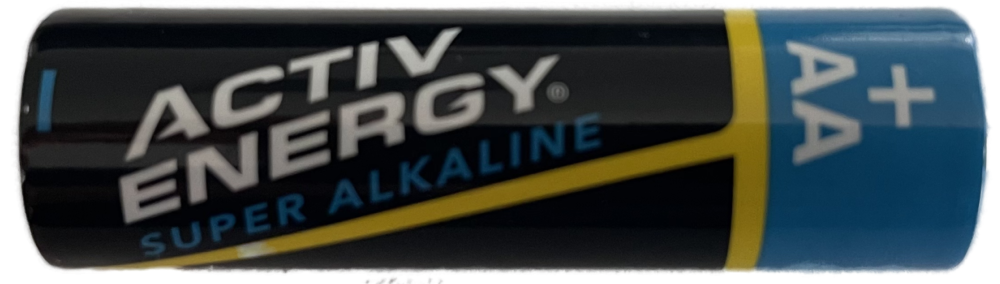
experiments/2026-power-consumption-and-voltage-measurement/data-sources/active-energy.png
