ComNets-Bremen/MoleNet/experiments/2026-power-consumption-and-voltage-measurement/data-sources/battery-images/IMG_7201 Large.jpeg

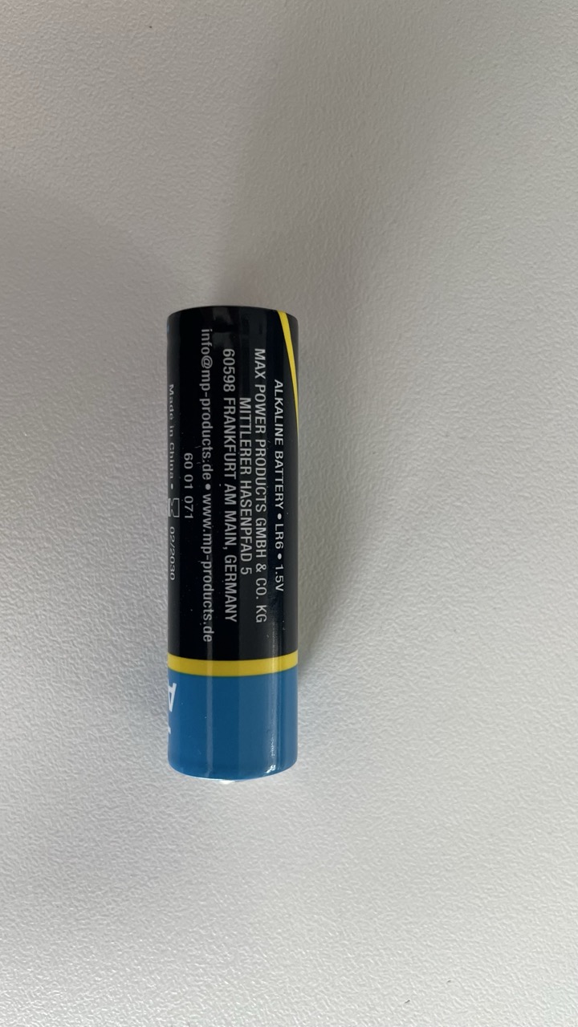
experiments/2026-power-consumption-and-voltage-measurement/data-sources/battery-images/IMG_7201 Large.jpeg
