ComNets-Bremen/MoleNet/experiments/2026-power-consumption-and-voltage-measurement/duracel-info/duracel-temp.png

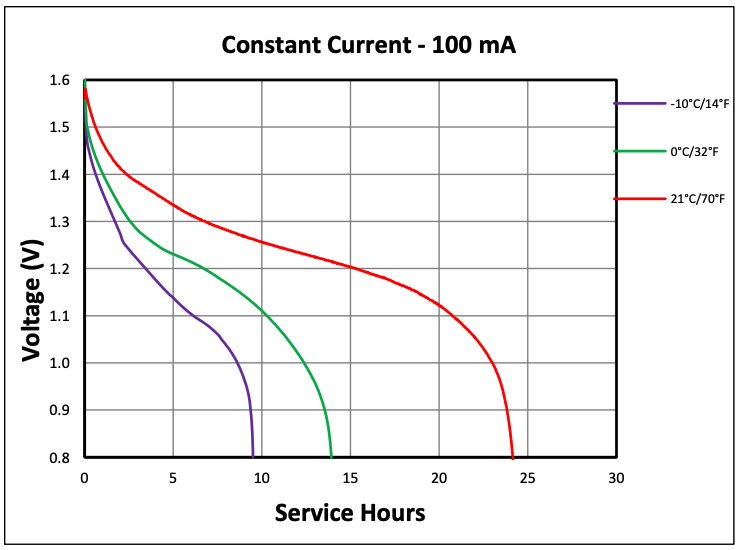
experiments/2026-power-consumption-and-voltage-measurement/duracel-info/duracel-temp.png
